KennethDoerflein/ESP32Clock/src/AlarmManager.cpp

/**
 * @file AlarmManager.cpp
 * @brief Implements the AlarmManager class for handling alarm ringing logic.
 *
 * This file contains the implementation of the AlarmManager, which controls
 * the physical buzzer, manages the alarm sound progression (ramping), and
 * handles auto-shutoff and resuming alarms after a reboot.
 */

#include "AlarmManager.h"
#include "Display.h"
#include "DisplayManager.h"
#include "SerialLog.h"
#include "ConfigManager.h"
#include "Constants.h"
#include "LockGuard.h"

/**
 * @brief Private constructor to enforce the singleton pattern.
 */
AlarmManager::AlarmManager() : _isRinging(false), _activeAlarmId(-1), _resumeElapsedSeconds(0), _alarmStartMillis(0)
{
  _mutex = xSemaphoreCreateRecursiveMutex();
}

/**
 * @brief Initializes the AlarmManager.
 *
 * Sets up the buzzer pin and checks if an alarm was ringing when the device
 * was last powered off. If so, it schedules a deferred resume of the alarm.
 */
void AlarmManager::begin()
{
  pinMode(BUZZER_PIN, OUTPUT);
  digitalWrite(BUZZER_PIN, LOW);

  // --- Check for a ringing alarm at startup ---
  int8_t ringingAlarmId = ConfigManager::getInstance().getRingingAlarmId();
  if (ringingAlarmId != -1)
  {
    RecursiveLockGuard lock(_mutex);
    _resumeAlarmOnBoot = true;
    _pendingResumeAlarmId = ringingAlarmId;
    _pendingResumeTimestamp = ConfigManager::getInstance().getRingingAlarmStartTimestamp();
    SerialLog::getInstance().print("AlarmManager: Pending resume for alarm.\n");
  }
}

/**
 * @brief Updates the state of the ringing alarm.
 *
 * This method should be called in the main loop. It handles the progressive
 * ramping of the alarm sound, from slow beeps to a continuous tone. It also
 * contains the logic for automatically shutting off the alarm after a prolonged
 * period.
 */
void AlarmManager::update()
{
  bool shouldResume = false;
  uint8_t resumeId = 0;
  uint32_t resumeTs = 0;

  {
    RecursiveLockGuard lock(_mutex);
    // --- Handle deferred resume first ---
    // To ensure the system is fully stable, especially the display driver,
    // the deferred resume operation is delayed for a few seconds after boot.
    if (_resumeAlarmOnBoot && millis() > ALARM_RESUME_DELAY_MS)
    {
      shouldResume = true;
      resumeId = _pendingResumeAlarmId;
      resumeTs = _pendingResumeTimestamp;
      _resumeAlarmOnBoot = false; // Clear the flag
    }
  }

  if (shouldResume)
  {
    time_t nowT = time(nullptr);
    uint32_t currentEpoch = (nowT > 100000) ? (uint32_t)nowT : TimeManager::getInstance().getRTCTime().unixtime();
    resume(resumeId, resumeTs, currentEpoch);
  }

  RecursiveLockGuard lock(_mutex);

  if (!_isRinging)
  {
    return;
  }

  // --- Stage Progression Logic ---
  // Use millis() for tracking elapsed time while ringing to avoid infinite ring
  // if the RTC loses power or I2C bus hangs and returns epoch 0.
  uint32_t alarmElapsedSeconds = _resumeElapsedSeconds + ((millis() - _alarmStartMillis) / 1000);

  // --- Auto-off Logic ---
  if (alarmElapsedSeconds >= ALARM_AUTO_OFF_SECONDS)
  {
    SerialLog::getInstance().print("AlarmManager: Auto-stopping alarm after 30 minutes.\n");
    stop();
    return;
  }

  if (_rampStage == STAGE_SLOW_BEEP && alarmElapsedSeconds >= (STAGE1_DURATION_MS / 1000))
  {
    SerialLog::getInstance().print("AlarmManager: Ramping to STAGE_FAST_BEEP\n");
    _rampStage = STAGE_FAST_BEEP;
  }
  else if (_rampStage == STAGE_FAST_BEEP && alarmElapsedSeconds >= ((STAGE1_DURATION_MS + STAGE2_DURATION_MS) / 1000))
  {
    SerialLog::getInstance().print("AlarmManager: Ramping to STAGE_CONTINUOUS\n");
    _rampStage = STAGE_CONTINUOUS;
    digitalWrite(BUZZER_PIN, HIGH); // Turn buzzer on permanently for this stage
    return;                         // Skip beeping logic
  }

  if (_rampStage == STAGE_CONTINUOUS)
  {
    return; // Buzzer is already on
  }

  // --- Beeping Logic ---
  unsigned long currentTime = millis();
  unsigned long beepOnDuration = (_rampStage == STAGE_SLOW_BEEP) ? SLOW_BEEP_ON_MS : FAST_BEEP_ON_MS;
  unsigned long beepOffDuration = (_rampStage == STAGE_SLOW_BEEP) ? SLOW_BEEP_OFF_MS : FAST_BEEP_OFF_MS;
  unsigned long beepElapsedTime = currentTime - _lastBeepTime;

  if (_buzzerState == BEEP_ON)
  {
    if (beepElapsedTime >= beepOnDuration)
    {
      _buzzerState = BEEP_OFF;
      _lastBeepTime = currentTime;
      digitalWrite(BUZZER_PIN, LOW);
    }
  }
  else // BEEP_OFF
  {
    if (beepElapsedTime >= beepOffDuration)
    {
      _buzzerState = BEEP_ON;
      _lastBeepTime = currentTime;
      digitalWrite(BUZZER_PIN, HIGH);
    }
  }
}

/**
 * @brief Stops the currently ringing alarm.
 *
 * This function deactivates the buzzer, resets the alarm state machine,
 * and clears the persisted ringing state from the configuration. It also
 * stops the backlight from flashing.
 */
void AlarmManager::stop()
{
  int alarmIdToStop = -1;
  {
    RecursiveLockGuard lock(_mutex);
    if (!_isRinging)
      return;

    alarmIdToStop = _activeAlarmId;
    _isRinging = false;
    _activeAlarmId = -1;
    
    // --- Reset state machine ---
    _rampStage = STAGE_SLOW_BEEP;
    _buzzerState = BEEP_OFF;
  } // Release mutex before calling out to other managers

  SerialLog::getInstance().printf("Stopping alarm ID %d\n", alarmIdToStop);
  digitalWrite(BUZZER_PIN, LOW); // Ensure buzzer is off

  auto &config = ConfigManager::getInstance();

  // If this was a one-time alarm, disable it unless it was snoozed
  // (if snoozed, it will ring again and eventually be fully stopped)
  Alarm alarm = config.getAlarmById(alarmIdToStop);
  if (alarm.getId() != 255)
  {
    if (alarm.getDays() == 0 && !alarm.isSnoozed())
    {
      alarm.setEnabled(false);
      config.setAlarmById(alarmIdToStop, alarm);
    }
    else if (alarm.getDays() != 0 && !alarm.isSnoozed())
    {
      // Repeating alarm: dismiss it so it doesn't re-trigger as missed on reboot
      alarm.dismiss(TimeManager::getInstance().getLocalTime());
      config.setAlarmById(alarmIdToStop, alarm);
    }
  }

  // --- Clear the persisted ringing state ---
  config.setRingingAlarmId(-1);
  config.setRingingAlarmStartTimestamp(0);
  config.saveRingingAlarmState(); // Persist the change immediately
  // Also save general config in case the alarm was modified (disabled)
  config.save();

  Display::getInstance().setBacklightFlashing(false);

  // Refresh display to clear alarm overlay
  DisplayManager::getInstance().requestPartialRefresh();
  
  // Check if we missed any alarms while this one was ringing
  TimeManager::getInstance().checkMissedAlarms();
}

/**
 * @brief Checks if an alarm is currently ringing.
 * @return True if an alarm is active, false otherwise.
 */
bool AlarmManager::isRinging() const
{
  RecursiveLockGuard lock(_mutex);
  return _isRinging;
}

/**
 * @brief Checks if a deferred resume is pending.
 * @return True if a resume is pending, false otherwise.
 */
bool AlarmManager::isResumePending() const
{
  RecursiveLockGuard lock(_mutex);
  return _resumeAlarmOnBoot;
}

/**
 * @brief Gets the ID of the currently active alarm.
 * @return The ID of the alarm, or -1 if no alarm is ringing.
 */
int AlarmManager::getActiveAlarmId() const
{
  RecursiveLockGuard lock(_mutex);
  return _activeAlarmId;
}

/**
 * @brief Triggers a new alarm to start ringing.
 *
 * This function initiates the alarm sequence. It sets up the state machine
 * for the ramping sound, persists the ringing state to handle reboots, and
 * activates the visual feedback on the display.
 *
 * @param alarmId The ID of the alarm to trigger.
 */
bool AlarmManager::trigger(uint8_t alarmId, uint32_t currentEpoch)
{
  if (currentEpoch == 0)
  {
    time_t nowT = time(nullptr);
    currentEpoch = (nowT > 100000) ? (uint32_t)nowT : TimeManager::getInstance().getRTCTime().unixtime();
  }

  uint32_t alarmStartTs = 0;
  {
    RecursiveLockGuard lock(_mutex);
    if (_isRinging)
      return false; // Don't trigger if another is already active

    SerialLog::getInstance().printf("Triggering alarm ID %d\n", alarmId);

    // --- Initialize the ramping alarm state ---
    _alarmStartTimestamp = currentEpoch;
    alarmStartTs = _alarmStartTimestamp;
    _alarmStartMillis = millis();
    _resumeElapsedSeconds = 0;
    _lastBeepTime = millis();
    _rampStage = STAGE_SLOW_BEEP;
    _buzzerState = BEEP_ON;
    digitalWrite(BUZZER_PIN, HIGH); // Start with the buzzer on
    _isRinging = true;
    _activeAlarmId = alarmId;
  }

  // --- Persist the ringing state ---
  auto &config = ConfigManager::getInstance();
  config.setRingingAlarmId(alarmId);
  config.setRingingAlarmStartTimestamp(alarmStartTs);
  config.saveRingingAlarmState(); // Persist the change immediately

  // Flash backlight
  Display::getInstance().setBacklightFlashing(true);

  // Update display immediately to show alarm overlay
  DisplayManager::getInstance().requestPartialRefresh();
  
  return true;
}

/**
 * @brief Resumes an alarm that was ringing before a reboot.
 *
 * This function is called at startup if a ringing alarm was detected in
 * the saved configuration. It recalculates the current ramp stage based on
 * the original start time and continues the alarm sequence.
 *
 * @param alarmId The ID of the alarm to resume.
 * @param startTimestamp The original Unix timestamp when the alarm started.
 * @param currentEpoch The current UTC epoch timestamp (fetched outside mutex).
 */
void AlarmManager::resume(uint8_t alarmId, uint32_t startTimestamp, uint32_t currentEpoch)
{
  if (currentEpoch == 0)
  {
    time_t nowT = time(nullptr);
    currentEpoch = (nowT > 100000) ? (uint32_t)nowT : TimeManager::getInstance().getRTCTime().unixtime();
  }

  RecursiveLockGuard lock(_mutex);
  if (_isRinging)
    return;

  SerialLog::getInstance().printf("Resuming ringing alarm ID %d\n", alarmId);
  _isRinging = true;
  _activeAlarmId = alarmId;
  _alarmStartTimestamp = startTimestamp;

  // We don't know the buzzer state from before the reboot, so start it
  _alarmStartMillis = millis();
  _lastBeepTime = millis();

  // Re-evaluate the ramp stage based on how long it's been ringing.
  uint32_t now = currentEpoch;
  
  // Guard: if RTC lost power and returned epoch 0, elapsed time wraps.
  // In this case, start fresh from STAGE_SLOW_BEEP to be safe.
  uint32_t alarmElapsedSeconds = 0;
  if (now < 1704067200 || now < _alarmStartTimestamp) { // 1704067200 = 2024-01-01
    SerialLog::getInstance().print("AlarmManager: RTC time invalid at resume, starting from STAGE_SLOW_BEEP.\n");
    _rampStage = STAGE_SLOW_BEEP;
    _resumeElapsedSeconds = 0;
  } else {
    alarmElapsedSeconds = now - _alarmStartTimestamp;
    
    // Check if the alarm has already exceeded the auto-off time
    if (alarmElapsedSeconds >= ALARM_AUTO_OFF_SECONDS) {
      SerialLog::getInstance().print("AlarmManager: Resumed alarm already exceeded auto-off time. Silently clearing.\n");
      _isRinging = false;
      _activeAlarmId = -1;
      auto &config = ConfigManager::getInstance();
      config.setRingingAlarmId(-1);
      config.setRingingAlarmStartTimestamp(0);
      config.saveRingingAlarmState();
      return;
    }
    
    _resumeElapsedSeconds = alarmElapsedSeconds;

    if (alarmElapsedSeconds >= ((STAGE1_DURATION_MS + STAGE2_DURATION_MS) / 1000))
    {
      _rampStage = STAGE_CONTINUOUS;
    }
    else if (alarmElapsedSeconds >= (STAGE1_DURATION_MS / 1000))
    {
      _rampStage = STAGE_FAST_BEEP;
    }
    else
    {
      _rampStage = STAGE_SLOW_BEEP;
    }
  }
  
  _buzzerState = BEEP_ON;
  digitalWrite(BUZZER_PIN, HIGH);
  
  SerialLog::getInstance().printf("Resumed at ramp stage %d\n", _rampStage);

  // Flash backlight
  Display::getInstance().setBacklightFlashing(true);

  // Update display immediately to show alarm overlay
  DisplayManager::getInstance().requestPartialRefresh();
}
