KennethDoerflein/ESP32Clock/src/WeatherService.cpp

#include "WeatherService.h"
#include "ConfigManager.h"
#include "SerialLog.h"
#include "TimeManager.h"
#include <WiFi.h>
#include <WiFiClientSecure.h>
#include <HTTPClient.h>
#include <ArduinoJson.h>
#include "LockGuard.h"
#include <esp_task_wdt.h>
#include <esp_heap_caps.h>

struct SpiRamAllocator : ArduinoJson::Allocator
{
  void* allocate(size_t size) override
  {
    void* p = heap_caps_malloc(size, MALLOC_CAP_SPIRAM | MALLOC_CAP_8BIT);
    if (!p)
    {
      p = malloc(size);
    }
    return p;
  }

  void deallocate(void* ptr) override
  {
    free(ptr);
  }

  void* reallocate(void* ptr, size_t new_size) override
  {
    void* p = heap_caps_realloc(ptr, new_size, MALLOC_CAP_SPIRAM | MALLOC_CAP_8BIT);
    if (!p)
    {
      p = realloc(ptr, new_size);
    }
    return p;
  }
};

static SpiRamAllocator g_spiRamAllocator;

static const unsigned long WEATHER_UPDATE_INTERVAL = 10 * 60 * 1000; // 10 minutes
static const uint32_t MIN_CONTIGUOUS_HEAP_FOR_TLS = 38000; // Minimum contiguous heap (bytes) to attempt TLS
static const uint8_t MAX_CONSECUTIVE_FAILURES = 6; // Invalidate stale data after this many failures

WeatherService::WeatherService() : _lastUpdate(0), _weatherTaskHandle(NULL)
{
  _mutex = xSemaphoreCreateMutex();
  _wakeSignal = xSemaphoreCreateBinary();
}

/**
 * @brief Creates the persistent weather task. Called once at boot.
 *
 * The task runs forever on Core 0, sleeping on a binary semaphore between
 * updates. This avoids the heap fragmentation caused by repeatedly creating
 * and destroying a 32KB task every 10 minutes.
 */
void WeatherService::begin()
{
  _geocodingResult.pending = false;
  _geocodingResult.success = false;
  
  xTaskCreatePinnedToCore(
      weatherTaskEntry,    // Persistent task entry point
      "WeatherUpdate",     // Name of the task
      20480,               // Stack size (20KB for HTTPS + JSON in PSRAM)
      this,                // Task input parameter
      1,                   // Priority
      &_weatherTaskHandle, // Task handle
      1                    // Core 1 (prevents IDLE0 starvation on Core 0)
  );
  SerialLog::getInstance().print("Weather task created (persistent).\n");
}

/**
 * @brief Persistent weather task entry point. Runs forever.
 *
 * Enrolls in WDT, waits on a binary semaphore, performs the update, then
 * sleeps again. The semaphore is given by loop() on a timer or by forceUpdate().
 */
void WeatherService::weatherTaskEntry(void *parameter)
{
  WeatherService *service = static_cast<WeatherService *>(parameter);

  for (;;)
  {
    // Sleep until signaled to update (with a timeout as a safety net).
    // WDT is enrolled unconditionally around each wake cycle so that any
    // code path that runs network I/O is covered without leaving orphaned
    // enrollments if WiFi state changes mid-execution.
    xSemaphoreTake(service->_wakeSignal, pdMS_TO_TICKS(WEATHER_UPDATE_INTERVAL + 30000));

    esp_task_wdt_add(NULL);

    // Wait for WiFi to be available, retrying up to ~30 s in 5 s increments.
    // This handles the boot-time race where the wake signal fires before the
    // WiFi stack has finished associating.
    static const int WIFI_RETRY_COUNT = 6;
    static const TickType_t WIFI_RETRY_DELAY = pdMS_TO_TICKS(5000);
    bool wifiReady = false;
    for (int attempt = 0; attempt < WIFI_RETRY_COUNT; ++attempt)
    {
      if (WiFi.status() == WL_CONNECTED)
      {
        wifiReady = true;
        break;
      }
      if (attempt == 0)
      {
        SerialLog::getInstance().print("Weather task: WiFi not ready, waiting...\n");
      }
      vTaskDelay(WIFI_RETRY_DELAY);
      esp_task_wdt_reset(); // Keep WDT happy during the wait
    }

    if (wifiReady)
    {
      // 1. Check for pending geocoding request
      String query;
      bool hasGeocoding = false;
      {
          LockGuard lock(service->_mutex);
          if (service->_geocodingResult.pending) {
              query = service->_geocodingQuery;
              hasGeocoding = true;
          }
      }

      if (hasGeocoding) {
          SerialLog::getInstance().printf("Weather task: processing geocoding for '%s'\n", query.c_str());
          String resolved;
          float lat = 0.0f, lon = 0.0f;
          bool success = service->resolveLocation(query, resolved, lat, lon);

          if (success) {
              ConfigManager::getInstance().setAddress(resolved);
              ConfigManager::getInstance().setLat(lat);
              ConfigManager::getInstance().setLon(lon);
              SerialLog::getInstance().printf("Weather task: location saved: %s (%.4f, %.4f)\n", resolved.c_str(), lat, lon);
          }

          {
              LockGuard lock(service->_mutex);
              service->_geocodingResult.success = success;
              service->_geocodingResult.resolvedAddress = resolved;
              service->_geocodingResult.lat = lat;
              service->_geocodingResult.lon = lon;
              service->_geocodingResult.pending = false;
          }
          SerialLog::getInstance().printf("Weather task: geocoding %s\n", success ? "succeeded" : "failed");
      }

      esp_task_wdt_reset(); // Feed the WDT between geocoding and weather updates

      // 2. Regular weather update
      SerialLog::getInstance().print("Weather task: starting weather update...\n");
      service->updateWeather();
    }
    else
    {
      SerialLog::getInstance().print("Weather task: WiFi unavailable after retries, skipping update.\n");
    }

    // Always unenroll from WDT before going back to sleep — the task may sleep
    // for up to WEATHER_UPDATE_INTERVAL minutes and must not hold a WDT slot.
    esp_task_wdt_delete(NULL);

    // Small yield to prevent tight looping on rapid semaphore gives
    vTaskDelay(pdMS_TO_TICKS(100));
  }
}

/**
 * @brief Called periodically from logicTask. Signals the persistent weather
 *        task to wake up when the update interval has elapsed.
 */
void WeatherService::loop()
{
  if (WiFi.status() != WL_CONNECTED)
    return;

  unsigned long now = millis();

  LockGuard lock(_mutex);
  uint32_t interval = WEATHER_UPDATE_INTERVAL;
  if (_failureCount > 0)
  {
    // Exponential backoff: 1 fail = 10m, 2 = 20m, 3 = 40m, max 2 hours
    interval = (uint32_t)WEATHER_UPDATE_INTERVAL * (1 << (std::min((int)_failureCount, 4)));
    if (interval > 2 * 60 * 60 * 1000) interval = 2 * 60 * 60 * 1000;
  }

  if (now - _lastUpdate > interval || _lastUpdate == 0)
  {
    _lastUpdate = now;
    xSemaphoreGive(_wakeSignal); // Wake the persistent task
  }
}

void WeatherService::forceUpdate()
{
  LockGuard lock(_mutex);
  _lastUpdate = 0;
  xSemaphoreGive(_wakeSignal); // Wake the persistent task immediately
}

WeatherData WeatherService::getCurrentWeather() const
{
  LockGuard lock(_mutex);
  return _currentWeather;
}

struct StateMap
{
  const char *name;
  const char *code;
};

const StateMap US_STATES[] = {
    {"alabama", "al"}, {"alaska", "ak"}, {"arizona", "az"}, {"arkansas", "ar"}, {"california", "ca"}, {"colorado", "co"}, {"connecticut", "ct"}, {"delaware", "de"}, {"florida", "fl"}, {"georgia", "ga"}, {"hawaii", "hi"}, {"idaho", "id"}, {"illinois", "il"}, {"indiana", "in"}, {"iowa", "ia"}, {"kansas", "ks"}, {"kentucky", "ky"}, {"louisiana", "la"}, {"maine", "me"}, {"maryland", "md"}, {"massachusetts", "ma"}, {"michigan", "mi"}, {"minnesota", "mn"}, {"mississippi", "ms"}, {"missouri", "mo"}, {"montana", "mt"}, {"nebraska", "ne"}, {"nevada", "nv"}, {"new hampshire", "nh"}, {"new jersey", "nj"}, {"new mexico", "nm"}, {"new york", "ny"}, {"north carolina", "nc"}, {"north dakota", "nd"}, {"ohio", "oh"}, {"oklahoma", "ok"}, {"oregon", "or"}, {"pennsylvania", "pa"}, {"rhode island", "ri"}, {"south carolina", "sc"}, {"south dakota", "sd"}, {"tennessee", "tn"}, {"texas", "tx"}, {"utah", "ut"}, {"vermont", "vt"}, {"virginia", "va"}, {"washington", "wa"}, {"west virginia", "wv"}, {"wisconsin", "wi"}, {"wyoming", "wy"}, {"district of columbia", "dc"}};

// Helper function for the search logic
bool performGeocodingSearch(String url, String context, String &resolvedAddress, float &lat, float &lon)
{
  if (WiFi.status() != WL_CONNECTED)
  {
    SerialLog::getInstance().print("Geocoding: WiFi not connected, aborting\n");
    return false;
  }

  uint32_t maxAllocHeap = ESP.getMaxAllocHeap();
  if (maxAllocHeap < MIN_CONTIGUOUS_HEAP_FOR_TLS)
  {
    SerialLog::getInstance().printf("Geocoding: max alloc heap too low (%u), aborting\n", maxAllocHeap);
    return false;
  }

  WiFiClientSecure client;
  HTTPClient http;
  client.setInsecure();
  client.setTimeout(5000);  // 5s cap on TLS handshake (milliseconds)

  SerialLog::getInstance().printf("Resolving Location: %s\n", url.c_str());

  if (!http.begin(client, url))
  {
    SerialLog::getInstance().print("Geocoding: http.begin failed\n");
    return false;
  }

  http.setFollowRedirects(HTTPC_FORCE_FOLLOW_REDIRECTS);
  http.useHTTP10(true);    // Disable chunked transfer encoding for stream safety
  http.setTimeout(5000);   // 5s HTTP timeout

  esp_task_wdt_delete(NULL); // Unenroll before blocking I/O — TLS handshake + response stream
  int httpCode = http.GET();
  bool success = false;

  if (httpCode == 200)
  {
    // Create a filter to only deserialize what we need
    JsonDocument filter;
    filter["results"][0]["name"] = true;
    filter["results"][0]["latitude"] = true;
    filter["results"][0]["longitude"] = true;
    filter["results"][0]["country"] = true;
    filter["results"][0]["country_code"] = true;
    filter["results"][0]["admin1"] = true;

    JsonDocument doc(&g_spiRamAllocator);
    DeserializationError error = deserializeJson(doc, http.getStream(), DeserializationOption::Filter(filter));
    http.end();

    if (!error)
    {
      if (doc["results"].is<JsonArray>())
      {
        JsonArray results = doc["results"].as<JsonArray>();
        if (results.size() > 0)
        {
          int bestIndex = 0;

          // If we have a context string (e.g. "Paris, Texas"), try to find the best scoring match
          if (context.length() > 0)
          {
            String contextLower = context;
            contextLower.toLowerCase();
            int maxScore = -1;

            for (size_t i = 0; i < results.size(); i++)
            {
              String country = results[i]["country"].isNull() ? "" : results[i]["country"].as<String>();
              String countryCode = results[i]["country_code"].isNull() ? "" : results[i]["country_code"].as<String>();
              String admin1 = results[i]["admin1"].isNull() ? "" : results[i]["admin1"].as<String>();
              country.toLowerCase();
              admin1.toLowerCase();

              int score = 0;

              // Direct matches
              if (admin1.length() > 0 && contextLower.indexOf(admin1) != -1)
              {
                score += 10;
              }
              if (country.length() > 0 && contextLower.indexOf(country) != -1)
              {
                score += 1;
              }

              // Abbreviation match for US
              if (countryCode == "US" && admin1.length() > 0)
              {
                for (const auto &state : US_STATES)
                {
                  if (admin1 == state.name)
                  {
                    if (checkWordPresence(contextLower, state.code))
                    {
                      score += 10;
                    }
                    break;
                  }
                }
              }

              if (score > maxScore)
              {
                maxScore = score;
                bestIndex = i;
              }
            }
            if (maxScore > 0)
            {
              SerialLog::getInstance().printf("Best context match at index %d (Score: %d)\n", bestIndex, maxScore);
            }
          }

          if (!results[bestIndex]["latitude"].isNull() && !results[bestIndex]["longitude"].isNull() && !results[bestIndex]["name"].isNull())
          {
            lat = results[bestIndex]["latitude"].as<float>();
            lon = results[bestIndex]["longitude"].as<float>();

            String name = results[bestIndex]["name"].as<String>();
            String country = results[bestIndex]["country"].isNull() ? "" : results[bestIndex]["country"].as<String>();
            String admin1 = results[bestIndex]["admin1"].isNull() ? "" : results[bestIndex]["admin1"].as<String>();

            resolvedAddress = name;
            if (admin1.length() > 0 && admin1 != name)
              resolvedAddress += ", " + admin1;
            if (country.length() > 0)
              resolvedAddress += ", " + country;

            success = true;
            SerialLog::getInstance().printf("Found: %s (%.4f, %.4f)\n", resolvedAddress.c_str(), lat, lon);
          }
          else
          {
            SerialLog::getInstance().print("Geocoding result missing required lat/lon/name fields.\n");
          }
        }
        else
        {
          SerialLog::getInstance().print("No results in Geocoding response.\n");
        }
      }
      else
      {
        SerialLog::getInstance().print("Geocoding JSON missing 'results' array.\n");
      }
    }
    else
    {
      SerialLog::getInstance().printf("Geocoding JSON Error: %s\n", error.c_str());
    }
  }
  else
  {
    SerialLog::getInstance().printf("Geocoding HTTP Failed: %d\n", httpCode);
    http.end();
  }

  esp_task_wdt_add(NULL);    // Re-enroll after blocking network I/O
  esp_task_wdt_reset();      // Feed immediately
  return success;
}

bool WeatherService::resolveLocationAsync(const String &query)
{
  if (WiFi.status() != WL_CONNECTED || query.length() == 0)
    return false;

  LockGuard lock(_mutex);
  if (_geocodingResult.pending)
    return false; // Already pending

  _geocodingQuery = query;
  _geocodingResult.pending = true;
  _geocodingResult.success = false;

  // Wake the background task
  xSemaphoreGive(_wakeSignal);
  return true;
}

WeatherService::GeocodingResult WeatherService::getGeocodingResult()
{
  LockGuard lock(_mutex);
  return _geocodingResult;
}

// Internal worker called by updateLocation() or geocoding task logic
bool WeatherService::resolveLocation(const String &query, String &resolvedAddress, float &lat, float &lon)
{
  if (WiFi.status() != WL_CONNECTED || query.length() == 0)
    return false;

  String url = "https://geocoding-api.open-meteo.com/v1/search?name=" + urlEncode(query) + "&count=1&language=en&format=json";

  if (performGeocodingSearch(url, "", resolvedAddress, lat, lon))
  {
    return true;
  }

  esp_task_wdt_reset(); // Feed WDT between geocoding attempts

  int commaIndex = query.indexOf(',');
  if (commaIndex != -1)
  {
    String city = query.substring(0, commaIndex);
    url = "https://geocoding-api.open-meteo.com/v1/search?name=" + urlEncode(city) + "&count=10&language=en&format=json";

    if (performGeocodingSearch(url, query, resolvedAddress, lat, lon))
    {
      return true;
    }
  }

  return false;
}

void WeatherService::updateLocation()
{
  String address = ConfigManager::getInstance().getAddress();
  if (address.length() == 0)
    return;

  SerialLog::getInstance().printf("Updating location for: %s\n", address.c_str());

  String resolved;
  float lat = 0.0f, lon = 0.0f;

  if (resolveLocation(address, resolved, lat, lon))
  {
    ConfigManager::getInstance().setLat(lat);
    ConfigManager::getInstance().setLon(lon);
    SerialLog::getInstance().printf("Location resolved: %s (%.4f, %.4f)\n", resolved.c_str(), lat, lon);
    esp_task_wdt_reset(); // Feed WDT before chained weather update
    updateWeather();
  }
  else
  {
    SerialLog::getInstance().print("Failed to resolve location.\n");
    LockGuard lock(_mutex);
    if (_failureCount < UINT8_MAX) _failureCount++;
    if (_failureCount >= MAX_CONSECUTIVE_FAILURES && _currentWeather.isValid)
    {
      _currentWeather.isValid = false;
      SerialLog::getInstance().print("Weather: data invalidated (failed location resolution)\n");
    }
  }
}

void WeatherService::updateWeather()
{
  if (WiFi.status() != WL_CONNECTED)
    return;

  // Guard: ensure sufficient contiguous heap for TLS (~38KB needed for mbedTLS buffers)
  uint32_t maxAllocHeap = ESP.getMaxAllocHeap();
  if (maxAllocHeap < MIN_CONTIGUOUS_HEAP_FOR_TLS)
  {
    SerialLog::getInstance().printf("Weather: max alloc heap too low (%u), skipping update\n", maxAllocHeap);
    LockGuard lock(_mutex);
    if (_failureCount < UINT8_MAX) _failureCount++;
    if (_failureCount >= MAX_CONSECUTIVE_FAILURES && _currentWeather.isValid)
    {
      _currentWeather.isValid = false;
      SerialLog::getInstance().print("Weather: data invalidated (too many consecutive failures)\n");
    }
    return;
  }

  float lat = ConfigManager::getInstance().getLat();
  float lon = ConfigManager::getInstance().getLon();

  if (lat == 0.0f && lon == 0.0f)
  {
    // Try to get location if we have address
    if (ConfigManager::getInstance().getAddress().length() > 0)
    {
      updateLocation();
      return;
    }
    return; // No location data
  }

  // Fetch from Open-Meteo
  WiFiClientSecure client;
  HTTPClient http;
  client.setInsecure();
  client.setTimeout(5000);  // 5s cap on TLS handshake (milliseconds)

  // Use reserve to prevent reallocations
  String url;
  url.reserve(400); 

  url = "https://api.open-meteo.com/v1/forecast?latitude=";
  url += String(lat, 4);
  url += "&longitude=";
  url += String(lon, 4);
  url += "&current=temperature_2m,relative_humidity_2m,apparent_temperature,weather_code,wind_speed_10m,cloud_cover,pressure_msl,wind_direction_10m,wind_gusts_10m,uv_index,visibility,precipitation_probability&daily=sunrise,sunset&temperature_unit=fahrenheit&wind_speed_unit=mph&precipitation_unit=inch&forecast_days=1&timezone=auto";

  SerialLog::getInstance().printf("Fetching Weather: %s\n", url.c_str());
  SerialLog::getInstance().printf("Max Alloc Heap before Weather Update: %u\n", maxAllocHeap);

  if (!http.begin(client, url))
  {
    SerialLog::getInstance().print("Weather: http.begin failed\n");
    LockGuard lock(_mutex);
    if (_failureCount < UINT8_MAX) _failureCount++;
    if (_failureCount >= MAX_CONSECUTIVE_FAILURES && _currentWeather.isValid)
    {
      _currentWeather.isValid = false;
      SerialLog::getInstance().print("Weather: data invalidated (too many consecutive failures)\n");
    }
    return;
  }

  http.setFollowRedirects(HTTPC_FORCE_FOLLOW_REDIRECTS);
  http.useHTTP10(true);                                  // Disable chunked transfer encoding for stream safety
  http.setTimeout(5000);                                 // 5s HTTP timeout

  esp_task_wdt_delete(NULL); // Unenroll before blocking I/O — TLS handshake + response stream
  int httpCode = http.GET();

  if (httpCode == 200)
  {
    JsonDocument doc(&g_spiRamAllocator);

    // Filter to reduce memory usage
    JsonDocument filter;
    filter["current"]["temperature_2m"] = true;
    filter["current"]["apparent_temperature"] = true;
    filter["current"]["relative_humidity_2m"] = true;
    filter["current"]["wind_speed_10m"] = true;
    filter["current"]["weather_code"] = true;

    filter["current"]["cloud_cover"] = true;
    filter["current"]["pressure_msl"] = true;
    filter["current"]["wind_direction_10m"] = true;
    filter["current"]["wind_gusts_10m"] = true;

    filter["current"]["uv_index"] = true;
    filter["current"]["visibility"] = true;
    filter["current"]["precipitation_probability"] = true;

    filter["daily"]["sunrise"] = true;
    filter["daily"]["sunset"] = true;

    DeserializationError error = deserializeJson(doc, http.getStream(), DeserializationOption::Filter(filter));
    http.end(); // Release connection early so we free network resources immediately

    esp_task_wdt_add(NULL);    // Re-enroll after blocking I/O
    esp_task_wdt_reset();      // Feed immediately

    if (!error)
    {
      if (doc["current"].is<JsonObject>() &&
          !doc["current"]["temperature_2m"].isNull() &&
          !doc["current"]["weather_code"].isNull())
      {
        float temp = doc["current"]["temperature_2m"].as<float>();
        float feelsLike = doc["current"]["apparent_temperature"].isNull() ? temp : doc["current"]["apparent_temperature"].as<float>();
        float humidity = doc["current"]["relative_humidity_2m"].isNull() ? 0.0f : doc["current"]["relative_humidity_2m"].as<float>();
        float windSpeed = doc["current"]["wind_speed_10m"].isNull() ? 0.0f : doc["current"]["wind_speed_10m"].as<float>();
        int code = doc["current"]["weather_code"].as<int>();

        int cloudCover = doc["current"]["cloud_cover"] | 0;
        float pressure = doc["current"]["pressure_msl"] | 0.0f;
        int windDirection = doc["current"]["wind_direction_10m"] | 0;
        float windGusts = doc["current"]["wind_gusts_10m"] | 0.0f;

        int rainChance = doc["current"]["precipitation_probability"] | 0;
        float uvIndex = doc["current"]["uv_index"] | 0.0f;
        float visibility = doc["current"]["visibility"] | 0.0f;

        String sunrise = "";
        String sunset = "";
        if (doc["daily"].is<JsonObject>())
        {
          if (doc["daily"]["sunrise"].is<JsonArray>() && doc["daily"]["sunrise"].size() > 0)
          {
            if (!doc["daily"]["sunrise"][0].isNull())
            {
              String raw = doc["daily"]["sunrise"][0].as<String>();
              int tIndex = raw.indexOf('T');
              if (tIndex != -1)
                sunrise = raw.substring(tIndex + 1);
              else
                sunrise = raw;
            }
          }
          if (doc["daily"]["sunset"].is<JsonArray>() && doc["daily"]["sunset"].size() > 0)
          {
            if (!doc["daily"]["sunset"][0].isNull())
            {
              String raw = doc["daily"]["sunset"][0].as<String>();
              int tIndex = raw.indexOf('T');
              if (tIndex != -1)
                sunset = raw.substring(tIndex + 1);
              else
                sunset = raw;
            }
          }
        }

        {
          LockGuard lock(_mutex);
          _currentWeather.temp = temp;
          _currentWeather.feelsLike = feelsLike;
          _currentWeather.humidity = humidity;
          _currentWeather.windSpeed = windSpeed;
          _currentWeather.rainChance = rainChance;
          strncpy(_currentWeather.condition, getConditionFromWMO(code), sizeof(_currentWeather.condition) - 1);
          _currentWeather.condition[sizeof(_currentWeather.condition) - 1] = '\0';

          _currentWeather.uvIndex = uvIndex;
          _currentWeather.cloudCover = cloudCover;
          _currentWeather.pressure = pressure;
          _currentWeather.visibility = visibility;
          _currentWeather.windDirection = windDirection;
          _currentWeather.windGusts = windGusts;
          strncpy(_currentWeather.sunrise, sunrise.c_str(), sizeof(_currentWeather.sunrise) - 1);
          _currentWeather.sunrise[sizeof(_currentWeather.sunrise) - 1] = '\0';
          strncpy(_currentWeather.sunset, sunset.c_str(), sizeof(_currentWeather.sunset) - 1);
          _currentWeather.sunset[sizeof(_currentWeather.sunset) - 1] = '\0';

          _currentWeather.isValid = true;
          _failureCount = 0; // Success! Reset failures
        }

        SerialLog::getInstance().printf("Weather Updated: %.1fF, %s\n", temp, getConditionFromWMO(code));
      }
      else
      {
        SerialLog::getInstance().print("Weather JSON Error: missing 'current' object or required fields\n");
        LockGuard lock(_mutex);
        if (_failureCount < UINT8_MAX) _failureCount++;
        if (_failureCount >= MAX_CONSECUTIVE_FAILURES && _currentWeather.isValid)
        {
          _currentWeather.isValid = false;
          SerialLog::getInstance().print("Weather: data invalidated (too many consecutive failures)\n");
        }
      }
    }
    else
    {
      SerialLog::getInstance().printf("Weather JSON Error: %s\n", error.c_str());
      LockGuard lock(_mutex);
      if (_failureCount < UINT8_MAX) _failureCount++;
      if (_failureCount >= MAX_CONSECUTIVE_FAILURES && _currentWeather.isValid)
      {
        _currentWeather.isValid = false;
        SerialLog::getInstance().print("Weather: data invalidated (too many consecutive failures)\n");
      }
    }
  }
  else
  {
    String errorMsg = http.errorToString(httpCode);
    SerialLog::getInstance().printf("Weather HTTP Failed: %d (%s)\n", httpCode, errorMsg.c_str());
    http.end();
    esp_task_wdt_add(NULL);    // Re-enroll after blocking I/O
    esp_task_wdt_reset();      // Feed immediately
    LockGuard lock(_mutex);
    if (_failureCount < UINT8_MAX) _failureCount++;
    if (_failureCount >= MAX_CONSECUTIVE_FAILURES && _currentWeather.isValid)
    {
      _currentWeather.isValid = false;
      SerialLog::getInstance().print("Weather: data invalidated (too many consecutive failures)\n");
    }
  }
}
