KennethDoerflein/ESP32Clock/include/WebContent.h

#ifndef WEB_CONTENT_H
#define WEB_CONTENT_H

/**
 * @file WebContent.h
 * @brief Contains the HTML, CSS, and JavaScript for the web interface.
 *
 * All content is stored as C-style string literals in PROGMEM to conserve RAM.
 * The pages use a simple template system where placeholders like %VAR% are
 * replaced by dynamic content in the main C++ code.
 */

/**
 * @brief Common HTML head content, including Bootstrap 5 CSS and basic styling.
 * This is injected into every page using the `%HEAD%` placeholder.
 */
const char BOOTSTRAP_HEAD[] PROGMEM = R"rawliteral(
<meta charset="UTF-8">
<meta http-equiv="content-language" content="en-US">
<meta name="language" content="English">
<meta name="google" content="notranslate">
<meta name="viewport" content="width=device-width, initial-scale=1">
<link href="https://cdn.jsdelivr.net/npm/bootstrap@5.3.3/dist/css/bootstrap.min.css" rel="stylesheet">
<link rel="stylesheet" href="https://cdn.jsdelivr.net/npm/bootstrap-icons@1.13.1/font/bootstrap-icons.min.css" />
<style>
  .container { max-width: 600px; }
</style>
)rawliteral";

const char SERIAL_LOG_TAB_HTML[] PROGMEM = R"rawliteral(
<li class="nav-item" role="presentation">
  <button class="nav-link" id="serial-log-tab" data-bs-toggle="tab" data-bs-target="#serial-log" type="button" role="tab" aria-controls="serial-log" aria-selected="false">Logs</button>
</li>
)rawliteral";

const char WEATHER_PAGE_HTML[] PROGMEM = R"rawliteral(
<!DOCTYPE html>
<html data-bs-theme="dark">
<head>
  <title>Weather</title>
  %HEAD%
</head>
<body>
  <div class="container my-5">
    <div class="card shadow-sm">
      <div class="card-body">
        <h1 class="card-title text-center mb-4">Weather</h1>

        <div class="mb-4">
             <label for="location-input" class="form-label">Location</label>
             <div class="input-group">
                <input type="text" class="form-control" id="location-input" placeholder="e.g. New York, NY" value="%ADDRESS%">
                <button class="btn btn-outline-primary" type="button" id="save-location-btn">Save Location</button>
             </div>
        </div>
        
        <div class="text-center mb-4">
            <div id="weather-display" class="d-none">
                <h2 class="display-1"><span id="temp">--</span>&deg;<span id="unit"></span></h2>
                <h3 id="condition" class="text-muted">--</h3>
                
                <div class="row mt-4 g-3">
                  <div class="col-6 col-md-3">
                     <div class="p-2 border rounded bg-dark-subtle">
                       <div class="small text-muted mb-1"><i class="bi bi-thermometer-half"></i> Feels Like</div>
                       <div class="h5 mb-0"><span id="feels-like">--</span>&deg;</div>
                     </div>
                  </div>
                  <div class="col-6 col-md-3">
                     <div class="p-2 border rounded bg-dark-subtle">
                       <div class="small text-muted mb-1"><i class="bi bi-droplet-half"></i> Humidity</div>
                       <div class="h5 mb-0"><span id="humidity">--</span>%%</div>
                     </div>
                  </div>
                  <div class="col-6 col-md-3">
                     <div class="p-2 border rounded bg-dark-subtle">
                       <div class="small text-muted mb-1"><i class="bi bi-wind"></i> Wind</div>
                       <div class="h5 mb-0"><span id="wind-speed">--</span> <small id="wind-unit" class="text-muted" style="font-size: 0.7em"></small></div>
                     </div>
                  </div>
                  <div class="col-6 col-md-3">
                     <div class="p-2 border rounded bg-dark-subtle">
                       <div class="small text-muted mb-1"><i class="bi bi-cloud-rain"></i> Rain Chance</div>
                       <div class="h5 mb-0"><span id="rainChance">--</span>%%</div>
                     </div>
                  </div>
                  
                  <div class="col-6 col-md-3">
                     <div class="p-2 border rounded bg-dark-subtle">
                       <div class="small text-muted mb-1"><i class="bi bi-sun"></i> UV Index</div>
                       <div class="h5 mb-0"><span id="uvIndex">--</span></div>
                     </div>
                  </div>
                  <div class="col-6 col-md-3">
                     <div class="p-2 border rounded bg-dark-subtle">
                       <div class="small text-muted mb-1"><i class="bi bi-clouds"></i> Cloud Cover</div>
                       <div class="h5 mb-0"><span id="cloudCover">--</span>%%</div>
                     </div>
                  </div>
                  <div class="col-6 col-md-3">
                     <div class="p-2 border rounded bg-dark-subtle">
                       <div class="small text-muted mb-1"><i class="bi bi-eye"></i> Visibility</div>
                       <div class="h5 mb-0"><span id="visibility">--</span> <small class="text-muted" style="font-size: 0.7em">mi</small></div>
                     </div>
                  </div>
                  <div class="col-6 col-md-3">
                     <div class="p-2 border rounded bg-dark-subtle">
                       <div class="small text-muted mb-1"><i class="bi bi-speedometer2"></i> Pressure</div>
                       <div class="h5 mb-0"><span id="pressure">--</span> <small class="text-muted" style="font-size: 0.7em">hPa</small></div>
                     </div>
                  </div>

                  <div class="col-6 col-md-3">
                     <div class="p-2 border rounded bg-dark-subtle">
                       <div class="small text-muted mb-1"><i class="bi bi-compass"></i> Wind Dir</div>
                       <div class="h5 mb-0"><span id="windDirection">--</span></div>
                     </div>
                  </div>
                  <div class="col-6 col-md-3">
                     <div class="p-2 border rounded bg-dark-subtle">
                       <div class="small text-muted mb-1"><i class="bi bi-wind"></i> Gusts</div>
                       <div class="h5 mb-0"><span id="windGusts">--</span> <small id="gust-unit" class="text-muted" style="font-size: 0.7em"></small></div>
                     </div>
                  </div>
                  <div class="col-6 col-md-3">
                     <div class="p-2 border rounded bg-dark-subtle">
                       <div class="small text-muted mb-1"><i class="bi bi-sunrise"></i> Sunrise</div>
                       <div class="h5 mb-0"><span id="sunrise">--:--</span></div>
                     </div>
                  </div>
                  <div class="col-6 col-md-3">
                     <div class="p-2 border rounded bg-dark-subtle">
                       <div class="small text-muted mb-1"><i class="bi bi-sunset"></i> Sunset</div>
                       <div class="h5 mb-0"><span id="sunset">--:--</span></div>
                     </div>
                  </div>
                </div>

            </div>
            <div id="weather-error" class="d-none alert alert-warning">
                Weather data unavailable.
            </div>
        </div>

        <div class="d-grid gap-2">
            <button id="sync-btn" class="btn btn-primary btn-lg"><i class="bi bi-cloud-arrow-down-fill me-2"></i>Sync Now</button>
            <a href="/" class="btn btn-secondary" title="Return to the main menu.">Back to Menu</a>
        </div>
        <div class="mt-3 text-center">
            <small class="text-muted">Weather data provided by <a href="https://open-meteo.com/" target="_blank" class="link-secondary">open-meteo.com</a></small>
        </div>
      </div>
    </div>
  </div>
  <script>
    const tempEl = document.getElementById('temp');
    const unitEl = document.getElementById('unit');
    const conditionEl = document.getElementById('condition');
    const weatherDisplay = document.getElementById('weather-display');
    const weatherError = document.getElementById('weather-error');
    const syncBtn = document.getElementById('sync-btn');
    
    const feelsLikeEl = document.getElementById('feels-like');
    const humidityEl = document.getElementById('humidity');
    const windSpeedEl = document.getElementById('wind-speed');
    const windUnitEl = document.getElementById('wind-unit');
    const rainChanceEl = document.getElementById('rainChance');
    
    const uvIndexEl = document.getElementById('uvIndex');
    const cloudCoverEl = document.getElementById('cloudCover');
    const visibilityEl = document.getElementById('visibility');
    const pressureEl = document.getElementById('pressure');
    const windDirectionEl = document.getElementById('windDirection');
    const windGustsEl = document.getElementById('windGusts');
    const gustUnitEl = document.getElementById('gust-unit');
    const sunriseEl = document.getElementById('sunrise');
    const sunsetEl = document.getElementById('sunset');

    const locationInput = document.getElementById('location-input');
    const saveLocationBtn = document.getElementById('save-location-btn');

    saveLocationBtn.addEventListener('click', () => {
        const address = locationInput.value;
        saveLocationBtn.disabled = true;
        saveLocationBtn.innerHTML = '<span class="spinner-border spinner-border-sm me-2"></span>Saving...';
        
        const formData = new FormData();
        formData.append('address', address);

        fetch('/api/weather/location', { method: 'POST', body: formData })
            .then(response => response.json())
            .then(data => {
                 if (data.success) {
                     if (data.pending) {
                         pollGeocodingStatus();
                     } else {
                         finishSaveLocation(data.resolvedAddress);
                     }
                 } else {
                     alert(data.message || 'Failed to save location');
                     saveLocationBtn.disabled = false;
                     saveLocationBtn.textContent = 'Save Location';
                 }
            })
            .catch(e => {
                alert('Error: ' + e);
                saveLocationBtn.disabled = false;
                saveLocationBtn.textContent = 'Save Location';
            });
    });

    function pollGeocodingStatus() {
        fetch('/api/weather/geocoding-status')
            .then(response => response.json())
            .then(data => {
                if (data.pending) {
                    setTimeout(pollGeocodingStatus, 1000);
                } else if (data.success) {
                    finishSaveLocation(data.resolvedAddress);
                } else {
                    alert('Failed to resolve location.');
                    saveLocationBtn.disabled = false;
                    saveLocationBtn.textContent = 'Save Location';
                }
            })
            .catch(e => {
                alert('Error polling status: ' + e);
                saveLocationBtn.disabled = false;
                saveLocationBtn.textContent = 'Save Location';
            });
    }

    function finishSaveLocation(resolvedAddress) {
        saveLocationBtn.innerHTML = '<i class="bi bi-check-lg me-2"></i>Saved';
        saveLocationBtn.classList.remove('btn-outline-primary');
        saveLocationBtn.classList.add('btn-success');
        
        if (resolvedAddress) {
           locationInput.value = resolvedAddress;
        }
        
        setTimeout(() => {
           saveLocationBtn.disabled = false;
           saveLocationBtn.textContent = 'Save Location';
           saveLocationBtn.classList.remove('btn-success');
           saveLocationBtn.classList.add('btn-outline-primary');
           syncBtn.click(); // Trigger sync
        }, 1500);
    }

    function fetchWeather() {
        fetch('/api/weather')
            .then(response => response.json())
            .then(data => {
                if (data.isValid) {
                    tempEl.textContent = data.temp.toFixed(1);
                    unitEl.textContent = data.unit;
                    conditionEl.textContent = data.condition;
                    
                    feelsLikeEl.textContent = data.feelsLike.toFixed(1);
                    humidityEl.textContent = data.humidity.toFixed(0);
                    windSpeedEl.textContent = data.windSpeed.toFixed(1);
                    windUnitEl.textContent = data.windUnit;
                    rainChanceEl.textContent = data.rainChance;
                    
                    uvIndexEl.textContent = data.uvIndex.toFixed(1);
                    cloudCoverEl.textContent = data.cloudCover;
                    
                    // Convert visibility meters to miles
                    // 1 meter = 0.000621371 miles
                    const visMiles = data.visibility * 0.000621371;
                    visibilityEl.textContent = visMiles.toFixed(1);
                    
                    pressureEl.textContent = data.pressure.toFixed(0);
                    windDirectionEl.textContent = data.windDirection;
                    windGustsEl.textContent = data.windGusts.toFixed(1);
                    gustUnitEl.textContent = data.windUnit;
                    
                    sunriseEl.textContent = data.sunrise;
                    sunsetEl.textContent = data.sunset;

                    weatherDisplay.classList.remove('d-none');
                    weatherError.classList.add('d-none');
                } else {
                    weatherDisplay.classList.add('d-none');
                    weatherError.classList.remove('d-none');
                }
            })
            .catch(err => {
                console.error(err);
                weatherDisplay.classList.add('d-none');
                weatherError.classList.remove('d-none');
            });
    }

    syncBtn.addEventListener('click', () => {
        syncBtn.disabled = true;
        syncBtn.innerHTML = '<span class="spinner-border spinner-border-sm me-2"></span>Syncing...';
        
        fetch('/api/weather/sync', { method: 'POST' })
            .then(response => {
                if (response.ok) {
                    // Wait a bit for the sync to likely happen, then refresh
                    setTimeout(() => {
                        fetchWeather();
                        syncBtn.disabled = false;
                        syncBtn.innerHTML = '<i class="bi bi-cloud-arrow-down-fill me-2"></i>Sync Now';
                    }, 2000);
                } else {
                    alert('Sync failed');
                    syncBtn.disabled = false;
                    syncBtn.innerHTML = '<i class="bi bi-cloud-arrow-down-fill me-2"></i>Sync Now';
                }
            })
            .catch(e => {
                alert('Error: ' + e);
                syncBtn.disabled = false;
                syncBtn.innerHTML = '<i class="bi bi-cloud-arrow-down-fill me-2"></i>Sync Now';
            });
    });

    // Initial fetch
    fetchWeather();
    
    // Refresh periodically
    setInterval(fetchWeather, 10000);
  </script>
  <script src="https://cdn.jsdelivr.net/npm/bootstrap@5.3.3/dist/js/bootstrap.bundle.min.js"></script>
</body>
</html>
)rawliteral";

const char SERIAL_LOG_TAB_PANE_HTML[] PROGMEM = R"rawliteral(
<div class="tab-pane fade" id="serial-log" role="tabpanel" aria-labelledby="serial-log-tab">
  <div class="card mb-3">
    <div class="card-body">
      <h5 class="card-title d-flex align-items-center"><i class="bi bi-file-text me-2"></i>System Log File</h5>
      <p class="card-text text-muted small">Manage the persistent system log file stored on the device.</p>
      <div class="d-grid gap-2">
        <a href="/api/log/download" id="download-system-log-btn" class="btn btn-secondary" target="_blank">Download System Log</a>
        <button id="rollover-btn" class="btn btn-outline-danger" title="Rollover the log file manually.">Rollover Log</button>
      </div>
    </div>
  </div>
  <div class="card mb-3">
    <div class="card-body">
      <h5 class="card-title d-flex align-items-center text-warning"><i class="bi bi-exclamation-triangle-fill me-2"></i>Diagnostic Crash Log</h5>
      <p class="card-text text-muted small">Manage the dedicated diagnostic crash log file stored on the device.</p>
      <div class="d-grid gap-2">
        <a href="/api/crash/download" id="download-crash-log-btn" class="btn btn-warning" target="_blank">Download Crash Log</a>
        <button id="clear-crash-btn" class="btn btn-outline-danger" title="Clear the crash log file manually.">Clear Crash Log</button>
      </div>
    </div>
  </div>
  <div class="card mb-3">
    <div class="card-body">
      <h5 class="card-title d-flex align-items-center text-danger"><i class="bi bi-cpu-fill me-2"></i>Hardware Core Dump</h5>
      <p class="card-text text-muted small">Manage the hardware partition core dump file stored in flash chip.</p>
      <div class="d-grid gap-2">
        <a href="/api/crash/coredump" id="download-coredump-btn" class="btn btn-danger" target="_blank">Download Core Dump (ELF)</a>
        <button id="clear-coredump-btn" class="btn btn-outline-danger" title="Clear the hardware core dump partition.">Clear Core Dump</button>
      </div>
    </div>
  </div>
  <div class="log-container">
    <div class="log-header">
      <h5>Live Log</h5>
      <button id="download-btn" class="btn btn-sm btn-outline-secondary" title="Download the current log as a text file.">Download Live Log</button>
    </div>
    <div id="log">Waiting for logs...</div>
  </div>
</div>
)rawliteral";

const char SERIAL_LOG_SCRIPT_JS[] PROGMEM = R"rawliteral(
<script>
  const logDiv = document.getElementById('log');
  const downloadBtn = document.getElementById('download-btn');
  const serialLogTab = document.getElementById('serial-log-tab');
  let socket;

  function connect() {
    if (socket && (socket.readyState === WebSocket.OPEN || socket.readyState === WebSocket.CONNECTING)) {
      return;
    }
    socket = new WebSocket(`ws://${window.location.host}/ws/log`);
    socket.onopen = () => {
        logDiv.innerHTML = '<span class="log-connect">[SYSTEM] WebSocket connection established. Listening...</span><br>';
    };
    socket.onmessage = (event) => {
        const shouldScroll = logDiv.scrollTop + logDiv.clientHeight >= logDiv.scrollHeight - 10;
        const textNode = document.createTextNode(event.data);
        logDiv.appendChild(textNode);
        if (shouldScroll) {
          logDiv.scrollTop = logDiv.scrollHeight;
        }
    };
    socket.onclose = (event) => {
        logDiv.innerHTML += `<span class="log-disconnect">[SYSTEM] WebSocket connection closed (Code: ${event.code}). Reconnecting...</span><br>`;
        setTimeout(connect, 3000);
    };
    socket.onerror = (error) => {
         logDiv.innerHTML += '<span class="log-error">[SYSTEM] WebSocket error occurred.</span><br>';
    }
  }

  function disconnect() {
    if (socket && socket.readyState === WebSocket.OPEN) {
      socket.close();
    }
  }

  if (serialLogTab) {
    serialLogTab.addEventListener('shown.bs.tab', function () {
      connect();
    });
    serialLogTab.addEventListener('hidden.bs.tab', function () {
      disconnect();
    });
  }
  
  if (downloadBtn) {
    downloadBtn.addEventListener('click', () => {
        const logText = logDiv.textContent;
        const blob = new Blob([logText], { type: 'text/plain;charset=utf-8;' });
        const link = document.createElement("a");
        link.href = URL.createObjectURL(blob);
        link.download = "esp32clocklog.txt";
        document.body.appendChild(link);
        link.click();
        document.body.removeChild(link);
    });
  }

</script>
)rawliteral";

/**
 * @brief The main index page (Control Panel).
 * Provides navigation to the other configuration pages.
 */
const char INDEX_HTML[] PROGMEM = R"rawliteral(
<!DOCTYPE html>
<html data-bs-theme="dark">
<head>
  <title>ESP32 Clock Control</title>
  %HEAD%
</head>
<body>
  <div class="container my-5">
    <div class="card shadow-sm">
      <div class="card-body text-center">
        <h1 class="card-title mb-4">Control Panel</h1>
        <div class="d-grid gap-3">
          <a href="/wifi" class="btn btn-primary btn-lg d-flex align-items-center justify-content-center" title="Configure WiFi network settings."><i class="bi bi-wifi me-2"></i>Configure WiFi</a>
          <a href="/alarms" class="btn btn-warning btn-lg d-flex align-items-center justify-content-center" title="Set and manage alarms."><i class="bi bi-alarm-fill me-2"></i>Alarms</a>
          <a href="/weather" class="btn btn-success btn-lg d-flex align-items-center justify-content-center" title="View weather and manual sync."><i class="bi bi-cloud-sun-fill me-2"></i>Weather</a>
          <a href="/settings" class="btn btn-info btn-lg d-flex align-items-center justify-content-center" title="Adjust clock and display settings."><i class="bi bi-gear-fill me-2"></i>Settings</a>
          <a href="/system" class="btn btn-secondary btn-lg d-flex align-items-center justify-content-center" title="Update firmware and view logs."><i class="bi bi-hdd-fill me-2"></i>System</a>
        </div>
        <div class="mt-4 text-center text-muted">
          <small>Firmware Version: %FIRMWARE_VERSION%</small>
        </div>
      </div>
    </div>
    <div class="card mt-4">
      <div class="card-body">
        <h5 class="card-title text-center mb-3">Sensor Data</h5>
        <div id="sensor-data-container" class="row text-center">
          <div class="col" id="bme-temp-col" style="display: none;">
            <h6><i class="bi bi-thermometer-sun me-1"></i> Temp</h6>
            <p class="fs-4 mb-0" id="bme-temp"></p>
          </div>
          <div class="col" id="bme-humidity-col" style="display: none;">
            <h6><i class="bi bi-droplet-half me-1"></i> Humidity</h6>
            <p class="fs-4 mb-0" id="bme-humidity"></p>
          </div>
          <div class="col">
            <h6><i class="bi bi-thermometer-half me-1"></i> RTC Temp</h6>
            <p class="fs-4 mb-0" id="rtc-temp"></p>
          </div>
        </div>
      </div>
      <div class="card-footer text-center text-muted small">
        IP: %IP_ADDRESS% &bull; Hostname: %HOSTNAME%.local
      </div>
    </div>
  </div>
  <script>
    document.addEventListener('DOMContentLoaded', function() {
      const bmeTempCol = document.getElementById('bme-temp-col');
      const bmeHumidityCol = document.getElementById('bme-humidity-col');
      const bmeTempEl = document.getElementById('bme-temp');
      const bmeHumidityEl = document.getElementById('bme-humidity');
      const rtcTempEl = document.getElementById('rtc-temp');

      function updateSensorReadings() {
        fetch('/api/sensors')
          .then(response => response.json())
          .then(data => {
            if (data.bmeFound) {
              bmeTempEl.textContent = `${data.bmeTemp}°${data.unit}`;
              bmeHumidityEl.textContent = `${data.bmeHumidity}%`;
              bmeTempCol.style.display = 'block';
              bmeHumidityCol.style.display = 'block';
            } else {
              bmeTempCol.style.display = 'none';
              bmeHumidityCol.style.display = 'none';
            }
            
            if (data.rtcTemp) {
              rtcTempEl.textContent = `${data.rtcTemp}°${data.unit}`;
            } else {
              rtcTempEl.textContent = 'N/A';
            }
          })
          .catch(error => console.error('Error fetching sensor data:', error));
      }

      // Initial update
      updateSensorReadings();
      // Update sensors every 3 seconds
      setInterval(updateSensorReadings, 3000);
    });
  </script>
</body>
</html>
)rawliteral";

/**
 * @brief A simple WiFi setup page for the initial configuration.
 * This page is served in AP mode and has no external dependencies.
 */
const char SIMPLE_WIFI_SETUP_HTML[] PROGMEM = R"rawliteral(
<!DOCTYPE html>
<html lang="en">
<head>
    <meta charset="UTF-8">
    <meta name="viewport" content="width=device-width, initial-scale=1.0">
    <title>WiFi Setup</title>
    <style>
        body { font-family: -apple-system, BlinkMacSystemFont, "Segoe UI", Roboto, "Helvetica Neue", Arial, sans-serif; background-color: #222; color: #fff; display: flex; justify-content: center; align-items: center; height: 100vh; margin: 0; }
        .container { background-color: #333; padding: 2rem; border-radius: 8px; box-shadow: 0 4px 8px rgba(0,0,0,0.3); width: 90%; max-width: 400px; }
        h1 { text-align: center; margin-bottom: 1.5rem; }
        form div { margin-bottom: 1rem; }
        label { display: block; margin-bottom: 0.5rem; }
        input[type="text"], input[type="password"] { font-size: 1rem; width: 100%; padding: 0.75rem; border: 1px solid #555; background-color: #444; color: #fff; border-radius: 4px; box-sizing: border-box; }
        button { padding: 0.75rem; border: none; color: white; border-radius: 4px; cursor: pointer; font-size: 1rem; flex-grow: 1; }
        .button-group { display: flex; gap: 0.5rem; }
        #test-button { background-color: #6c757d; }
        #test-button:hover { background-color: #5a6268; }
        #save-button { background-color: #007bff; }
        #save-button:hover { background-color: #0056b3; }
        hr { border: 1px solid #444; margin: 1.5rem 0; }
        #networks-list { list-style: none; padding: 0; max-height: 150px; overflow-y: auto; border: 1px solid #555; border-radius: 4px; }
        #networks-list li { padding: 0.75rem; cursor: pointer; border-bottom: 1px solid #555; }
        #networks-list li:last-child { border-bottom: none; }
        #networks-list li:hover { background-color: #444; }
        #scan-status { text-align: center; margin-top: 1rem; color: #aaa; }
    </style>
</head>
<body>
    <div class="container">
        <h1>WiFi Setup</h1>
        <form action="/wifi/save" method="POST">
            <div>
                <label for="ssid">WiFi Name (SSID)</label>
                <input type="text" id="ssid" name="ssid" required>
            </div>
            <div>
                <label for="password">Password</label>
                <input type="password" id="password" name="password">
            </div>
            <div class="button-group">
                <button type="button" id="test-button" title="Test the WiFi connection without saving.">Test Connection</button>
                <button type="submit" id="save-button" title="Save the WiFi credentials and connect.">Save & Connect</button>
            </div>
        </form>
        <hr>
        <h2>Select a Network</h2>
        <ul id="networks-list"></ul>
        <div id="scan-status">Scanning for networks...</div>
    </div>
    <script>
        const form = document.querySelector('form');
        const networksList = document.getElementById('networks-list');
        const scanStatus = document.getElementById('scan-status');
        const ssidInput = document.getElementById('ssid');
        const saveButton = document.getElementById('save-button');
        const testButton = document.getElementById('test-button');
        let scanInterval;

        function selectNetwork(ssid) { ssidInput.value = ssid; }
        
        async function fetchAndRenderNetworks() {
            try {
                const response = await fetch('/api/wifi/scan');
                const data = await response.json();
                if (Array.isArray(data)) {
                    clearInterval(scanInterval);
                    renderNetworks(data);
                } else if (data.status === 'scanning') {
                    // Continue polling
                }
            } catch (error) {
                clearInterval(scanInterval);
                scanStatus.textContent = 'Error scanning networks.';
            }
        }

        function renderNetworks(networks) {
            networksList.innerHTML = '';
            if (networks.length === 0) {
                scanStatus.textContent = 'No networks found.';
                scanStatus.style.display = 'block';
                return;
            }
            scanStatus.style.display = 'none';
            const uniqueNetworks = Object.values(networks.reduce((acc, net) => {
                if (!acc[net.ssid] || acc[net.ssid].rssi < net.rssi) { acc[net.ssid] = net; }
                return acc;
            }, {}));
            uniqueNetworks.sort((a, b) => b.rssi - a.rssi);
            uniqueNetworks.forEach(net => {
                const listItem = document.createElement('li');
                listItem.textContent = net.ssid;
                listItem.onclick = () => selectNetwork(net.ssid);
                networksList.appendChild(listItem);
            });
        }

        function startNetworkFetch() {
            if (scanInterval) clearInterval(scanInterval);
            fetchAndRenderNetworks(); // Initial fetch
            scanInterval = setInterval(fetchAndRenderNetworks, 3000); // Poll for results
        }
        
        document.addEventListener('DOMContentLoaded', startNetworkFetch);

        let pollingInterval = null;

        async function pollStatus(isSave) {
            try {
                const response = await fetch('/wifi/status');
                const status = await response.text();

                if (status === 'success') {
                    clearInterval(pollingInterval);
                    alert(isSave ? 'Success! Credentials saved. The device will now reboot.' : 'Connection successful!');
                    if (isSave) {
                        saveButton.textContent = 'Rebooting...';
                    } else {
                        saveButton.disabled = false;
                        testButton.disabled = false;
                        testButton.textContent = 'Test Connection';
                    }
                } else if (status === 'failed') {
                    clearInterval(pollingInterval);
                    alert('Connection failed. Please check your password and try again.');
                    saveButton.disabled = false;
                    testButton.disabled = false;
                    saveButton.textContent = 'Save & Connect';
                    testButton.textContent = 'Test Connection';
                }
            } catch (error) {
                clearInterval(pollingInterval);
                alert('Error checking status. Please try again.');
                saveButton.disabled = false;
                testButton.disabled = false;
                saveButton.textContent = 'Save & Connect';
                testButton.textContent = 'Test Connection';
            }
        }

        async function startTest(endpoint, button, isSave) {
            if (ssidInput.value.trim() === '') {
                alert('WiFi Name (SSID) cannot be empty.');
                return;
            }

            button.textContent = 'Testing...';
            saveButton.disabled = true;
            testButton.disabled = true;

            try {
                const formData = new FormData(form);
                const response = await fetch(endpoint, {
                    method: 'POST',
                    body: formData
                });

                if (response.ok) {
                    pollingInterval = setInterval(() => pollStatus(isSave), 2000);
                } else {
                    const errorText = await response.text();
                    alert(`Error: ${errorText}`);
                    saveButton.disabled = false;
                    testButton.disabled = false;
                    button.textContent = isSave ? 'Save & Connect' : 'Test Connection';
                }
            } catch (error) {
                alert('An unexpected error occurred. Please try again.');
                saveButton.disabled = false;
                testButton.disabled = false;
                button.textContent = isSave ? 'Save & Connect' : 'Test Connection';
            }
        }
        
        saveButton.addEventListener('click', (e) => {
            e.preventDefault();
            startTest('/wifi/save', saveButton, true);
        });

        testButton.addEventListener('click', (e) => {
            e.preventDefault();
            startTest('/wifi/test', testButton, false);
        });
    </script>
</body>
</html>
)rawliteral";

/**
 * @brief The WiFi Configuration page.
 * Displays available networks and provides a form to enter credentials.
 */
const char WIFI_CONFIG_HTML[] PROGMEM = R"rawliteral(
<!DOCTYPE html>
<html data-bs-theme="dark">
<head>
  <title>%WIFI_PAGE_TITLE%</title>
  %HEAD%
  <style>
    .network-item {
      cursor: pointer;
    }
    .network-item:hover {
      background-color: #e9ecef;
      color: #212529;
    }
    #networks-list {
      max-height: 200px;
      overflow-y: auto;
    }
  </style>
</head>
<body>
  <div class="container my-5">
    <div class="card shadow-sm">
      <div class="card-body">
        <h1 class="card-title text-center mb-4">%WIFI_PAGE_TITLE%</h1>
        <form id="wifi-form" action="/wifi/save" method="POST">
          <div class="mb-3">
            <input type="text" class="form-control" id="ssid" name="ssid" placeholder="SSID" required>
          </div>
          <div class="mb-3">
            <input type="password" class="form-control" name="password" placeholder="Password">
          </div>
          <div class="d-grid">
            <button type="submit" id="save-button" class="btn btn-success btn-lg" title="Save the selected WiFi network credentials and connect.">Save & Connect</button>
          </div>
        </form>
        <div id="form-status" class="mt-3"></div>
        <hr class="my-4">
        <div class="text-center mb-3">
          <button id="scan-button" class="btn btn-primary" title="Scan for available WiFi networks.">
            <i class="bi bi-wifi"></i> Scan for Networks
          </button>
        </div>
        <div id="networks-status" class="text-center text-muted mb-2 d-none"></div>
        <div id="networks-list" class="list-group"></div>
        <div class="d-grid mt-4 %BACK_BUTTON_CLASS%">
          <a href="/" class="btn btn-secondary" title="Return to the main menu.">Back to Menu</a>
        </div>
      </div>
    </div>
    <form id="hostname-form" class="mt-4">
      <div class="mb-3 p-3 border rounded">
        <label for="hostname" class="form-label" title="Set the network hostname for the device.">Hostname</label>
        <div class="input-group">
          <input
            type="text"
            class="form-control"
            id="hostname"
            name="hostname"
            value="%HOSTNAME%"
            title="Enter the desired hostname." />
          <button class="btn btn-warning" type="submit" title="Save the new hostname and reboot the device.">
            Save & Reboot
          </button>
        </div>
      </div>
    </form>
  </div>
  <script>
    const scanButton = document.getElementById('scan-button');
    const networksStatus = document.getElementById('networks-status');
    const networksList = document.getElementById('networks-list');
    const wifiForm = document.getElementById('wifi-form');
    const saveButton = document.getElementById('save-button');
    const formStatus = document.getElementById('form-status');
    let scanInterval;

    function selectNetwork(ssid) {
      document.getElementById('ssid').value = ssid;
    }

    function getSignalIcon(rssi) {
        if (rssi >= -67) return '<i class="bi bi-reception-4 text-success"></i>';
        if (rssi >= -70) return '<i class="bi bi-reception-3 text-success"></i>';
        if (rssi >= -80) return '<i class="bi bi-reception-2 text-warning"></i>';
        if (rssi >= -90) return '<i class="bi bi-reception-1 text-danger"></i>';
        return '<i class="bi bi-reception-0 text-danger"></i>';
    }
    
    function getEncryptionIcon(encryption) {
        return encryption !== 'OPEN' ? '<i class="bi bi-lock-fill"></i>' : '<i class="bi bi-unlock-fill"></i>';
    }


    async function startScan() {
      scanButton.disabled = true;
      networksStatus.classList.remove('d-none');
      networksStatus.innerHTML = `
        <div class="spinner-border spinner-border-sm" role="status">
          <span class="visually-hidden">Loading...</span>
        </div>
        <span class="ms-2">Scanning for networks...</span>`;
      networksList.innerHTML = '';

      // Start the scan on the backend
      try {
        await fetch('/api/wifi/scan?start=true');
      } catch (error) {
        networksStatus.innerHTML = 'Error starting scan.';
        scanButton.disabled = false;
        return;
      }

      // Start polling for results
      scanInterval = setInterval(fetchAndRenderNetworks, 2000);
    }

    async function fetchAndRenderNetworks() {
      try {
        const response = await fetch('/api/wifi/scan');
        const data = await response.json();

        if (Array.isArray(data)) {
          // Scan is complete and we have data
          clearInterval(scanInterval);
          renderNetworks(data);
        } else if (data.status === 'scanning') {
          // Scan is still in progress, the UI already shows "Scanning..."
        }
      } catch (error) {
        clearInterval(scanInterval);
        networksStatus.innerHTML = 'Error scanning for networks.';
        scanButton.disabled = false;
      }
    }

    function renderNetworks(networks) {
      scanButton.disabled = false;
      networksList.innerHTML = ''; // Clear previous results
      
      if (networks.length === 0) {
        networksStatus.innerHTML = 'No networks found.';
        return;
      }

      networksStatus.classList.add('d-none');
      
      // Filter out duplicate SSIDs, keeping the one with the strongest signal
      const uniqueNetworks = Object.values(networks.reduce((acc, net) => {
        if (!acc[net.ssid] || acc[net.ssid].rssi < net.rssi) {
          acc[net.ssid] = net;
        }
        return acc;
      }, {}));

      uniqueNetworks.sort((a, b) => b.rssi - a.rssi); // Sort by signal strength

      uniqueNetworks.forEach(net => {
        const listItem = document.createElement('a');
        listItem.href = '#';
        listItem.className = 'list-group-item list-group-item-action d-flex justify-content-between align-items-center network-item';
        listItem.onclick = (e) => {
            e.preventDefault();
            selectNetwork(net.ssid);
        };
        
        listItem.innerHTML = `
          <span>
            ${getEncryptionIcon(net.encryption)}
            <strong class="ms-2">${net.ssid}</strong>
          </span>
          <span class="badge bg-light text-dark rounded-pill">
             ${getSignalIcon(net.rssi)}
             <span class="ms-1">${net.rssi} dBm</span>
          </span>
        `;
        networksList.appendChild(listItem);
      });
    }

    function showStatus(message, type = 'info') {
      formStatus.innerHTML = `<div class="alert alert-${type}">${message}</div>`;
    }

    wifiForm.addEventListener('submit', async (e) => {
      e.preventDefault();
      saveButton.disabled = true;
      showStatus('Saving credentials...', 'info');

      try {
        const formData = new FormData(wifiForm);
        const response = await fetch('/wifi/save', {
          method: 'POST',
          body: formData
        });

        const responseText = await response.text();
        if (response.ok) {
          showStatus(responseText, 'success');
        } else {
          showStatus(`Error: ${responseText}`, 'danger');
          saveButton.disabled = false;
        }
      } catch (error) {
        showStatus('An unexpected error occurred.', 'danger');
        saveButton.disabled = false;
      }
    });

    scanButton.addEventListener('click', startScan);

    document.getElementById('hostname-form').addEventListener('submit', function(e) {
      e.preventDefault();
      const hostname = document.getElementById('hostname').value;
      const formData = new FormData();
      formData.append('hostname', hostname);
      fetch('/api/wifi/hostname', {
        method: 'POST',
        body: formData
      })
      .then(async response => {
        if (response.ok) {
          alert('Hostname saved. The device will now reboot.');
          setTimeout(() => {
            window.location.href = '/';
          }, 1000);
        } else {
          const text = await response.text();
          alert('Error: ' + text);
        }
      })
      .catch(e => {
        alert('Network error: ' + e);
      });
    });
  </script>
</body>
</html>
)rawliteral";

/**
 * @brief The Settings page.
 * Contains forms to adjust clock settings and display colors.
 */
const char SETTINGS_PAGE_HTML[] PROGMEM = R"rawliteral(
<!DOCTYPE html>
<html data-bs-theme="dark">
<head>
  <title>Settings</title>
  %HEAD%
  <style>
      .status-indicator {
        font-size: 0.9rem;
        font-weight: bold;
        display: flex;
        align-items: center;
        gap: 0.4rem;
        min-width: 95px;
      }
      .color-picker-wrapper {
        margin-bottom: 1rem;
        padding: 0.75rem;
        border: 1px solid #444;
        border-radius: 0.375rem;
        text-align: center;
      }
      .color-picker-wrapper label {
        margin-bottom: 0.5rem;
        display: block;
      }
      input[type="color"] {
        min-width: 100px;
        height: 40px;
        padding: 0.2rem;
        border-radius: 0.375rem;
        border: none;
        cursor: pointer;
      }
      /* Make range inputs easier to use on touch devices */
      .form-range {
        padding: 0;
      }
      .form-range::-webkit-slider-thumb {
        width: 2rem;
        height: 2rem;
        margin-top: -0.75rem; /* Vertically center thumb on track */
      }
      .form-range::-moz-range-thumb {
        width: 2rem;
        height: 2rem;
      }
      .form-range::-webkit-slider-runnable-track {
        height: 0.5rem;
      }
      .form-range::-moz-range-track {
        height: 0.5rem;
      }
      .form-range::-ms-track {
        height: 0.5rem;
      }
  </style>
</head>
  <body>
    <div class="container my-5">
      <div class="card shadow-sm">
        <div class="card-body">
          <div class="d-flex justify-content-between align-items-center mb-4">
            <h1 class="card-title m-0">Settings</h1>
            <div class="status-indicator"></div>
          </div>
          
          <div class="alert alert-info d-flex align-items-center" role="alert">
            <i class="bi bi-info-circle-fill me-2"></i>
            <div>Heads up! All your changes are saved automatically.</div>
          </div>

          <ul class="nav nav-tabs nav-fill" id="settingsTabs" role="tablist">
            <li class="nav-item" role="presentation">
              <button class="nav-link active" id="general-tab" data-bs-toggle="tab" data-bs-target="#general" type="button" role="tab" aria-controls="general" aria-selected="true">General</button>
            </li>
            <li class="nav-item" role="presentation">
              <button class="nav-link" id="display-tab" data-bs-toggle="tab" data-bs-target="#display" type="button" role="tab" aria-controls="display" aria-selected="false">Display</button>
            </li>
          </ul>

          <div class="tab-content" id="settingsTabsContent">
            <div class="tab-pane fade show active" id="general" role="tabpanel" aria-labelledby="general-tab">
              <form id="settings-form" class="p-3">
                <div id="auto-brightness-section" class="mb-3 p-3 border rounded">
                  <div class="form-check form-switch ps-0 d-flex justify-content-between align-items-center">
                    <label class="form-check-label" for="auto-brightness" title="Enable or disable automatic brightness adjustment.">Auto Brightness</label>
                    <input class="form-check-input" type="checkbox" role="switch" id="auto-brightness" name="autoBrightness" %AUTO_BRIGHTNESS_CHECKED% />
                  </div>
                  <div id="auto-brightness-controls" class="mt-3 %AUTO_BRIGHTNESS_CONTROLS_CLASS%">
                    <hr>
                    <label for="auto-brightness-start-hour" class="form-label d-flex justify-content-between">
                      <span>Start Hour</span>
                      <span id="auto-brightness-start-hour-value">%AUTO_BRIGHTNESS_START_HOUR_VALUE%</span>
                    </label>
                    <input type="range" class="form-range" id="auto-brightness-start-hour" name="autoBrightnessStartHour" min="0" max="23" value="%AUTO_BRIGHTNESS_START_HOUR%" />
                    <label for="auto-brightness-end-hour" class="form-label d-flex justify-content-between mt-2">
                      <span>End Hour</span>
                      <span id="auto-brightness-end-hour-value">%AUTO_BRIGHTNESS_END_HOUR_VALUE%</span>
                    </label>
                    <input type="range" class="form-range" id="auto-brightness-end-hour" name="autoBrightnessEndHour" min="0" max="23" value="%AUTO_BRIGHTNESS_END_HOUR%" />
                    <label for="day-brightness" class="form-label d-flex justify-content-between mt-2">
                      <span>Day Brightness</span>
                      <span id="day-brightness-value">%DAY_BRIGHTNESS_VALUE%</span>
                    </label>
                    <input type="range" class="form-range" id="day-brightness" name="dayBrightness" min="%BRIGHTNESS_MIN%" max="%BRIGHTNESS_MAX%" value="%DAY_BRIGHTNESS%" />
                    <label for="night-brightness" class="form-label d-flex justify-content-between mt-2">
                      <span>Night Brightness</span>
                      <span id="night-brightness-value">%NIGHT_BRIGHTNESS_VALUE%</span>
                    </label>
                    <input type="range" class="form-range" id="night-brightness" name="nightBrightness" min="%BRIGHTNESS_MIN%" max="%BRIGHTNESS_MAX%" value="%NIGHT_BRIGHTNESS%" />
                  </div>
                </div>
                <div id="manual-brightness-section" class="mb-3 p-3 border rounded %MANUAL_BRIGHTNESS_CLASS%">
                  <label for="brightness" class="form-label d-flex justify-content-between">
                    <span title="Set the display brightness manually.">Manual Brightness</span>
                    <span id="brightness-value">%BRIGHTNESS_VALUE%</span>
                  </label>
                  <input type="range" class="form-range" id="brightness" name="brightness" min="%BRIGHTNESS_MIN%" max="%BRIGHTNESS_MAX%" title="Adjust the manual brightness level." value="%BRIGHTNESS%" />
                </div>
                <div class="mb-3 p-3 border rounded border-danger">
                  <div class="form-check form-switch ps-0 d-flex justify-content-between align-items-center">
                    <label class="form-check-label text-danger" for="offline-mode" title="Enable offline mode. This disables WiFi permanently until a factory reset.">Offline Mode</label>
                    <input class="form-check-input bg-danger border-danger" type="checkbox" role="switch" id="offline-mode" name="offlineMode" %OFFLINE_MODE_CHECKED% />
                  </div>
                  <div class="mt-2 small text-danger">
                    Warning: Enabling offline mode will permanently disable WiFi on the next boot. A factory reset (holding snooze button during boot) is required to re-enable WiFi.
                  </div>
                </div>
                <div class="mb-3 p-3 border rounded">
                  <div class="form-check form-switch ps-0 d-flex justify-content-between align-items-center">
                    <label class="form-check-label" for="24hour" title="Switch between 12-hour and 24-hour time formats.">24-Hour Format</label>
                    <input class="form-check-input" type="checkbox" role="switch" id="24hour" name="use24HourFormat" %USE_24_HOUR_FORMAT_CHECKED% />
                  </div>
                  <hr class="my-2">
                  <div class="form-check form-switch ps-0 d-flex justify-content-between align-items-center">
                    <label class="form-check-label" for="celsius" title="Switch between Celsius and Fahrenheit temperature units.">Use Celsius (&deg;C)</label>
                    <input class="form-check-input" type="checkbox" role="switch" id="celsius" name="useCelsius" %USE_CELSIUS_CHECKED% />
                  </div>
                  <hr class="my-2">
                  <div class="form-check form-switch ps-0 d-flex justify-content-between align-items-center">
                    <label class="form-check-label" for="screen-flipped" title="Flip the screen orientation 180 degrees.">Flip Screen</label>
                    <input class="form-check-input" type="checkbox" role="switch" id="screen-flipped" name="screenFlipped" %SCREEN_FLIPPED_CHECKED% />
                  </div>
                  <hr class="my-2">
                  <div class="form-check form-switch ps-0 d-flex justify-content-between align-items-center">
                    <div>
                      <label class="form-check-label" for="invert-colors" title="Invert the display colors.">Invert Colors</label>
                      <small class="form-text text-muted d-block">Needed for some IPS displays</small>
                    </div>
                    <input class="form-check-input" type="checkbox" role="switch" id="invert-colors" name="invertColors" %INVERT_COLORS_CHECKED% />
                  </div>
                </div>
                <div class="mb-3 p-3 border rounded">
                  <div class="form-check form-switch mb-3">
                    <input class="form-check-input" type="checkbox" role="switch" id="temp-correction-enabled" name="tempCorrectionEnabled" %TEMP_CORRECTION_ENABLED_CHECKED%>
                    <label class="form-check-label" for="temp-correction-enabled">Enable Thermal Compensation</label>
                  </div>
                  
                  <div class="form-check form-switch mb-3">
                    <input class="form-check-input" type="checkbox" role="switch" id="auto-temp-calibration" name="autoTempCalibration" %AUTO_TEMP_CALIBRATION_CHECKED%>
                    <label class="form-check-label" for="auto-temp-calibration">Enable Auto Cold-Boot Calibration</label>
                    <span id="auto-cal-status" class="badge bg-secondary ms-2">Idle</span>
                    <div class="small text-muted mt-1">Last Status: <span id="last-auto-cal-status">%LAST_AUTO_CAL_STATUS%</span></div>
                  </div>
                  <div id="temp-correction-controls" class="%TEMP_CORRECTION_CONTROLS_CLASS%">
                    <hr>
                    <label for="temp-compensation-factor" class="form-label">Compensation Factor: <span id="temp-compensation-factor-value">%TEMP_COMPENSATION_FACTOR%</span></label>
                    <input type="range" class="form-range" id="temp-compensation-factor" name="tempCompensationFactor" min="0" max="1" step="0.01" value="%TEMP_COMPENSATION_FACTOR%">
                    <small class="form-text text-muted">Controls how aggressively internal heat is compensated. Higher = more correction. Start at 0.15 and adjust to match a reference thermometer.</small>
                    <hr>
                    <label for="temp-correction" class="form-label">Temperature Correction (&deg;%TEMP_CORRECTION_UNIT%)</label>
                    <input type="number" class="form-control" id="temp-correction" name="tempCorrection" step="0.1" value="%TEMP_CORRECTION_VALUE%">
                    <small class="form-text text-muted">Fine-tune: if the clock is still 2 degrees too high after adjusting the factor, enter -2.0 here.</small>
                  </div>
                </div>
                <div class="mb-3 p-3 border rounded">
                  <label for="timezone-select" class="form-label">Timezone</label>
                  <select class="form-select" id="timezone-select" name="timezone">
                    <option value="EST5EDT,M3.2.0/2:00,M11.1.0/2:00" %TIMEZONE_SELECTED_EST%>Eastern Time</option>
                    <option value="CST6CDT,M3.2.0/2:00,M11.1.0/2:00" %TIMEZONE_SELECTED_CST%>Central Time</option>
                    <option value="MST7MDT,M3.2.0/2:00,M11.1.0/2:00" %TIMEZONE_SELECTED_MST%>Mountain Time</option>
                    <option value="PST8PDT,M3.2.0/2:00,M11.1.0/2:00" %TIMEZONE_SELECTED_PST%>Pacific Time</option>
                    <option value="MST7" %TIMEZONE_SELECTED_AZ%>Arizona</option>
                    <option value="AKST9AKDT,M3.2.0/2:00,M11.1.0/2:00" %TIMEZONE_SELECTED_AK%>Alaska</option>
                    <option value="HST10" %TIMEZONE_SELECTED_HI%>Hawaii</option>
                  </select>
                </div>
                <div class="mb-3 p-3 border rounded">
                  <label class="form-label">Page Cycle Order</label>
                  <div class="text-muted small mb-2">
                    Check to enable. Use arrows to reorder.
                  </div>
                  <div id="page-order-list" class="list-group mb-3">
                    <!-- Items injected by JS -->
                  </div>

                  <label for="default-page" class="form-label">Default Display Page</label>
                  <select class="form-select" id="default-page" name="defaultPage">
                    <option value="0" %DEFAULT_PAGE_SELECTED_0%>Clock</option>
                    <option value="1" %DEFAULT_PAGE_SELECTED_1%>Weather</option>
                    <option value="2">System Info</option>
                    <option value="3" %DEFAULT_PAGE_SELECTED_3%>Clock + Weather</option>
                  </select>
                </div>
                <div class="mb-3 p-3 border rounded">
                  <label for="snooze-duration" class="form-label">Snooze Duration (minutes)</label>
                  <input type="number" class="form-control" id="snooze-duration" name="snoozeDuration" min="1" max="60" value="%SNOOZE_DURATION%">
                </div>
                <div class="mb-3 p-3 border rounded">
                  <label for="dismiss-duration" class="form-label">Hold to Dismiss (seconds)</label>
                  <input type="number" class="form-control" id="dismiss-duration" name="dismissDuration" min="1" max="10" value="%DISMISS_DURATION%">
                </div>
              </form>
              <div class="d-grid gap-2 mt-3">
                <button type="button" id="reset-general-btn" class="btn btn-danger" title="Reset all general settings to their default values.">Reset General Settings</button>
              </div>
            </div>
            <div class="tab-pane fade" id="display" role="tabpanel" aria-labelledby="display-tab">
              <form id="display-settings-form" class="p-3">
                <div class="row">
                  <div class="col-md-6">
                    <div class="color-picker-wrapper">
                      <label for="background-color" title="Set the main background color.">Background Color</label>
                      <input type="color" id="background-color" name="backgroundColor" title="Select a background color." value="%BACKGROUND_COLOR%">
                    </div>
                  </div>
                  <div class="col-md-6">
                    <div class="color-picker-wrapper">
                      <label for="time-color" title="Set the color for the time display.">Time Color</label>
                      <input type="color" id="time-color" name="timeColor" title="Select a color for the time." value="%TIME_COLOR%">
                    </div>
                  </div>
                  <div class="col-md-6">
                    <div class="color-picker-wrapper">
                      <label for="tod-color" title="Set the color for the AM/PM indicator.">TOD Color</label>
                      <input type="color" id="tod-color" name="todColor" title="Select a color for the AM/PM indicator." value="%TOD_COLOR%">
                    </div>
                  </div>
                  <div class="col-md-6">
                    <div class="color-picker-wrapper">
                      <label for="seconds-color" title="Set the color for the seconds display.">Seconds Color</label>
                      <input type="color" id="seconds-color" name="secondsColor" title="Select a color for the seconds." value="%SECONDS_COLOR%">
                    </div>
                  </div>
                  <div class="col-md-6">
                    <div class="color-picker-wrapper">
                      <label for="day-of-week-color" title="Set the color for the day of the week.">Day of Week Color</label>
                      <input type="color" id="day-of-week-color" name="dayOfWeekColor" title="Select a color for the day of the week." value="%DAY_OF_WEEK_COLOR%">
                    </div>
                  </div>
                  <div class="col-md-6">
                    <div class="color-picker-wrapper">
                      <label for="date-color" title="Set the color for the date display.">Date Color</label>
                      <input type="color" id="date-color" name="dateColor" title="Select a color for the date." value="%DATE_COLOR%">
                    </div>
                  </div>
                  <div class="col-md-6">
                    <div class="color-picker-wrapper">
                      <label for="temp-color" title="Set the color for the temperature display.">Temperature Color</label>
                      <input type="color" id="temp-color" name="tempColor" title="Select a color for the temperature." value="%TEMP_COLOR%">
                    </div>
                  </div>
                  <div class="col-md-6">
                    <div class="color-picker-wrapper">
                      <label for="humidity-color" title="Set the color for the humidity display.">Humidity Color</label>
                      <input type="color" id="humidity-color" name="humidityColor" title="Select a color for the humidity." value="%HUMIDITY_COLOR%">
                    </div>
                  </div>
                  <div class="col-md-6">
                    <div class="color-picker-wrapper">
                      <label for="weather-temp-color" title="Set the color for the weather temperature display.">Weather Temp Color</label>
                      <input type="color" id="weather-temp-color" name="weatherTempColor" title="Select a color for the weather temperature." value="%WEATHER_TEMP_COLOR%">
                    </div>
                  </div>
                  <div class="col-md-6">
                    <div class="color-picker-wrapper">
                      <label for="weather-forecast-color" title="Set the color for the weather forecast display.">Weather Forecast Color</label>
                      <input type="color" id="weather-forecast-color" name="weatherForecastColor" title="Select a color for the weather forecast." value="%WEATHER_FORECAST_COLOR%">
                    </div>
                  </div>
                </div>
              </form>
              <div class="d-grid gap-2 mt-4">
                <button type="button" id="reset-colors-btn" class="btn btn-danger" title="Reset all colors to their default values.">Reset Colors</button>
              </div>
            </div>
          </div>

          <div class="d-grid gap-2 mt-4">
            <a href="/" class="btn btn-secondary" title="Return to the main menu.">Back to Menu</a>
          </div>
        </div>
      </div>
    </div>
    <script>
      const ERROR_DISPLAY_MS = 3000;
      let saveGeneralTimeout;
      let saveDisplayTimeout;

      const BRIGHTNESS_MIN = %BRIGHTNESS_MIN%;
      const BRIGHTNESS_MAX = %BRIGHTNESS_MAX%;

      const statusEl = document.querySelector(".status-indicator");
      const settingsForm = document.getElementById("settings-form");
      const displaySettingsForm = document.getElementById("display-settings-form");
      
      const autoBrightnessEl = document.getElementById("auto-brightness");
      const offlineModeEl = document.getElementById("offline-mode");
      const brightnessEl = document.getElementById("brightness");
      const brightnessValueEl = document.getElementById("brightness-value");
      const manualBrightnessSectionEl = document.getElementById("manual-brightness-section");
      const autoBrightnessControlsEl = document.getElementById("auto-brightness-controls");
      const autoBrightnessStartHourEl = document.getElementById("auto-brightness-start-hour");
      const autoBrightnessStartHourValueEl = document.getElementById("auto-brightness-start-hour-value");
      const autoBrightnessEndHourEl = document.getElementById("auto-brightness-end-hour");
      const autoBrightnessEndHourValueEl = document.getElementById("auto-brightness-end-hour-value");
      const dayBrightnessEl = document.getElementById("day-brightness");
      const dayBrightnessValueEl = document.getElementById("day-brightness-value");
      const nightBrightnessEl = document.getElementById("night-brightness");
      const nightBrightnessValueEl = document.getElementById("night-brightness-value");
      const twentyFourHourEl = document.getElementById("24hour");
      const celsiusEl = document.getElementById("celsius");
      const tempCorrectionEnabledEl = document.getElementById("temp-correction-enabled");
      const autoTempCalibrationEl = document.getElementById("auto-temp-calibration");
      const tempCorrectionEl = document.getElementById("temp-correction");
      const tempCorrectionControlsEl = document.getElementById("temp-correction-controls");
      const tempCompensationFactorEl = document.getElementById("temp-compensation-factor");
      const tempCompensationFactorValueEl = document.getElementById("temp-compensation-factor-value");
      const screenFlippedEl = document.getElementById("screen-flipped");
      const invertColorsEl = document.getElementById("invert-colors");
      const timezoneEl = document.getElementById("timezone-select");
      const defaultPageEl = document.getElementById("default-page");
      const pageOrderListEl = document.getElementById("page-order-list");
      const colorPickers = displaySettingsForm.querySelectorAll('input[type="color"]');
      const resetGeneralBtn = document.getElementById('reset-general-btn');
      const resetColorsBtn = document.getElementById('reset-colors-btn');

      // Map of Page IDs to friendly names
      const PAGE_NAMES = {
        0: "Clock",
        1: "Weather",
        2: "System Info",
        3: "Clock + Weather"
      };

      // All available pages in the system (could be dynamic, but hardcoded for now based on main.cpp)
      const ALL_PAGE_IDS = [0, 1, 3, 2]; // Default preferred order

      const STATUS_INDICATORS = {
        SAVED: '<i class="bi bi-check-circle-fill text-success"></i> <span class="text-muted">Saved</span>',
        UNSAVED: '<i class="bi bi-pencil-fill text-warning"></i> <span class="text-warning">Unsaved</span>',
        SAVING: '<div class="spinner-border spinner-border-sm text-primary" role="status"></div> <span class="text-primary">Saving...</span>',
        ERROR: '<i class="bi bi-exclamation-triangle-fill text-danger"></i> <span class="text-danger">Error</span>',
      };

      function setStatus(status) {
        statusEl.innerHTML = status;
      }

      function clamp(v, a, b) {
        return Math.max(a, Math.min(b, v));
      }

      function toPercent(value, min = BRIGHTNESS_MIN, max = BRIGHTNESS_MAX) {
        const num = Number(value);
        const clamped = clamp(num, min, max);
        const pct = Math.round(((clamped - min) / (max - min)) * 100);
        return `${pct}%`;
      }

      function formatHour(hour, is24Hour) {
        if (is24Hour) {
          const h = parseInt(hour);
          return h < 10 ? '0' + h : h;
        }
        const h = parseInt(hour);
        if (h === 0) return '12 AM';
        if (h === 12) return '12 PM';
        if (h < 12) return `${h} AM`;
        return `${h - 12} PM`;
      }

      function handleGeneralInputChange(event) {
        clearTimeout(saveGeneralTimeout);
        setStatus(STATUS_INDICATORS.UNSAVED);
        saveGeneralTimeout = setTimeout(() => saveGeneralSettings(event), 100);
      }

      function handleDisplayInputChange() {
        clearTimeout(saveDisplayTimeout);
        setStatus(STATUS_INDICATORS.UNSAVED);
        saveDisplayTimeout = setTimeout(saveDisplaySettings, 50);
      }

      function toggleBrightnessSlider() {
        const isAuto = autoBrightnessEl.checked;
        if (isAuto) {
          manualBrightnessSectionEl.classList.add('d-none');
          autoBrightnessControlsEl.classList.remove('d-none');
        } else {
          manualBrightnessSectionEl.classList.remove('d-none');
          autoBrightnessControlsEl.classList.add('d-none');
          fetch('/api/settings')
            .then(response => response.json())
            .then(settings => {
              brightnessEl.value = settings.actualBrightness;
              brightnessValueEl.textContent = toPercent(settings.actualBrightness);
            })
            .catch(e => console.error('Failed to sync brightness slider:', e));
        }
      }

      function updateBrightnessUI(settings) {
        brightnessEl.value = settings.actualBrightness ?? 128;
        brightnessValueEl.textContent = toPercent(brightnessEl.value);
        
        dayBrightnessEl.value = settings.dayBrightness ?? 255;
        dayBrightnessValueEl.textContent = toPercent(dayBrightnessEl.value);
        
        nightBrightnessEl.value = settings.nightBrightness ?? 10;
        nightBrightnessValueEl.textContent = toPercent(nightBrightnessEl.value);
      }
      
      function updateHourFormatUI(settings) {
        const is24Hour = settings.use24HourFormat ?? false;
        twentyFourHourEl.checked = is24Hour;
        
        autoBrightnessStartHourEl.value = settings.autoBrightnessStartHour ?? 7;
        autoBrightnessStartHourValueEl.textContent = formatHour(autoBrightnessStartHourEl.value, is24Hour);
        
        autoBrightnessEndHourEl.value = settings.autoBrightnessEndHour ?? 21;
        autoBrightnessEndHourValueEl.textContent = formatHour(autoBrightnessEndHourEl.value, is24Hour);
      }
      
      function renderPageOrderList(enabledPages) {
        pageOrderListEl.innerHTML = '';
        
        // Combine enabled pages with disabled ones (at the end)
        // Make a copy of enabledPages to work with
        let currentOrder = [...(enabledPages || [])];
        
        // Add any missing pages to the end
        ALL_PAGE_IDS.forEach(id => {
          if (!currentOrder.includes(id)) {
            currentOrder.push(id);
          }
        });

        currentOrder.forEach((id, index) => {
           const isEnabled = enabledPages ? enabledPages.includes(id) : ALL_PAGE_IDS.includes(id); // Default to all if null, but usually loaded
           
           const item = document.createElement('div');
           item.className = 'list-group-item d-flex align-items-center justify-content-between p-2';
           item.dataset.id = id;
           
           item.innerHTML = `
             <div class="form-check m-0 d-flex align-items-center gap-2">
               <input class="form-check-input page-enable-check" type="checkbox" ${isEnabled ? 'checked' : ''} id="page-check-${id}">
               <label class="form-check-label user-select-none" for="page-check-${id}">${PAGE_NAMES[id] || 'Unknown Page ' + id}</label>
             </div>
             <div class="btn-group" role="group">
               <button type="button" class="btn btn-sm btn-outline-secondary move-up-btn" title="Move Up"><i class="bi bi-arrow-up"></i></button>
               <button type="button" class="btn btn-sm btn-outline-secondary move-down-btn" title="Move Down"><i class="bi bi-arrow-down"></i></button>
             </div>
           `;
           
           // Event listeners
           item.querySelector('.page-enable-check').addEventListener('change', () => handleGeneralInputChange());
           item.querySelector('.move-up-btn').addEventListener('click', (e) => {
               e.preventDefault();
               moveItem(item, -1);
           });
           item.querySelector('.move-down-btn').addEventListener('click', (e) => {
               e.preventDefault();
               moveItem(item, 1);
           });

           pageOrderListEl.appendChild(item);
        });
        
        updateMoveButtons();
      }

      function moveItem(item, direction) {
          if (direction === -1 && item.previousElementSibling) {
              item.parentNode.insertBefore(item, item.previousElementSibling);
          } else if (direction === 1 && item.nextElementSibling) {
              item.parentNode.insertBefore(item.nextElementSibling, item);
          }
          updateMoveButtons();
          handleGeneralInputChange();
      }

      function updateMoveButtons() {
          const items = pageOrderListEl.querySelectorAll('.list-group-item');
          items.forEach((item, index) => {
              const upBtn = item.querySelector('.move-up-btn');
              const downBtn = item.querySelector('.move-down-btn');
              upBtn.disabled = index === 0;
              downBtn.disabled = index === items.length - 1;
          });
      }

      function getEnabledPagesFromUI() {
          const enabled = [];
          pageOrderListEl.querySelectorAll('.list-group-item').forEach(item => {
              const checkbox = item.querySelector('.page-enable-check');
              if (checkbox.checked) {
                  enabled.push(parseInt(item.dataset.id));
              }
          });
          return enabled;
      }

      function updateGeneralSettingsUI(settings) {
        autoBrightnessEl.checked = settings.autoBrightness || false;
        offlineModeEl.checked = settings.offlineMode || false;
        celsiusEl.checked = settings.useCelsius || false;
        screenFlippedEl.checked = settings.screenFlipped || false;
        invertColorsEl.checked = settings.invertColors || false;
        timezoneEl.value = settings.timezone || "EST5EDT,M3.2.0/2:00,M11.1.0/2:00";
        defaultPageEl.value = settings.defaultPage || 0;
        document.getElementById('snooze-duration').value = settings.snoozeDuration || 9;
        document.getElementById('dismiss-duration').value = settings.dismissDuration || 3;
        
        let tempCorrection = settings.tempCorrection || 0.0;
        if (!settings.useCelsius) {
          tempCorrection = tempCorrection * 9.0 / 5.0;
        }
        tempCorrectionEl.value = tempCorrection.toFixed(1);
        tempCorrectionEnabledEl.checked = settings.tempCorrectionEnabled || false;
        autoTempCalibrationEl.checked = settings.autoTempCalibration !== undefined ? settings.autoTempCalibration : true;
        
        const autoCalStatusEl = document.getElementById("auto-cal-status");
        if (settings.isAutoCalibrating) {
          autoCalStatusEl.textContent = "Calibrating... (~45m)";
          autoCalStatusEl.className = "badge bg-warning text-dark ms-2";
        } else {
          autoCalStatusEl.textContent = "Idle";
          autoCalStatusEl.className = "badge bg-secondary ms-2";
        }
        
        const lastAutoCalStatusEl = document.getElementById("last-auto-cal-status");
        if (settings.lastAutoCalStatus) {
            lastAutoCalStatusEl.textContent = settings.lastAutoCalStatus;
        }
        
        tempCompensationFactorEl.value = settings.tempCompensationFactor || 0.15;
        tempCompensationFactorValueEl.textContent = parseFloat(tempCompensationFactorEl.value).toFixed(2);

        if (tempCorrectionEnabledEl.checked) {
          tempCorrectionControlsEl.classList.remove('d-none');
        } else {
          tempCorrectionControlsEl.classList.add('d-none');
        }
        
        renderPageOrderList(settings.enabledPages);

        // Manually trigger UI updates that depend on these values
        updateBrightnessUI(settings);
        updateHourFormatUI(settings);
        toggleBrightnessSlider();
      }
      
      function updateDisplaySettingsUI(settings) {
        if (settings.backgroundColor) document.getElementById('background-color').value = settings.backgroundColor;
        if (settings.timeColor) document.getElementById('time-color').value = settings.timeColor;
        if (settings.todColor) document.getElementById('tod-color').value = settings.todColor;
        if (settings.secondsColor) document.getElementById('seconds-color').value = settings.secondsColor;
        if (settings.dayOfWeekColor) document.getElementById('day-of-week-color').value = settings.dayOfWeekColor;
        if (settings.dateColor) document.getElementById('date-color').value = settings.dateColor;
        if (settings.tempColor) document.getElementById('temp-color').value = settings.tempColor;
        if (settings.humidityColor) document.getElementById('humidity-color').value = settings.humidityColor;
        if (settings.weatherTempColor) document.getElementById('weather-temp-color').value = settings.weatherTempColor;
        if (settings.weatherForecastColor) document.getElementById('weather-forecast-color').value = settings.weatherForecastColor;
      }
      
      async function fetchGeneralSettings() {
        try {
          const response = await fetch('/api/settings');
          if (!response.ok) throw new Error('Failed to fetch general settings');
          const settings = await response.json();
          updateGeneralSettingsUI(settings);
        } catch (e) {
          console.error(e);
          setStatus(STATUS_INDICATORS.ERROR);
        }
      }

      async function fetchDisplaySettings() {
        try {
          const response = await fetch('/api/display');
          if (!response.ok) throw new Error('Failed to fetch display settings');
          const settings = await response.json();
          updateDisplaySettingsUI(settings);
        } catch (e) {
          console.error(e);
          setStatus(STATUS_INDICATORS.ERROR);
        }
      }

      async function saveGeneralSettings(event) {
        clearTimeout(saveGeneralTimeout); // Clear pending saves
        clearTimeout(saveDisplayTimeout);
        setStatus(STATUS_INDICATORS.SAVING);

        const settings = {
          autoBrightness: autoBrightnessEl.checked,
          offlineMode: offlineModeEl.checked,
          // send numeric raw values to the server
          brightness: parseInt(brightnessEl.value),
          autoBrightnessStartHour: parseInt(autoBrightnessStartHourEl.value),
          autoBrightnessEndHour: parseInt(autoBrightnessEndHourEl.value),
          dayBrightness: parseInt(dayBrightnessEl.value),
          nightBrightness: parseInt(nightBrightnessEl.value),
          use24HourFormat: twentyFourHourEl.checked,
          useCelsius: celsiusEl.checked,
          tempCorrectionEnabled: tempCorrectionEnabledEl.checked,
          autoTempCalibration: autoTempCalibrationEl.checked,
          screenFlipped: screenFlippedEl.checked,
          invertColors: invertColorsEl.checked,
          timezone: timezoneEl.value,
          defaultPage: parseInt(defaultPageEl.value),
          enabledPages: getEnabledPagesFromUI(),
          snoozeDuration: parseInt(document.getElementById('snooze-duration').value),
          dismissDuration: parseInt(document.getElementById('dismiss-duration').value),
          tempCorrection: parseFloat(document.getElementById('temp-correction').value),
          tempCompensationFactor: parseFloat(tempCompensationFactorEl.value)
        };

        if (!settings.useCelsius) {
          settings.tempCorrection = settings.tempCorrection * 5.0 / 9.0;
        }

        try {
          // Save general settings
          const saveSettingsResponse = await fetch('/api/settings/save', {
            method: 'POST',
            headers: { 'Content-Type': 'application/json' },
            body: JSON.stringify(settings)
          });
          if (!saveSettingsResponse.ok) throw new Error('Failed to save general settings');

          const target = event ? event.target : null;
          if (!target || (target.id !== 'temp-correction' && target.type !== 'range')) {
            await fetchGeneralSettings(); // Re-fetch to get new state (like actualBrightness)
          }
          setStatus(STATUS_INDICATORS.SAVED);
          
        } catch (e) {
          console.error(e);
          setStatus(STATUS_INDICATORS.ERROR);
          // Removed setTimeout that reverted to UNSAVED
        }
      }

      async function saveDisplaySettings() {
        clearTimeout(saveGeneralTimeout); // Clear pending saves
        clearTimeout(saveDisplayTimeout);
        setStatus(STATUS_INDICATORS.SAVING);

        const displaySettings = {};
        colorPickers.forEach(picker => {
          displaySettings[picker.name] = picker.value;
        });

        try {
          // Save display settings
          const saveDisplayResponse = await fetch('/api/display/save', {
            method: 'POST',
            headers: { 'Content-Type': 'application/json' },
            body: JSON.stringify(displaySettings)
          });
          if (!saveDisplayResponse.ok) throw new Error('Failed to save display settings');

          // After saving, fetch the new display state
          await fetchDisplaySettings(); // Re-fetch new state
          setStatus(STATUS_INDICATORS.SAVED);
        } catch (e) {
          console.error(e);
          setStatus(STATUS_INDICATORS.ERROR);
          // Removed setTimeout that reverted to UNSAVED
        }
      }
      
      // Update text labels in real-time as user slides
      brightnessEl.addEventListener('input', () => {
        brightnessValueEl.textContent = toPercent(brightnessEl.value);
      });
      dayBrightnessEl.addEventListener('input', () => {
        dayBrightnessValueEl.textContent = toPercent(dayBrightnessEl.value);
      });
      nightBrightnessEl.addEventListener('input', () => {
        nightBrightnessValueEl.textContent = toPercent(nightBrightnessEl.value);
      });
      
      // Update hour formats in real-time
      autoBrightnessStartHourEl.addEventListener('input', () => {
         autoBrightnessStartHourValueEl.textContent = formatHour(autoBrightnessStartHourEl.value, twentyFourHourEl.checked);
      });
      autoBrightnessEndHourEl.addEventListener('input', () => {
         autoBrightnessEndHourValueEl.textContent = formatHour(autoBrightnessEndHourEl.value, twentyFourHourEl.checked);
      });
      twentyFourHourEl.addEventListener('change', () => {
         autoBrightnessStartHourValueEl.textContent = formatHour(autoBrightnessStartHourEl.value, twentyFourHourEl.checked);
         autoBrightnessEndHourValueEl.textContent = formatHour(autoBrightnessEndHourEl.value, twentyFourHourEl.checked);
      });

      celsiusEl.addEventListener('change', () => {
        const tempCorrectionEl = document.getElementById('temp-correction');
        const tempCorrectionLabel = document.querySelector('label[for="temp-correction"]');
        let currentValue = parseFloat(tempCorrectionEl.value);

        if (celsiusEl.checked) {
          // We are switching TO Celsius, so the current value is in Fahrenheit
          currentValue = currentValue * 5.0 / 9.0;
          tempCorrectionLabel.innerHTML = `Temperature Correction (&deg;C)`;
        } else {
          // We are switching TO Fahrenheit, so the current value is in Celsius
          currentValue = currentValue * 9.0 / 5.0;
          tempCorrectionLabel.innerHTML = `Temperature Correction (&deg;F)`;
        }
        tempCorrectionEl.value = currentValue.toFixed(1);
      });

      tempCorrectionEnabledEl.addEventListener('change', () => {
        if (tempCorrectionEnabledEl.checked) {
          tempCorrectionControlsEl.classList.remove('d-none');
        } else {
          tempCorrectionControlsEl.classList.add('d-none');
        }
      });

      tempCorrectionEl.addEventListener('input', () => {
        let value = tempCorrectionEl.value;
        let decimalIndex = value.indexOf('.');
        if (decimalIndex !== -1 && value.length - decimalIndex > 2) {
          tempCorrectionEl.value = parseFloat(value).toFixed(1);
        }
      });

      tempCompensationFactorEl.addEventListener('input', () => {
        tempCompensationFactorValueEl.textContent = parseFloat(tempCompensationFactorEl.value).toFixed(2);
      });

      autoBrightnessEl.addEventListener('change', toggleBrightnessSlider);
      offlineModeEl.addEventListener('change', (e) => {
        if (offlineModeEl.checked) {
          const confirmed = confirm("Are you sure you want to enable Offline Mode? WiFi will be permanently disabled on next boot. The ONLY way to revert this is a Factory Reset. Press OK to proceed.");
          if (!confirmed) {
            offlineModeEl.checked = false;
          }
        }
      });
      
      // Use 'input' for sliders for real-time feedback, and 'change' for other inputs
      settingsForm.addEventListener('input', (e) => {
        // For sliders and the temp correction, save with a debounce
        if (e.target.type === 'range' || e.target.id === 'temp-correction') {
          handleGeneralInputChange(e);
        }
      });
      settingsForm.addEventListener('change', (e) => handleGeneralInputChange(e));
      displaySettingsForm.addEventListener('change', handleDisplayInputChange);
      
      document.addEventListener("DOMContentLoaded", () => {
        setStatus(STATUS_INDICATORS.SAVED);
        toggleBrightnessSlider(); // Set initial UI state for brightness sections
        fetchGeneralSettings();
        fetchDisplaySettings();
      });

      resetColorsBtn.addEventListener('click', async () => {
        if (confirm('Are you sure you want to reset all colors to their default values?')) {
          clearTimeout(saveGeneralTimeout); // Clear pending saves
          clearTimeout(saveDisplayTimeout);
          setStatus(STATUS_INDICATORS.SAVING);

          try {
            const response = await fetch('/api/display/reset', { method: 'POST' });
            if (response.ok) {
              setStatus(STATUS_INDICATORS.SAVED);
              await fetchDisplaySettings(); // Fetch and apply new default values
            } else {
              throw new Error('Failed to reset colors');
            }
          } catch (e) {
            console.error(e);
            setStatus(STATUS_INDICATORS.ERROR);
          }
        }
      });

      resetGeneralBtn.addEventListener('click', async () => {
        if (confirm('Are you sure you want to reset all general settings to their default values?')) {
          clearTimeout(saveGeneralTimeout); // Clear pending saves
          clearTimeout(saveDisplayTimeout);
          setStatus(STATUS_INDICATORS.SAVING);

          try {
            const response = await fetch('/api/settings/reset', { method: 'POST' });
            if (response.ok) {
              setStatus(STATUS_INDICATORS.SAVED);
              await fetchGeneralSettings(); // Fetch and apply new default values
            } else {
              throw new Error('Failed to reset general settings');
            }
          } catch (e) {
            console.error(e);
            setStatus(STATUS_INDICATORS.ERROR);
          }
        }
      });
    </script>

    <script src="https://cdn.jsdelivr.net/npm/bootstrap@5.3.3/dist/js/bootstrap.bundle.min.js"></script>
  </body>
</html>
)rawliteral";

/**
 * @brief The Alarm Settings page, enhanced with a modern, responsive UI.
 * Features auto-saving, collapsible sections, and clear status indicators.
 * Communicates with the device's backend via the original /api/alarms endpoints.
 */
const char ALARMS_PAGE_HTML[] PROGMEM = R"rawliteral(
<!DOCTYPE html>
<html data-bs-theme="dark">
  <head>
    <title>Alarm Settings</title>
    %HEAD%
    <style>
      :root {
        --btn-base-size: 2.5rem; /* 40px */
        --btn-min-size: 2.1rem; /* ~34px */
        --border-radius-round: 50%;
        --transition-speed: 0.3s;
      }

      .card {
        margin: auto;
      }

      .day-btn-group .btn {
        display: inline-flex;
        justify-content: center;
        align-items: center;
        border-radius: var(--border-radius-round);
        width: clamp(var(--btn-min-size), 8vw, var(--btn-base-size));
        aspect-ratio: 1 / 1;
        padding: 0;
        font-size: 0.9rem;
      }

      .alarm-header {
        cursor: pointer;
      }

      .collapse-icon {
        transition: transform var(--transition-speed) ease;
      }
      .collapse-icon.collapsed {
        transform: rotate(-90deg);
      }
      
      .status-indicator {
        font-size: 0.9rem;
        font-weight: bold;
        display: flex;
        align-items: center;
        gap: 0.4rem;
        min-width: 95px;
      }
    </style>
  </head>
  <body>
    <div class="container my-5">
      <div class="card shadow-sm">
        <div class="card-body">
          <div class="d-flex justify-content-between align-items-center mb-4">
            <h1 class="card-title m-0">Alarm Settings</h1>
            <div class="status-indicator"></div>
          </div>

          <div class="alert alert-info d-flex align-items-center" role="alert">
            <i class="bi bi-info-circle-fill me-2"></i>
            <div>Heads up! All your changes are saved automatically.</div>
          </div>

          <div id="alarms-container">
            <p class="text-center">Loading alarms...</p>
          </div>
          <div class="d-grid gap-2 mt-4">
            <button class="btn btn-success" id="add-alarm-btn" title="Add a new alarm."><i class="bi bi-plus-lg me-2"></i>Add Alarm</button>
            <a href="/" class="btn btn-secondary" title="Return to the main menu.">Back to Menu</a>
          </div>
        </div>
      </div>
    </div>

    <script src="https://cdn.jsdelivr.net/npm/bootstrap@5.3.3/dist/js/bootstrap.bundle.min.js"></script>

    <script>
      const DAY_MAP = { 1: "Su", 2: "M", 4: "Tu", 8: "W", 16: "Th", 32: "F", 64: "Sa" };
      const alarmsContainer = document.getElementById("alarms-container");
      const statusEl = document.querySelector(".status-indicator");

      const ERROR_DISPLAY_MS = 3000;
      let saveTimeout;

      const STATUS_INDICATORS = {
        SAVED:
          '<i class="bi bi-check-circle-fill text-success"></i> <span class="text-muted">Saved</span>',
        UNSAVED:
          '<i class="bi bi-pencil-fill text-warning"></i> <span class="text-warning">Unsaved</span>',
        SAVING:
          '<div class="spinner-border spinner-border-sm text-primary" role="status"></div> <span class="text-primary">Saving...</span>',
        ERROR:
          '<i class="bi bi-exclamation-triangle-fill text-danger"></i> <span class="text-danger">Error</span>',
      };

      function handleInputChange() {
        clearTimeout(saveTimeout);
        statusEl.innerHTML = STATUS_INDICATORS.UNSAVED;
        saveTimeout = setTimeout(saveAllAlarms, 50);
      }

      function renumberAlarms() {
        const cards = alarmsContainer.querySelectorAll('.card');
        cards.forEach((card, index) => {
            const title = card.querySelector('.card-title');
            if(title) title.textContent = `Alarm ${index + 1}`;
        });
      }

      function createAlarmCard(alarm, index) {
        const card = document.createElement("div");
        card.className = "card mb-3";
        card.dataset.id = alarm.id;
        // Use a random ID suffix for frontend DOM uniqueness if alarm.id is -1 (new)
        // or just use index to ensure uniqueness in DOM IDs
        const domId = alarm.id >= 0 ? alarm.id : `new-${index}-${Math.floor(Math.random() * 1000)}`;
        const collapseId = `collapse-alarm-${domId}`;

        let daysHtml = "";
        const dayKeys = [2, 4, 8, 16, 32, 64, 1];
        dayKeys.forEach((value) => {
          const label = DAY_MAP[value];
          const isActive = (alarm.days & value) > 0;
          daysHtml += `<button type="button" class="btn ${
            isActive ? "btn-primary" : "btn-outline-secondary"
          } day-btn" data-value="${value}" title="Toggle ${label}">${label}</button>`;
        });

        const displayTitle = `Alarm ${index + 1}`;

        const hasDays = alarm.days !== 0;
        const biweeklyChecked = alarm.biweekly ? "checked" : "";
        const biweeklyDisplay = hasDays ? "" : "d-none";

        card.innerHTML = `
        <div class="card-body">
          <div class="d-flex justify-content-between align-items-center alarm-header">
            <h5 class="card-title mb-0 flex-grow-1" data-bs-target="#${collapseId}" data-bs-toggle="collapse">${displayTitle}</h5>
            <div class="d-flex align-items-center">
                 <div class="form-check form-switch me-3">
                   <input class="form-check-input" type="checkbox" role="switch" ${
                     alarm.enabled ? "checked" : ""
                   } title="Enable or disable this alarm.">
                 </div>
                 <button class="btn btn-outline-danger btn-sm delete-btn" title="Delete this alarm"><i class="bi bi-trash"></i></button>
                 <i class="bi bi-chevron-down collapse-icon ms-3" data-bs-target="#${collapseId}" data-bs-toggle="collapse"></i>
            </div>
          </div>
          <div class="collapse" id="${collapseId}">
            <hr>
            <div class="mb-3">
              <label class="form-label">Time</label>
              <input type="time" class="form-control" value="${String(
                alarm.hour
              ).padStart(2, "0")}:${String(alarm.minute).padStart(
                2,
                "0"
              )}" title="Set the alarm time.">
            </div>
            <div class="mb-3">
              <label class="form-label">Repeat on</label>
              <div class="d-flex justify-content-around day-btn-group">${daysHtml}</div>
            </div>
            <div class="biweekly-section ${biweeklyDisplay}">
              <div class="form-check form-switch">
                <input class="form-check-input biweekly-toggle" type="checkbox" ${biweeklyChecked} title="Enable to repeat every other week instead of every week.">
                <label class="form-check-label">Every other week</label>
              </div>
              <div class="biweekly-parity ${alarm.biweekly ? '' : 'd-none'} mt-2">
                <div class="form-check form-check-inline">
                  <input class="form-check-input biweekly-even" type="radio" name="parity-${domId}" id="parity-even-${domId}" value="even" ${alarm.biweekly && !alarm.biweeklyOddWeek ? 'checked' : ''}>
                  <label class="form-check-label" for="parity-even-${domId}">Even Weeks</label>
                </div>
                <div class="form-check form-check-inline">
                  <input class="form-check-input biweekly-odd" type="radio" name="parity-${domId}" id="parity-odd-${domId}" value="odd" ${alarm.biweekly && alarm.biweeklyOddWeek ? 'checked' : ''}>
                  <label class="form-check-label" for="parity-odd-${domId}">Odd Weeks</label>
                </div>
              </div>
              <small class="text-muted biweekly-hint ${alarm.biweekly ? '' : 'd-none'}">This alarm will ring every 2 weeks on the selected days.</small>
            </div>
          </div>
        </div>
      `;

        const collapseElement = card.querySelector(`#${collapseId}`);
        const collapseIcon = card.querySelector(".collapse-icon");
        collapseElement.addEventListener("show.bs.collapse", () =>
          collapseIcon.classList.remove("collapsed")
        );
        collapseElement.addEventListener("hide.bs.collapse", () =>
          collapseIcon.classList.add("collapsed")
        );
        if (!collapseElement.classList.contains("show"))
          collapseIcon.classList.add("collapsed");
        
        // Delete button handler
        card.querySelector(".delete-btn").addEventListener("click", (e) => {
             e.stopPropagation(); // Prevent collapse toggle
             if (confirm("Delete this alarm?")) {
                 card.remove();
                 renumberAlarms();
                 handleInputChange();
             }
        });

        card.querySelectorAll(".day-btn").forEach((btn) => {
          btn.addEventListener("click", () => {
            btn.classList.toggle("btn-primary");
            btn.classList.toggle("btn-outline-secondary");
            // Show/hide biweekly toggle based on whether any days are selected
            const anyDaySelected = card.querySelector(".day-btn.btn-primary") !== null;
            const biweeklySection = card.querySelector(".biweekly-section");
            if (biweeklySection) {
              if (anyDaySelected) {
                biweeklySection.classList.remove("d-none");
              } else {
                biweeklySection.classList.add("d-none");
                // Also uncheck biweekly when no days are selected
                const biweeklyToggle = card.querySelector(".biweekly-toggle");
                if (biweeklyToggle) {
                  biweeklyToggle.checked = false;
                  const hint = card.querySelector(".biweekly-hint");
                  if (hint) hint.classList.add("d-none");
                }
              }
            }
            handleInputChange();
          });
        });

        // Biweekly toggle handler
        const biweeklyToggle = card.querySelector(".biweekly-toggle");
        if (biweeklyToggle) {
          biweeklyToggle.addEventListener("change", () => {
            const hint = card.querySelector(".biweekly-hint");
            const parity = card.querySelector(".biweekly-parity");
            if (hint) {
              if (biweeklyToggle.checked) {
                hint.classList.remove("d-none");
                if (parity) parity.classList.remove("d-none");
              } else {
                hint.classList.add("d-none");
                if (parity) parity.classList.add("d-none");
              }
            }
            handleInputChange();
          });
        }

        card.querySelectorAll('.biweekly-even, .biweekly-odd').forEach(radio => {
            radio.addEventListener("change", () => handleInputChange());
        });

        card
          .querySelector('input[type="time"]')
          .addEventListener("change", () => handleInputChange());
        card
          .querySelector('.form-check-input:not(.biweekly-toggle)')
          .addEventListener("change", () => handleInputChange());

        // Store biweeklyOddWeek in data attribute for round-tripping
        card.dataset.biweeklyOddWeek = alarm.biweeklyOddWeek ? "true" : "false";

        return card;
      }
      
      document.getElementById('add-alarm-btn').addEventListener('click', () => {
          // Count current cards to determine index and check limit
          const count = alarmsContainer.querySelectorAll('.card').length;
          const MAX_ALLOWED_ALARMS = 20; // Must match backend limit
          
          if (count >= MAX_ALLOWED_ALARMS) {
              alert(`Maximum number of alarms (${MAX_ALLOWED_ALARMS}) reached.`);
              return;
          }

          const newAlarm = {
              id: -1, // Indicates new alarm
              enabled: true,
              hour: 7,
              minute: 0,
              days: 0,
              biweekly: false,
              biweeklyOddWeek: false
          };
          
          const card = createAlarmCard(newAlarm, count);
          alarmsContainer.appendChild(card);
          // Auto-expand the new alarm
          const collapseEl = card.querySelector('.collapse');
          if (collapseEl) {
              const bsCollapse = new bootstrap.Collapse(collapseEl, { toggle: true });
          }
          renumberAlarms();
          handleInputChange();
      });

      async function loadAlarms() {
        alarmsContainer.innerHTML =
          '<p class="text-center">Loading alarms...</p>';
        try {
          const response = await fetch("/api/alarms");
          const alarms = await response.json();
          renderAlarms(alarms);
        } catch (e) {
          alarmsContainer.innerHTML =
            '<p class="text-center text-danger">Failed to load alarms.</p>';
        }
      }

      function renderAlarms(alarms) {
        alarmsContainer.innerHTML = "";
        // If empty, show nothing (or we could show one default one, but empty is valid now)
        if (!alarms) alarms = [];
        
        alarms.forEach((alarm, index) => {
          const cardElement = createAlarmCard(alarm, index);
          alarmsContainer.appendChild(cardElement);
        });
        statusEl.innerHTML = STATUS_INDICATORS.SAVED;
      }

      async function saveAllAlarms() {
        statusEl.innerHTML = STATUS_INDICATORS.SAVING;

        const allAlarmsData = [];
         alarmsContainer.querySelectorAll(".card").forEach((card) => {
          const alarmData = {
            id: parseInt(card.dataset.id),
            enabled: card.querySelector(".form-check-input:not(.biweekly-toggle)").checked,
            hour: parseInt(
              card.querySelector('input[type="time"]').value.split(":")[0]
            ),
            minute: parseInt(
              card.querySelector('input[type="time"]').value.split(":")[1]
            ),
            days: 0,
            biweekly: false
          };
          const oddRadio = card.querySelector(".biweekly-odd");
          const evenRadio = card.querySelector(".biweekly-even");
          if (oddRadio && evenRadio && (oddRadio.checked || evenRadio.checked)) {
            alarmData.biweeklyOddWeek = oddRadio.checked;
          }
          card.querySelectorAll(".day-btn.btn-primary").forEach((btn) => {
            alarmData.days |= parseInt(btn.dataset.value);
          });
          const biweeklyToggle = card.querySelector(".biweekly-toggle");
          if (biweeklyToggle && biweeklyToggle.checked && alarmData.days !== 0) {
            alarmData.biweekly = true;
          }
          allAlarmsData.push(alarmData);
        });

        try {
          await fetch("/api/alarms/save", {
            method: "POST",
            headers: { "Content-Type": "application/json" },
            body: JSON.stringify(allAlarmsData),
          });
          statusEl.innerHTML = STATUS_INDICATORS.SAVED;
        } catch (e) {
          statusEl.innerHTML = STATUS_INDICATORS.ERROR;
          setTimeout(() => {
            statusEl.innerHTML = STATUS_INDICATORS.UNSAVED;
          }, ERROR_DISPLAY_MS);
        }
      }

      document.addEventListener("DOMContentLoaded", loadAlarms);
    </script>
  </body>
</html>
)rawliteral";
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
