KennethDoerflein/ESP32Clock/src/ClockWebServer.cpp

/**
 * @file ClockWebServer.cpp
 * @brief Implements the ClockWebServer class for managing the web interface.
 *
 * This file contains the implementation of the web server, including all route
 * handlers, API endpoints, and the template processor for dynamic HTML content.
 * It handles both the initial captive portal setup and the main configuration
 * interface.
 */

#include "ClockWebServer.h"
#include "ConfigManager.h"
#include "DisplayManager.h"
#include "WiFiManager.h"
#include "WebContent.h"
#include <ArduinoJson.h>
#include <AsyncTCP.h>
#include <WiFi.h>
#include "SensorModule.h"
#include "Display.h"
#include "UpdateManager.h"
#include "SerialLog.h"
#include "NtpSync.h"
#include "AlarmManager.h"
#include "TimeManager.h"
#include "Constants.h"
#include "WeatherService.h"
#include "Utils.h"
#include <sys/time.h>
#include "esp_core_dump.h"
#include "esp_partition.h"

#if __has_include("version.h")
// This file exists, so we'll include it.
#include "version.h"
#else
// "version.h" was not found, so we'll include the backup.
#include "version.h.default"
#endif

/**
 * @brief Gets the singleton instance of the ClockWebServer.
 * @return A reference to the singleton instance.
 */
ClockWebServer &ClockWebServer::getInstance()
{
  static ClockWebServer instance;
  return instance;
}

/**
 * @brief Constructs a new ClockWebServer.
 * Initializes the web server on port 80.
 */
ClockWebServer::ClockWebServer() : server(80), _captivePortalActive(false) {}

/**
 * @brief Enables captive portal mode.
 *
 * Sets a flag that modifies the server's behavior on `begin()`. This should
 * be called before `begin()` if a captive portal is needed for initial setup.
 */
void ClockWebServer::enableCaptivePortal()
{
  _captivePortalActive = true;
}

/**
 * @brief Starts the web server and sets up all the routes.
 *
 * This is the main setup method for the web server. It checks if captive
 * portal mode is active and registers the appropriate set of URL handlers.
 * It also sets up API endpoints for interacting with the clock's configuration
 * and system functions.
 */
void ClockWebServer::begin()
{
  // Bind class methods to web server routes
  if (_captivePortalActive)
  {
    // --- Captive Portal Handlers ---

    // First, we handle the specific URLs that operating systems use for their
    // connectivity checks. Responding correctly to these prevents the OS from
    // disconnecting or opening its own browser window.
    server.on("/connecttest.txt", HTTP_GET, [this](AsyncWebServerRequest *request)
              { onCaptivePortalRedirect(request); });
    server.on("/generate_204", HTTP_GET, [this](AsyncWebServerRequest *request)
              { onCaptivePortalRedirect(request); });
    server.on("/hotspot-detect.html", HTTP_GET, [this](AsyncWebServerRequest *request)
              { onCaptivePortalRedirect(request); });

    // Next, we define the actual setup page that the user should see.
    // This is served from the root URL of the ESP32's IP address.
    server.on("/", HTTP_GET, [this](AsyncWebServerRequest *request)
              { onCaptivePortalRequest(request); });

    // Finally, we use the onNotFound handler as a catch-all. If the user's browser
    // requests any other page (e.g., google.com, msn.com), we don't serve content.
    // Instead, we issue an HTTP 302 Redirect, which tells the browser to go to
    // our root setup page. This is the key to reliably forcing the setup page to appear.
    server.onNotFound([this](AsyncWebServerRequest *request)
                      { onCaptivePortalRedirect(request); });
  }
  else
  {
    server.on("/", HTTP_GET, [this](AsyncWebServerRequest *request)
              { onRootRequest(request); });
    server.on("/wifi", HTTP_GET, [this](AsyncWebServerRequest *request)
              { onWifiRequest(request); });
    server.on("/settings", HTTP_GET, [this](AsyncWebServerRequest *request)
              { onSettingsRequest(request); });

    server.on("/alarms", HTTP_GET, [this](AsyncWebServerRequest *request)
              { onAlarmsRequest(request); });

    server.on("/weather", HTTP_GET, [this](AsyncWebServerRequest *request)
              { request->send_P(200, "text/html", WEATHER_PAGE_HTML, [this](const String &var)
                                { return processor(var); }); });

    // --- API Handlers for Weather ---
    server.on("/api/weather/location", HTTP_POST, [](AsyncWebServerRequest *request)
              {
        if (request->hasParam("address", true)) {
            String address = request->getParam("address", true)->value();
            
            if (address.length() == 0) {
               // Clear location
               ConfigManager::getInstance().setAddress("");
               ConfigManager::getInstance().setLat(0.0);
               ConfigManager::getInstance().setLon(0.0);
               request->send(200, "application/json", "{\"success\":true,\"resolvedAddress\":\"\",\"message\":\"Location cleared.\"}");
               return;
            }

            if (WeatherService::getInstance().resolveLocationAsync(address)) {
                request->send(200, "application/json", "{\"success\":true,\"message\":\"Search started.\",\"pending\":true}");
            } else {
                request->send(200, "application/json", "{\"success\":false,\"message\":\"Search already in progress or system busy.\"}");
            }
        } else {
            request->send(400, "application/json", "{\"success\":false,\"message\":\"Missing address parameter.\"}");
        } });

    server.on("/api/weather/geocoding-status", HTTP_GET, [](AsyncWebServerRequest *request)
              {
        // Read-only: config is already written by the background weather task.
        // This endpoint only reports the result so the UI can react.
        auto result = WeatherService::getInstance().getGeocodingResult();

        JsonDocument doc;
        doc["pending"] = result.pending;
        doc["success"] = result.success;

        if (!result.pending && result.success) {
            doc["resolvedAddress"] = result.resolvedAddress;
            doc["lat"] = result.lat;
            doc["lon"] = result.lon;
        }

        String response;
        serializeJson(doc, response);
        request->send(200, "application/json", response);
    });

    server.on("/api/weather", HTTP_GET, [](AsyncWebServerRequest *request)
              {
      auto& weatherService = WeatherService::getInstance();
      WeatherData data = weatherService.getCurrentWeather();
      JsonDocument doc;

      bool isMetric = ConfigManager::getInstance().isCelsius();
      float temp = data.temp; // WeatherService stores temp in Fahrenheit
      float feelsLike = data.feelsLike;
      float windSpeed = data.windSpeed;

      if (isMetric) {
          temp = (temp - 32.0f) * 5.0f / 9.0f;
          feelsLike = (feelsLike - 32.0f) * 5.0f / 9.0f;
          windSpeed = windSpeed * 1.60934f; // mph to km/h
      }

      doc["temp"] = temp;
      doc["feelsLike"] = feelsLike;
      doc["humidity"] = data.humidity;
      doc["windSpeed"] = windSpeed;
      doc["rainChance"] = data.rainChance;
      doc["condition"] = data.condition;
      
      doc["uvIndex"] = data.uvIndex;
      doc["cloudCover"] = data.cloudCover;
      doc["pressure"] = data.pressure; // hPa
      doc["visibility"] = data.visibility; // meters
      doc["windDirection"] = WeatherService::getWindDirectionStr(data.windDirection);
      doc["windGusts"] = isMetric ? (data.windGusts * 1.60934f) : data.windGusts; // Convert gusts if metric
      
      String sunrise = data.sunrise;
      String sunset = data.sunset;

      if (!ConfigManager::getInstance().is24HourFormat()) {
          auto to12h = [](String time) -> String {
              int sep = time.indexOf(':');
              if (sep == -1) return time;
              int h = time.substring(0, sep).toInt();
              String m = time.substring(sep + 1);
              String suffix = " AM";
              if (h >= 12) {
                  suffix = " PM";
                  if (h > 12) h -= 12;
              }
              if (h == 0) h = 12;
              return String(h) + ":" + m + suffix;
          };
          sunrise = to12h(sunrise);
          sunset = to12h(sunset);
      }

      doc["sunrise"] = sunrise;
      doc["sunset"] = sunset;

      doc["isValid"] = data.isValid;
      doc["unit"] = isMetric ? "C" : "F";
      doc["windUnit"] = isMetric ? "km/h" : "mph";
      
      String response;
      serializeJson(doc, response);
      request->send(200, "application/json", response); });

    server.on("/api/weather/sync", HTTP_POST, [](AsyncWebServerRequest *request)
              {
      WeatherService::getInstance().forceUpdate();
      request->send(200, "text/plain", "Weather sync started."); });

    // --- API Handlers for Alarms ---
    server.on("/api/alarms", HTTP_GET, [](AsyncWebServerRequest *request)
              {
      auto& config = ConfigManager::getInstance();
      JsonDocument doc;
      JsonArray alarmsArray = doc.to<JsonArray>();

      std::vector<Alarm> alarms = config.getAllAlarms();
      for (const auto &alarm : alarms) {
        JsonObject alarmObj = alarmsArray.add<JsonObject>();
        alarmObj["id"] = alarm.getId();
        alarmObj["enabled"] = alarm.isEnabled();
        alarmObj["hour"] = alarm.getHour();
        alarmObj["minute"] = alarm.getMinute();
        alarmObj["days"] = alarm.getDays();
        alarmObj["biweekly"] = alarm.isBiweekly();
        alarmObj["biweeklyOddWeek"] = alarm.isBiweeklyOddWeek();
      }
      
      String response;
      serializeJson(doc, response);
      request->send(200, "application/json", response); });

    server.on("/api/alarms/save", HTTP_POST, [](AsyncWebServerRequest *request)
              {
        if (!request->_tempObject) {
            request->send(400, "text/plain", "No payload");
            return;
        }
        std::vector<uint8_t>* buffer = (std::vector<uint8_t>*)request->_tempObject;
        
        // All data has been received.
          JsonDocument doc;
          DeserializationError error = deserializeJson(doc, buffer->data(), buffer->size());
          
          // Use a std::unique_ptr to ensure the buffer is deleted when the function returns,
          // safely keeping it alive while `doc` is processed (since ArduinoJson 7 uses zero-copy).
          std::unique_ptr<std::vector<uint8_t>> autoBuffer(buffer);
          request->_tempObject = nullptr;

          if (error) {
            request->send(400, "text/plain", "Invalid JSON");
            return;
          }

          JsonArray alarmsArray = doc.as<JsonArray>();
          if (alarmsArray.isNull()) {
            request->send(400, "text/plain", "Expected a JSON array");
            return;
          }

          if (alarmsArray.size() > MAX_ALLOWED_ALARMS) {
            request->send(400, "text/plain", "Too many alarms. Max limit is " + String(MAX_ALLOWED_ALARMS));
            return;
          }

          std::vector<Alarm> newAlarms;
          auto& config = ConfigManager::getInstance();

          for (JsonObject alarmObj : alarmsArray) {
            Alarm alarm;
            int id = alarmObj["id"] | -1;
            
            // If the alarm has a valid ID, try to get its existing state (for snooze)
            bool found = false;
            if (id >= 0) {
              Alarm existingAlarm = config.getAlarmById(id);
              if (existingAlarm.getId() != 255) {
                  alarm = existingAlarm; // Copy existing state
                  found = true;
              }
            }

            if (!found) {
              // New alarm (or ID not found, treat as new)
              alarm.setId(id); // -1 will be assigned a new ID by ConfigManager
            }

            bool isEnabled = alarmObj["enabled"] | false;
            
            // If the alarm is being disabled and it's the one currently ringing, stop it.
            if (!isEnabled && alarm.isEnabled() && AlarmManager::getInstance().isRinging() && AlarmManager::getInstance().getActiveAlarmId() == alarm.getId()) {
              AlarmManager::getInstance().stop();
            }

            alarm.setEnabled(isEnabled);
            alarm.setHour(alarmObj["hour"] | 6);
            alarm.setMinute(alarmObj["minute"] | 0);
            alarm.setDays(alarmObj["days"] | 0);

            bool wasBiweekly = alarm.isBiweekly();
            bool newBiweekly = alarmObj["biweekly"] | false;
            alarm.setBiweekly(newBiweekly);
            if (newBiweekly && !alarmObj["biweeklyOddWeek"].isNull()) {
              alarm.setBiweeklyOddWeek(alarmObj["biweeklyOddWeek"] | false);
            } else if (newBiweekly && !wasBiweekly) {
              // Auto-compute parity from current week when first enabling biweekly
              DateTime now = TimeManager::getInstance().getLocalTime();
              alarm.setBiweeklyOddWeek(Alarm::isOddWeek(now));
            }
            
            newAlarms.push_back(alarm);
          }

          // Check if the currently ringing alarm is missing from the new list (deleted)
          if (AlarmManager::getInstance().isRinging()) {
             int activeId = AlarmManager::getInstance().getActiveAlarmId();
             bool found = false;
             for(const auto& a : newAlarms) {
                 if (a.getId() == activeId) {
                     found = true;
                     break;
                 }
             }
             if (!found) {
                 AlarmManager::getInstance().stop();
             }
          }

          config.replaceAlarms(newAlarms);
          
          // Force an immediate update of the alarm cache and RTC hardware alarms
          TimeManager::getInstance().setNextAlarms();

          request->send(200, "text/plain", "Alarms saved successfully!");
    }, NULL, [](AsyncWebServerRequest *request, uint8_t *data, size_t len, size_t index, size_t total)
              {
        
        if (index == 0) {
          // Early-reject if Content-Length is known. If total == 0, client is using
          // chunked transfer — the cumulative check below is the backstop.
          if (total > 0 && total > 8192) {
            request->client()->close();
            return;
          }
          
          request->_tempObject = new std::vector<uint8_t>();
          request->onDisconnect([request]() {
            if (request->_tempObject) {
              delete (std::vector<uint8_t>*)request->_tempObject;
              request->_tempObject = nullptr;
            }
          });
        }

        if (!request->_tempObject) return;

        std::vector<uint8_t>* buffer = (std::vector<uint8_t>*)request->_tempObject;
        
        // Safety check for cumulative size
        if (buffer->size() + len > 8192) {
             delete buffer;
             request->_tempObject = nullptr;
             request->client()->close();
             return;
        }
        
        buffer->insert(buffer->end(), data, data + len);

         });

    // --- API Handlers for Settings ---
    server.on("/api/settings", HTTP_GET, [](AsyncWebServerRequest *request)
              {
      auto& config = ConfigManager::getInstance();
      JsonDocument doc;
      doc["autoBrightness"] = config.isAutoBrightness();
      doc["brightness"] = config.getBrightness();
      doc["autoBrightnessStartHour"] = config.getAutoBrightnessStartHour();
      doc["autoBrightnessEndHour"] = config.getAutoBrightnessEndHour();
      doc["dayBrightness"] = config.getDayBrightness();
      doc["nightBrightness"] = config.getNightBrightness();
      doc["actualBrightness"] = Display::getInstance().getActualBrightness();
      doc["use24HourFormat"] = config.is24HourFormat();
      doc["useCelsius"] = config.isCelsius();
      doc["screenFlipped"] = config.isScreenFlipped();
      doc["invertColors"] = config.isInvertColors();
      doc["timezone"] = config.getTimezone();
      doc["address"] = config.getAddress();
      doc["offlineMode"] = config.isOfflineMode();
      
      JsonArray pagesArray = doc["enabledPages"].to<JsonArray>();
      for (int pageId : config.getEnabledPages()) {
        pagesArray.add(pageId);
      }

      doc["defaultPage"] = config.getDefaultPage();
      doc["snoozeDuration"] = config.getSnoozeDuration();
      doc["dismissDuration"] = config.getDismissDuration();
      doc["tempCorrectionEnabled"] = config.isTempCorrectionEnabled();
      doc["autoTempCalibration"] = config.isAutoTempCalibration();
      doc["lastAutoCalStatus"] = config.getLastAutoCalStatus();
      doc["isAutoCalibrating"] = isAutoCalibrating();
      doc["tempCorrection"] = config.getTempCorrection();
      doc["tempCompensationFactor"] = config.getTempCompensationFactor();
      
      String response;
      serializeJson(doc, response);
      request->send(200, "application/json", response); });

    // API handler for settings save
    server.on(
        "/api/settings/save", HTTP_POST, [](AsyncWebServerRequest *request)
        {
        if (!request->_tempObject) {
            request->send(400, "text/plain", "No payload");
            return;
        }
        std::vector<uint8_t>* buffer = (std::vector<uint8_t>*)request->_tempObject;
        
        JsonDocument doc;
            DeserializationError error = deserializeJson(doc, buffer->data(), buffer->size());

            std::unique_ptr<std::vector<uint8_t>> autoBuffer(buffer);
            request->_tempObject = nullptr;

            if (error)
            {
              request->send(400, "text/plain", "Invalid JSON");
            }
            else
            {
              auto &config = ConfigManager::getInstance();
              String oldTimezone = config.getTimezone();
              String oldAddress = config.getAddress();
              bool oldScreenFlipped = config.isScreenFlipped();
              bool oldInvertColors = config.isInvertColors();
              float oldTempCorrection = config.getTempCorrection();
              bool oldTempCorrectionEnabled = config.isTempCorrectionEnabled();
              bool oldAutoTempCalibration = config.isAutoTempCalibration();
              float oldTempCompensationFactor = config.getTempCompensationFactor();
              bool oldOfflineMode = config.isOfflineMode();
              config.setAutoBrightness(doc["autoBrightness"]);
              config.setBrightness(doc["brightness"]);
              config.setAutoBrightnessStartHour(doc["autoBrightnessStartHour"]);
              config.setAutoBrightnessEndHour(doc["autoBrightnessEndHour"]);
              config.setDayBrightness(doc["dayBrightness"]);
              config.setNightBrightness(doc["nightBrightness"]);
              config.set24HourFormat(doc["use24HourFormat"]);
              config.setCelsius(doc["useCelsius"]);
              config.setScreenFlipped(doc["screenFlipped"]);
              config.setInvertColors(doc["invertColors"]);
              config.setTimezone(doc["timezone"]);
              if (doc["offlineMode"].is<bool>())
              {
                config.setOfflineMode(doc["offlineMode"]);
              }

              if (doc["enabledPages"].is<JsonArray>())
              {
                std::vector<int> pages;
                for (int id : doc["enabledPages"].as<JsonArray>())
                {
                  pages.push_back(id);
                }
                config.setEnabledPages(pages);
              }

              config.setDefaultPage(doc["defaultPage"]);
              config.setSnoozeDuration(doc["snoozeDuration"]);
              config.setDismissDuration(doc["dismissDuration"]);
              config.setTempCorrectionEnabled(doc["tempCorrectionEnabled"]);
              
              if (doc["autoTempCalibration"].is<bool>())
                config.setAutoTempCalibration(doc["autoTempCalibration"]);
              config.setTempCorrection(doc["tempCorrection"]);
              if (doc["tempCompensationFactor"].is<float>())
              {
                config.setTempCompensationFactor(doc["tempCompensationFactor"]);
              }

              if (oldScreenFlipped != config.isScreenFlipped())
              {
                Display::getInstance().updateRotation();
                DisplayManager::getInstance().requestFullRefresh();
              }

              if (oldInvertColors != config.isInvertColors())
              {
                Display::getInstance().updateInversion();
                DisplayManager::getInstance().requestFullRefresh();
              }

              if (oldTimezone != config.getTimezone())
              {
                startNtpSync();
              }

              if (oldTempCorrection != config.getTempCorrection() || oldTempCorrectionEnabled != config.isTempCorrectionEnabled() || oldAutoTempCalibration != config.isAutoTempCalibration() ||
                  oldTempCompensationFactor != config.getTempCompensationFactor())
              {
                handleSensorUpdates(true);
              }

              if (!oldOfflineMode && config.isOfflineMode())
              {
                request->onDisconnect([](){ SerialLog::getInstance().clearCrashLogMagic(); ESP.restart(); });
                request->send(200, "text/plain", "Entering offline mode. Rebooting...");
                return;
              }

              request->send(200, "text/plain", "Settings saved!");
            }
    },
        NULL,
        [](AsyncWebServerRequest *request, uint8_t *data, size_t len,
           size_t index, size_t total)
        {
          if (index == 0)
          {
            if (total > 0 && total > 4096) {
              request->client()->close();
              return;
            }
            request->_tempObject = new std::vector<uint8_t>();
            request->onDisconnect([request]() {
              if (request->_tempObject) {
                delete (std::vector<uint8_t>*)request->_tempObject;
                request->_tempObject = nullptr;
              }
            });
          }

          if (!request->_tempObject)
            return;

          std::vector<uint8_t> *buffer =
              (std::vector<uint8_t> *)request->_tempObject;

          if (buffer->size() + len > 4096) {
              delete buffer;
              request->_tempObject = nullptr;
              request->client()->close();
              return;
          }

          buffer->insert(buffer->end(), data, data + len);

          
        });

    server.on("/api/settings/reset", HTTP_POST, [](AsyncWebServerRequest *request)
              {
      auto &config = ConfigManager::getInstance();
      bool oldScreenFlipped = config.isScreenFlipped();
      config.resetGeneralSettingsToDefaults();
      if (oldScreenFlipped != config.isScreenFlipped())
      {
        Display::getInstance().updateRotation();
      }
      DisplayManager::getInstance().requestFullRefresh();

      request->send(200, "text/plain", "General settings reset!"); });

    // --- API Handlers for Display ---
    server.on("/api/display", HTTP_GET, [](AsyncWebServerRequest *request)
              {
      auto& config = ConfigManager::getInstance();
      JsonDocument doc;
      doc["backgroundColor"] = config.getBackgroundColor();
      doc["timeColor"] = config.getTimeColor();
      doc["todColor"] = config.getTodColor();
      doc["secondsColor"] = config.getSecondsColor();
      doc["dayOfWeekColor"] = config.getDayOfWeekColor();
      doc["dateColor"] = config.getDateColor();
      doc["tempColor"] = config.getTempColor();
      doc["humidityColor"] = config.getHumidityColor();
      doc["weatherTempColor"] = config.getWeatherTempColor();
      doc["weatherForecastColor"] = config.getWeatherForecastColor();
      
      String response;
      serializeJson(doc, response);
      request->send(200, "application/json", response); });

    server.on("/api/sensors", HTTP_GET, [](AsyncWebServerRequest *request)
              {
      JsonDocument doc;
      doc["bmeFound"] = isBmeFound();
      if (isBmeFound()) {
        doc["bmeTemp"] = String(getBmeTemperature(), 1);
        doc["bmeHumidity"] = String(getHumidity(), 1);
        doc["rawBmeTemp"] = String(getRawBmeTemperature(), 1);
        doc["compensationOffset"] = String(getCompensationOffset(), 1);
      }
      if (isRtcFound()) {
        doc["rtcTemp"] = String(getRtcTemperature(), 1);
      }
      doc["unit"] = ConfigManager::getInstance().isCelsius() ? "C" : "F";
      
      String response;
      serializeJson(doc, response);
      request->send(200, "application/json", response); });

    server.on("/api/system/stats", HTTP_GET, [](AsyncWebServerRequest *request)
              {
      JsonDocument doc;
      doc["freeHeap"] = ESP.getFreeHeap();
      doc["uptime"] = millis();
      doc["rssi"] = WiFi.RSSI();
      doc["coreTemp"] = String(getCoreTemperature(), 1);
      doc["unit"] = ConfigManager::getInstance().isCelsius() ? "C" : "F";
      
      String response;
      serializeJson(doc, response);
      request->send(200, "application/json", response); });

    server.on("/api/system/ntp-sync", HTTP_POST, [](AsyncWebServerRequest *request)
              {
      startNtpSync();
      request->send(200, "text/plain", "NTP sync started successfully."); });

    // --- Layer 5: Manual Browser Time Sync ---
    server.on(
        "/api/system/time", HTTP_POST, [](AsyncWebServerRequest *request)
        {
        if (!request->_tempObject) {
            request->send(400, "text/plain", "No payload");
            return;
        }
        std::vector<uint8_t>* buffer = (std::vector<uint8_t>*)request->_tempObject;
        
        JsonDocument doc;
            DeserializationError error = deserializeJson(doc, buffer->data(), buffer->size());
            std::unique_ptr<std::vector<uint8_t>> autoBuffer(buffer);
            request->_tempObject = nullptr;

            if (error)
            {
              request->send(400, "application/json", "{\"success\":false,\"message\":\"Invalid JSON\"}");
              return;
            }

            if (!doc["epoch"].is<unsigned long>())
            {
              request->send(400, "application/json", "{\"success\":false,\"message\":\"Missing epoch field\"}");
              return;
            }

            uint32_t rawEpoch = doc["epoch"].as<unsigned long>();
            DateTime time_to_set(rawEpoch);
            if (time_to_set.year() < 2024 || time_to_set.year() > 2099)
            {
              request->send(400, "application/json", "{\"success\":false,\"message\":\"Epoch out of valid range (2024-2099)\"}");
              return;
            }

            auto &logger = SerialLog::getInstance();

            // Log the old RTC time for drift diagnostics
            DateTime oldRtcTime = TimeManager::getInstance().getRTCTime();
            int64_t drift = 0;
            if (oldRtcTime.isValid() && oldRtcTime.year() >= 2024)
            {
              drift = (int64_t)oldRtcTime.unixtime() - (int64_t)rawEpoch;
              logger.printf("Browser time sync: RTC was %s by %lld seconds\n",
                            drift > 0 ? "ahead" : "behind",
                            (long long)abs(drift));
            }

            // Write to hardware RTC (UTC)
            TimeManager::getInstance().adjustRTC(time_to_set);

            // Verify the write
            DateTime readback = TimeManager::getInstance().getRTCTime();
            int64_t writeError = abs((int64_t)readback.unixtime() - (int64_t)rawEpoch);
            if (writeError > 2)
            {
              logger.printf("WARNING: Browser sync RTC write verification failed! delta=%lld\n", (long long)writeError);
              request->send(500, "application/json", "{\"success\":false,\"message\":\"RTC write verification failed\"}");
              return;
            }

            // Update the system clock
            struct timeval tv;
            tv.tv_sec = rawEpoch;
            tv.tv_usec = 0;
            settimeofday(&tv, nullptr);

            // Immediately evaluate DST transition for the new time
            TimeManager::getInstance().checkDST();

            // Check for missed alarms across the sync jump and re-arm RTC hardware alarms
            time_t oldEpoch = (time_t)oldRtcTime.unixtime();
            TimeManager::getInstance().checkMissedAlarmsWindow(oldEpoch, rawEpoch);
            TimeManager::getInstance().setNextAlarms();

            logger.printf("Browser time sync complete: %04d-%02d-%02d %02d:%02d:%02d UTC\n",
                          time_to_set.year(), time_to_set.month(), time_to_set.day(),
                          time_to_set.hour(), time_to_set.minute(), time_to_set.second());

            request->send(200, "application/json", "{\"success\":true,\"message\":\"Time synchronized successfully\"}");
    },
        NULL,
        [](AsyncWebServerRequest *request, uint8_t *data, size_t len,
           size_t index, size_t total)
        {
          if (index == 0)
          {
            if (total > 0 && total > 256) {
              request->client()->close();
              return;
            }
            request->_tempObject = new std::vector<uint8_t>();
            request->onDisconnect([request]() {
              if (request->_tempObject) {
                delete (std::vector<uint8_t>*)request->_tempObject;
                request->_tempObject = nullptr;
              }
            });
          }

          if (!request->_tempObject)
            return;

          std::vector<uint8_t> *buffer =
              (std::vector<uint8_t> *)request->_tempObject;

          if (buffer->size() + len > 256) {
              delete buffer;
              request->_tempObject = nullptr;
              request->client()->close();
              return;
          }

          buffer->insert(buffer->end(), data, data + len);

          
        });

    server.on(
        "/api/display/save", HTTP_POST, [](AsyncWebServerRequest *request)
        {
        if (!request->_tempObject) {
            request->send(400, "text/plain", "No payload");
            return;
        }
        std::vector<uint8_t>* buffer = (std::vector<uint8_t>*)request->_tempObject;
        
        JsonDocument doc;
            DeserializationError error = deserializeJson(doc, buffer->data(), buffer->size());
            std::unique_ptr<std::vector<uint8_t>> autoBuffer(buffer);
            request->_tempObject = nullptr;

            if (error)
            {
              request->send(400, "text/plain", "Invalid JSON");
            }
            else
            {
              auto &config = ConfigManager::getInstance();
              String oldBgColor = config.getBackgroundColor();
              String newBgColor = doc["backgroundColor"].as<String>();

              config.setBackgroundColor(newBgColor);
              config.setTimeColor(doc["timeColor"].as<String>());
              config.setTodColor(doc["todColor"].as<String>());
              config.setSecondsColor(doc["secondsColor"].as<String>());
              config.setDayOfWeekColor(doc["dayOfWeekColor"].as<String>());
              config.setDateColor(doc["dateColor"].as<String>());
              config.setTempColor(doc["tempColor"].as<String>());
              config.setHumidityColor(doc["humidityColor"].as<String>());
              config.setWeatherTempColor(doc["weatherTempColor"].as<String>());
              config.setWeatherForecastColor(doc["weatherForecastColor"].as<String>());

              if (oldBgColor != newBgColor)
              {
                DisplayManager::getInstance().requestFullRefresh();
              }
              else
              {
                DisplayManager::getInstance().requestPartialRefresh();
              }

              request->send(200, "text/plain", "Display settings saved!");
            }
    },
        NULL,
        [](AsyncWebServerRequest *request, uint8_t *data, size_t len,
           size_t index, size_t total)
        {
          if (index == 0)
          {
            // Early-reject on known Content-Length; chunked fallback handled cumulatively below.
            if (total > 0 && total > 4096) {
              request->client()->close();
              return;
            }
            request->_tempObject = new std::vector<uint8_t>();
            request->onDisconnect([request]() {
              if (request->_tempObject) {
                delete (std::vector<uint8_t>*)request->_tempObject;
                request->_tempObject = nullptr;
              }
            });
          }

          if (!request->_tempObject)
            return;

          std::vector<uint8_t> *buffer =
              (std::vector<uint8_t> *)request->_tempObject;

          if (buffer->size() + len > 4096) {
              delete buffer;
              request->_tempObject = nullptr;
              request->client()->close();
              return;
          }

          buffer->insert(buffer->end(), data, data + len);

          
        });

    server.on("/api/display/reset", HTTP_POST, [](AsyncWebServerRequest *request)
              {
      auto &config = ConfigManager::getInstance();
      config.resetDisplayToDefaults();
      DisplayManager::getInstance().requestFullRefresh();

      request->send(200, "text/plain", "Display settings reset!"); });

    server.on("/api/wifi/hostname", HTTP_POST, [](AsyncWebServerRequest *request)
              {
        if (request->hasParam("hostname", true)) {
            String hostname = request->getParam("hostname", true)->value();

            if (!isValidHostname(hostname)) {
                request->send(400, "text/plain", "Invalid hostname. Use 1-63 alphanumeric characters or hyphens (not at start/end).");
                return;
            }

            WiFiManager::getInstance().setHostname(hostname);
            request->send(200, "text/plain", "Hostname saved. Rebooting...");
            request->onDisconnect([](){ SerialLog::getInstance().clearCrashLogMagic(); ESP.restart(); });
        } else {
            request->send(400, "text/plain", "Hostname not provided.");
        } });

    server.on("/reboot", HTTP_GET, [](AsyncWebServerRequest *request)
              {
      request->send(200, "text/plain", "Rebooting...");
      request->onDisconnect([](){ SerialLog::getInstance().clearCrashLogMagic(); ESP.restart(); }); });

    server.on("/factory-reset", HTTP_GET, [](AsyncWebServerRequest *request)
              {
      if (UpdateManager::getInstance().isUpdateInProgress())
      {
        request->send(409, "text/plain", "Update in progress. Cannot perform factory reset.");
        return;
      }
      request->send(200, "text/plain", "Performing factory reset...");
      request->onDisconnect([](){ 
        ConfigManager::getInstance().factoryReset();
        SerialLog::getInstance().clearCrashLogMagic();
        ESP.restart(); 
      }); });

    server.on("/factory-reset-except-wifi", HTTP_GET, [](AsyncWebServerRequest *request)
              {
      if (UpdateManager::getInstance().isUpdateInProgress())
      {
        request->send(409, "text/plain", "Update in progress. Cannot perform factory reset.");
        return;
      }
      request->send(200, "text/plain", "Performing factory reset and keeping WiFi credentials...");
      request->onDisconnect([](){ 
        ConfigManager::getInstance().factoryResetExceptWiFi();
        SerialLog::getInstance().clearCrashLogMagic();
        ESP.restart(); 
      }); });

    server.on("/system", HTTP_GET, [this](AsyncWebServerRequest *request)
              { request->send_P(200, "text/html", SYSTEM_PAGE_HTML, [this](const String &var)
                                { return processor(var); }); });

    server.on(
        "/update", HTTP_POST,
        [](AsyncWebServerRequest *request)
        {
          // This handler is intentionally empty. The response is sent in the upload handler.
        },
        [](AsyncWebServerRequest *request, String filename, size_t index,
           uint8_t *data, size_t len, bool final)
        {
          if (index == 0) {
              request->onDisconnect([]() {
                  if (UpdateManager::getInstance().isUpdateInProgress()) {
                      UpdateManager::getInstance().abortUpdate();
                  }
              });
          }

          if (UpdateManager::getInstance().isUpdateInProgress() && index == 0)
          {
            request->send(409, "text/plain", "An update is already in progress.");
            return;
          }
          UpdateManager::getInstance().handleFileUpload(data, len, index, request->contentLength());
          if (final)
          {
            if (UpdateManager::getInstance().endUpdate())
            {
              request->onDisconnect([](){ SerialLog::getInstance().clearCrashLogMagic(); ESP.restart(); });
              request->send(200, "text/plain", "Update successful! Rebooting...");
            }
            else
            {
              request->send(500, "text/plain", "Update failed. Check serial monitor for details.");
            }
          }
        });

    server.on("/api/update/check", HTTP_POST, [](AsyncWebServerRequest *request)
              {
      String result = UpdateManager::getInstance().checkForUpdate();
      request->send(200, "application/json", result); });

    server.on("/api/update/github", HTTP_POST, [](AsyncWebServerRequest *request)
              {
      String status = UpdateManager::getInstance().handleGithubUpdate();
      request->send(200, "text/plain", status); });

    server.on("/api/update/status", HTTP_GET, [](AsyncWebServerRequest *request)
              {
      bool inProgress = UpdateManager::getInstance().isUpdateInProgress();
      request->send(200, "application/json", String("{\"inProgress\":") + (inProgress ? "true" : "false") + "}"); });

    server.on("/api/log/download", HTTP_GET, [](AsyncWebServerRequest *request)
              {
        SerialLog::getInstance().lock();
        if (!LittleFS.exists(SerialLog::getLogFilePath()))
        {
          SerialLog::getInstance().unlock();
          request->send(404, "text/plain", "Log file not found");
          return;
        }
        AsyncWebServerResponse *response = request->beginChunkedResponse("text/plain", [](uint8_t *buffer, size_t maxLen, size_t index) -> size_t {
            SerialLog::getInstance().lock();
            size_t len = 0;
            {
                File f = LittleFS.open(SerialLog::getLogFilePath(), "r");
                if (f) {
                    if (index < f.size()) {
                        f.seek(index);
                        len = f.read(buffer, maxLen);
                    }
                    f.close();
                }
            }
            SerialLog::getInstance().unlock();
            return len;
        });
        
        SerialLog::getInstance().unlock();
        if (response == nullptr)
        {
          request->send(500, "text/plain", "Internal Server Error: Could not create response");
          return;
        }
        response->addHeader("Content-Disposition", "attachment; filename=\"system.log\"");
        request->send(response); });

    server.on("/api/log/rotate", HTTP_POST, [](AsyncWebServerRequest *request)
              {
      SerialLog::getInstance().rotate();
      request->send(200, "text/plain", "Log rotated successfully."); });

    server.on("/api/crash/download", HTTP_GET, [](AsyncWebServerRequest *request)
              {
        SerialLog::getInstance().lock();
        if (!LittleFS.exists(SerialLog::getCrashLogFilePath()))
        {
          SerialLog::getInstance().unlock();
          request->send(404, "text/plain", "Crash log file not found");
          return;
        }
        AsyncWebServerResponse *response = request->beginChunkedResponse("text/plain", [](uint8_t *buffer, size_t maxLen, size_t index) -> size_t {
            SerialLog::getInstance().lock();
            size_t len = 0;
            {
                File f = LittleFS.open(SerialLog::getCrashLogFilePath(), "r");
                if (f) {
                    if (index < f.size()) {
                        f.seek(index);
                        len = f.read(buffer, maxLen);
                    }
                    f.close();
                }
            }
            SerialLog::getInstance().unlock();
            return len;
        });

        SerialLog::getInstance().unlock();
        if (response == nullptr)
        {
          request->send(500, "text/plain", "Internal Server Error: Could not create response");
          return;
        }
        response->addHeader("Content-Disposition", "attachment; filename=\"crash.log\"");
        request->send(response); });

    server.on("/api/crash/clear", HTTP_POST, [](AsyncWebServerRequest *request)
              {
        SerialLog::getInstance().lock();
        LittleFS.remove(SerialLog::getCrashLogFilePath());
        String oldCrashPath = String(SerialLog::getCrashLogFilePath()) + ".old";
        LittleFS.remove(oldCrashPath);
        SerialLog::getInstance().unlock();
        request->send(200, "text/plain", "Crash log cleared successfully."); });

    server.on("/api/crash/coredump", HTTP_GET, [](AsyncWebServerRequest *request)
              {
        size_t addr = 0;
        size_t size = 0;
        esp_err_t err = esp_core_dump_image_get(&addr, &size);

        if (err == ESP_ERR_NOT_FOUND || size == 0)
        {
          request->send(404, "text/plain", "No core dump found in flash");
          return;
        }

        const esp_partition_t *pt = esp_partition_find_first(
                                        ESP_PARTITION_TYPE_DATA,
                                        ESP_PARTITION_SUBTYPE_DATA_COREDUMP,
                                        NULL);
        if (pt == NULL)
        {
          request->send(500, "text/plain", "Core dump partition not found");
          return;
        }

        AsyncWebServerResponse *response = request->beginChunkedResponse(
            "application/octet-stream",
            [pt, size](uint8_t *buffer, size_t maxLen, size_t index) -> size_t {
                if (index >= size) {
                    return 0; // EOF
                }
                size_t remaining = size - index;
                size_t toRead = (remaining > maxLen) ? maxLen : remaining;

                esp_err_t readErr = esp_partition_read(pt, index, buffer, toRead);
                if (readErr != ESP_OK) {
                    return 0; // Error / EOF
                }
                return toRead;
            }
        );

        response->addHeader("Content-Disposition", "attachment; filename=\"coredump.bin\"");
        request->send(response); });

    server.on("/api/crash/coredump/clear", HTTP_POST, [](AsyncWebServerRequest *request)
              {
        esp_err_t err = esp_core_dump_image_erase();
        if (err == ESP_OK)
        {
          request->send(200, "text/plain", "Core dump erased successfully");
        }
        else
        {
          request->send(500, "text/plain", "Failed to erase core dump");
        } });

    SerialLog::getInstance().begin(&server);
  }

  // This route is shared between normal and captive portal modes.
  server.on("/wifi/save", HTTP_POST, [this](AsyncWebServerRequest *request)
            { onWifiSaveRequest(request); });

  server.on("/wifi/test", HTTP_POST, [this](AsyncWebServerRequest *request)
            { onWifiTestRequest(request); });

  server.on("/wifi/status", HTTP_GET, [this](AsyncWebServerRequest *request)
            { onWifiStatusRequest(request); });

  server.on("/api/wifi/scan", HTTP_GET, [](AsyncWebServerRequest *request)
            {
    auto &wifiManager = WiFiManager::getInstance();
    if (request->hasParam("start") && request->getParam("start")->value() == "true")
    {
      wifiManager.startScan();
      // Immediately return a scanning status
      request->send(200, "application/json", "{\"status\":\"scanning\"}");
    }
    else
    {
      String json = wifiManager.getScanResults();
      request->send(200, "application/json", json);
    } });

  server.begin();
}

/**
 * @brief Handles requests to the root URL ("/").
 * Serves the main index page.
 * @param request The incoming web request.
 */
void ClockWebServer::onRootRequest(AsyncWebServerRequest *request)
{
  request->send_P(200, "text/html", INDEX_HTML, [this](const String &var)
                  { return processor(var); });
}

/**
 * @brief Handles requests for the WiFi configuration page.
 * @param request The incoming web request.
 */
void ClockWebServer::onWifiRequest(AsyncWebServerRequest *request)
{
  request->send_P(200, "text/html", WIFI_CONFIG_HTML, [this](const String &var)
                  { return processor(var); });
}

/**
 * @brief Handles requests for the settings page.
 * @param request The incoming web request.
 */
void ClockWebServer::onSettingsRequest(AsyncWebServerRequest *request)
{
  request->send_P(200, "text/html", SETTINGS_PAGE_HTML, [this](const String &var)
                  { return settingsProcessor(var); });
}

/**
 * @brief Handles requests for the alarms configuration page.
 * @param request The incoming web request.
 */
void ClockWebServer::onAlarmsRequest(AsyncWebServerRequest *request)
{
  request->send_P(200, "text/html", ALARMS_PAGE_HTML, [this](const String &var)
                  { return processor(var); });
}

/**
 * @brief Handles the form submission for saving WiFi credentials.
 *
 * This function's behavior depends on the mode. In captive portal mode, it
 * starts a non-blocking connection test. In normal mode, it saves the
 * credentials and reboots the device.
 *
 * @param request The incoming web request.
 */
void ClockWebServer::onWifiSaveRequest(AsyncWebServerRequest *request)
{
  String ssid = request->arg("ssid");
  if (ssid.length() == 0)
  {
    request->send(400, "text/plain", "SSID cannot be empty.");
    return;
  }
  String password = request->arg("password");

  auto &wifiManager = WiFiManager::getInstance();
  if (wifiManager.isCaptivePortal())
  {
    // In captive portal, start a non-blocking test and let the client poll for status.
    wifiManager.startConnectionTest(ssid, password, true);
    request->send(200, "text/plain", "Test started. Polling for status...");
  }
  else
  {
    // If not in captive portal, just save, reboot, and apply the new settings.
    request->onDisconnect([ssid, password]() {
      WiFiManager::getInstance().saveCredentialsAndReboot(ssid, password);
    });
    request->send(200, "text/plain", "Credentials saved. Rebooting to connect...");
  }
}

/**
 * @brief Handles a request to test WiFi credentials without saving them.
 * @param request The incoming web request.
 */
void ClockWebServer::onWifiTestRequest(AsyncWebServerRequest *request)
{
  String ssid = request->arg("ssid");
  if (ssid.length() == 0)
  {
    request->send(400, "text/plain", "SSID cannot be empty.");
    return;
  }
  String password = request->arg("password");

  // "Test" only uses polling, it never saves the credentials.
  WiFiManager::getInstance().startConnectionTest(ssid, password, false);
  request->send(200, "text/plain", "Test started. Polling for status...");
}

/**
 * @brief Handles API requests for the status of a WiFi connection test.
 *
 * This is used by the client to poll for the result of a connection test
 * initiated by `onWifiSaveRequest` or `onWifiTestRequest`.
 *
 * @param request The incoming web request.
 */
void ClockWebServer::onWifiStatusRequest(AsyncWebServerRequest *request)
{
  auto &wifiManager = WiFiManager::getInstance();
  auto status = wifiManager.getConnectionTestStatus();
  switch (status)
  {
  case WiFiManager::TEST_IN_PROGRESS:
    request->send(202, "text/plain", "testing");
    break;
  case WiFiManager::TEST_SUCCESS:
    if (wifiManager.isPendingReboot())
    {
      request->onDisconnect([](){ SerialLog::getInstance().clearCrashLogMagic(); ESP.restart(); });
    }
    request->send(200, "text/plain", "success");
    wifiManager.resetConnectionTestStatus();
    break;
  case WiFiManager::TEST_FAILED:
    request->send(401, "text/plain", "failed");
    wifiManager.resetConnectionTestStatus();
    break;
  case WiFiManager::TEST_IDLE:
  default:
    request->send(200, "text/plain", "idle");
    break;
  }
}

/**
 * @brief Serves the simplified WiFi setup page for the captive portal.
 * @param request The incoming web request.
 */
void ClockWebServer::onCaptivePortalRequest(AsyncWebServerRequest *request)
{
  request->send_P(200, "text/html", SIMPLE_WIFI_SETUP_HTML);
}

/**
 * @brief Handles captive portal redirection for various operating systems.
 * @param request The incoming web request.
 */
void ClockWebServer::onCaptivePortalRedirect(AsyncWebServerRequest *request)
{
  AsyncWebServerResponse *response = request->beginResponse(302);
  response->addHeader("Location", "http://" + WiFi.softAPIP().toString());
  request->send(response);
}

/**
 * @brief Converts a raw brightness value (0-255) to a percentage string.
 * @param brightness The raw brightness value.
 * @return A string representing the brightness as a percentage (e.g., "50%").
 */
String brightnessToPercent(int brightness)
{
  // Clamp the value to the allowed range
  brightness = max(BRIGHTNESS_MIN, min(BRIGHTNESS_MAX, brightness));
  // Map the value to a percentage
  int percentage = map(brightness, BRIGHTNESS_MIN, BRIGHTNESS_MAX, 0, 100);
  return String(percentage) + "&#37;";
}

/**
 * @brief Formats an hour value for display in the web UI.
 * @param hour The hour to format (0-23).
 * @param is24Hour True if the display should be in 24-hour format.
 * @return A formatted string (e.g., "07", "12 PM").
 */
String formatHour(int hour, bool is24Hour)
{
  if (is24Hour)
  {
    if (hour < 10)
    {
      return "0" + String(hour);
    }
    return String(hour);
  }
  else
  {
    if (hour == 0)
      return "12 AM";
    if (hour == 12)
      return "12 PM";
    if (hour < 12)
      return String(hour) + " AM";
    return String(hour - 12) + " PM";
  }
}

/**
 * @brief Sets up the mDNS responder.
 *
 * This allows the device to be accessed on the local network using a
 * hostname like "ESP32Clock-XXXXXX.local".
 */
void ClockWebServer::setupMDNS()
{
  // Restart the mDNS responder to ensure a clean state
  MDNS.end();

  // Start the mDNS responder for ESP32Clock-XXXXXX.local
  String hostname = WiFiManager::getInstance().getHostname();
  if (MDNS.begin(hostname.c_str()))
  {
    SerialLog::getInstance().print("mDNS responder started\n");
    MDNS.addService("http", "tcp", 80); // Advertise the web server
  }
  else
  {
    SerialLog::getInstance().print("Error starting mDNS!\n");
  }
}

/**
 * @brief Processes placeholders in the HTML templates.
 *
 * This function is used as a callback by the web server to replace
 * placeholders (like `%%FIRMWARE_VERSION%%`) in the HTML files with
 * dynamic values.
 *
 * @param var The name of the placeholder variable.
 * @return The value to be substituted for the placeholder.
 */
String ClockWebServer::processor(const String &var)
{
  if (var == "HEAD")
    return BOOTSTRAP_HEAD;
  if (var == "WIFI_PAGE_TITLE")
    return WiFiManager::getInstance().isCaptivePortal() ? "WiFi Setup" : "Configure WiFi";
  if (var == "BACK_BUTTON_CLASS")
    return WiFiManager::getInstance().isCaptivePortal() ? "d-none" : "";
  if (var == "FIRMWARE_VERSION")
    return FIRMWARE_VERSION;
  if (var == "IP_ADDRESS")
    return WiFi.localIP().toString();
  if (var == "HOSTNAME")
    return WiFiManager::getInstance().getHostname();
  if (var == "SERIAL_LOG_TAB")
  {
    return SERIAL_LOG_TAB_HTML;
  }
  if (var == "SERIAL_LOG_TAB_PANE")
  {
    return SERIAL_LOG_TAB_PANE_HTML;
  }
  if (var == "SERIAL_LOG_SCRIPT")
  {
    return SERIAL_LOG_SCRIPT_JS;
  }
  if (var == "ADDRESS")
  {
    return ConfigManager::getInstance().getAddress();
  }

  return String();
}

struct TimezoneInfo
{
  const char *posixString;
  const char *placeholder;
};

static const TimezoneInfo timezones[] = {
    {"EST5EDT,M3.2.0/2:00,M11.1.0/2:00", "TIMEZONE_SELECTED_EST"},
    {"CST6CDT,M3.2.0/2:00,M11.1.0/2:00", "TIMEZONE_SELECTED_CST"},
    {"MST7MDT,M3.2.0/2:00,M11.1.0/2:00", "TIMEZONE_SELECTED_MST"},
    {"PST8PDT,M3.2.0/2:00,M11.1.0/2:00", "TIMEZONE_SELECTED_PST"},
    {"MST7", "TIMEZONE_SELECTED_AZ"},
    {"AKST9AKDT,M3.2.0/2:00,M11.1.0/2:00", "TIMEZONE_SELECTED_AK"},
    {"HST10", "TIMEZONE_SELECTED_HI"}};

/**
 * @brief A specialized template processor for the settings page.
 *
 * This extends the base processor with additional placeholders specific to
 * the settings and display configuration pages.
 *
 * @param var The name of the placeholder variable.
 * @return The value to be substituted.
 */
String ClockWebServer::settingsProcessor(const String &var)
{
  auto &config = ConfigManager::getInstance();
  String value = processor(var);
  if (value != String())
  {
    return value;
  }

  if (var == "BRIGHTNESS_MIN")
    return String(BRIGHTNESS_MIN);
  if (var == "BRIGHTNESS_MAX")
    return String(BRIGHTNESS_MAX);
  if (var == "AUTO_BRIGHTNESS_CHECKED")
    return config.isAutoBrightness() ? "checked" : "";
  if (var == "OFFLINE_MODE_CHECKED")
    return config.isOfflineMode() ? "checked" : "";
  if (var == "AUTO_BRIGHTNESS_START_HOUR")
    return String(config.getAutoBrightnessStartHour());
  if (var == "AUTO_BRIGHTNESS_START_HOUR_VALUE")
    return String(formatHour(config.getAutoBrightnessStartHour(), config.is24HourFormat()));
  if (var == "AUTO_BRIGHTNESS_END_HOUR")
    return String(config.getAutoBrightnessEndHour());
  if (var == "AUTO_BRIGHTNESS_END_HOUR_VALUE")
    return String(formatHour(config.getAutoBrightnessEndHour(), config.is24HourFormat()));
  if (var == "DAY_BRIGHTNESS")
    return String(config.getDayBrightness());
  if (var == "DAY_BRIGHTNESS_VALUE")
    return String(brightnessToPercent(config.getDayBrightness()));
  if (var == "NIGHT_BRIGHTNESS")
    return String(config.getNightBrightness());
  if (var == "NIGHT_BRIGHTNESS_VALUE")
    return String(brightnessToPercent(config.getNightBrightness()));
  if (var == "BRIGHTNESS")
    return String(Display::getInstance().getActualBrightness());
  if (var == "BRIGHTNESS_VALUE")
    return String(brightnessToPercent(Display::getInstance().getActualBrightness()));
  if (var == "USE_24_HOUR_FORMAT_CHECKED")
    return config.is24HourFormat() ? "checked" : "";
  if (var == "USE_CELSIUS_CHECKED")
    return config.isCelsius() ? "checked" : "";
  if (var == "AUTO_BRIGHTNESS_CONTROLS_CLASS")
    return config.isAutoBrightness() ? "" : "d-none";
  if (var == "MANUAL_BRIGHTNESS_CLASS")
    return config.isAutoBrightness() ? "d-none" : "";
  if (var == "SCREEN_FLIPPED_CHECKED")
    return config.isScreenFlipped() ? "checked" : "";
  if (var == "INVERT_COLORS_CHECKED")
    return config.isInvertColors() ? "checked" : "";
  if (var == "BACKGROUND_COLOR")
    return config.getBackgroundColor();
  if (var == "TIME_COLOR")
    return config.getTimeColor();
  if (var == "TOD_COLOR")
    return config.getTodColor();
  if (var == "SECONDS_COLOR")
    return config.getSecondsColor();
  if (var == "DAY_OF_WEEK_COLOR")
    return config.getDayOfWeekColor();
  if (var == "DATE_COLOR")
    return config.getDateColor();
  if (var == "TEMP_COLOR")
    return config.getTempColor();
  if (var == "HUMIDITY_COLOR")
    return config.getHumidityColor();
  if (var == "WEATHER_TEMP_COLOR")
    return config.getWeatherTempColor();
  if (var == "WEATHER_FORECAST_COLOR")
    return config.getWeatherForecastColor();
  if (var == "SNOOZE_DURATION")
    return String(config.getSnoozeDuration());
  if (var == "DISMISS_DURATION")
    return String(config.getDismissDuration());
  if (var == "TEMP_CORRECTION_VALUE")
  {
    float offset = config.getTempCorrection();
    if (!config.isCelsius())
    {
      offset = offset * 9.0 / 5.0;
    }
    return String(offset, 1);
  }
  if (var == "TEMP_CORRECTION_UNIT")
    return config.isCelsius() ? "C" : "F";
  if (var == "TEMP_CORRECTION_ENABLED_CHECKED")
    return config.isTempCorrectionEnabled() ? "checked" : "";
  if (var == "AUTO_TEMP_CALIBRATION_CHECKED")
    return config.isAutoTempCalibration() ? "checked" : "";
  if (var == "LAST_AUTO_CAL_STATUS")
    return config.getLastAutoCalStatus();
  if (var == "TEMP_CORRECTION_CONTROLS_CLASS")
    return config.isTempCorrectionEnabled() ? "" : "d-none";
  if (var == "TEMP_COMPENSATION_FACTOR")
    return String(config.getTempCompensationFactor(), 2);

  if (var == "DEFAULT_PAGE_SELECTED_0")
    return config.getDefaultPage() == 0 ? "selected" : "";
  if (var == "DEFAULT_PAGE_SELECTED_1")
    return config.getDefaultPage() == 1 ? "selected" : "";
  if (var == "DEFAULT_PAGE_SELECTED_3")
    return config.getDefaultPage() == 3 ? "selected" : "";

  // Timezone selections
  String timezone = config.getTimezone();
  for (const auto &tz : timezones)
  {
    if (var == tz.placeholder)
    {
      return timezone == tz.posixString ? "selected" : "";
    }
  }
  return String();
}
