KennethDoerflein/ESP32Clock/src/ClockPage.cpp

/**
 * @file ClockPage.cpp
 * @brief Implements the ClockPage class for displaying the main clock face.
 *
 * This file contains the implementation of the ClockPage, which is responsible
 * for rendering the time, date, sensor data, and alarm indicators. It uses
 * sprites for efficient updates and to prevent flickering.
 */

// Comment out the next line to disable sprite borders for debugging
// #define DEBUG_BORDERS

#include "pages/ClockPage.h"
#include "Constants.h"
#include "Utils.h"
#include "ConfigManager.h"
#include "TimeManager.h"
#include "SensorModule.h"
#include "AlarmManager.h"
#include "fonts/DSEG7ModernBold104.h"
#include "fonts/DSEG14ModernBold32.h"
#include "fonts/DSEG14ModernBold48.h"
#include "fonts/DSEG7ModernBold48.h"
#include "fonts/CenturyGothicBold48.h"

#include <Arduino.h>

/**
 * @brief Constructs a new ClockPage.
 *
 * Initializes all the sprites used for rendering different parts of the clock face.
 * The TFT_eSPI driver instance is passed to each sprite's constructor.
 *
 * @param tft A pointer to the TFT_eSPI driver instance.
 */
ClockPage::ClockPage(TFT_eSPI *tft)
    : _sprClock(tft), _sprDayOfWeek(tft), _sprDate(tft), _sprTemp(tft), _sprHumidity(tft), _sprTOD(tft), _sprSeconds(tft),
      _sprNextAlarm1(tft), _sprNextAlarm2(tft), _tft(tft)
{
  // Sprites are initialized in the member initializer list
}

/**
 * @brief Destroys the ClockPage.
 *
 * The sprites, being stack-allocated objects with a reference to the TFT driver,
 * are automatically destructed. No manual memory management is needed.
 */
ClockPage::~ClockPage()
{
  // Sprites with TFT_eSPI driver reference are destructed automatically
}

/**
 * @brief Called when the page becomes the active view.
 *
 * This method sets up the display for the clock page. It creates the sprites
 * on the first entry, recalculates the layout, and clears the screen.
 * It also forces a full redraw of all elements by clearing the last known data.
 *
 * @param tft A reference to the TFT_eSPI driver instance.
 */
void ClockPage::onEnter(TFT_eSPI &tft)
{
  updateSpriteColors();
  tft.fillScreen(_bgColor);

  if (!_spritesCreated)
  {
    setupSprites(tft);
    _spritesCreated = true;
  }
  setupLayout(tft);

  // Force a redraw of all elements
  _lastData = {};
}

/**
 * @brief Called when the page is no longer the active view.
 *
 * This method is currently a no-op, as sprites are preserved between page
 * switches to improve performance.
 */
void ClockPage::onExit()
{
  // Sprites are not deleted on exit to preserve them.
}

/**
 * @brief Updates the internal state of the page.
 *
 * This method is currently a no-op, as all update logic is handled within
 * the `render` method for simplicity.
 */
void ClockPage::update()
{
  // The rendering logic handles this currently.
}

/**
 * @brief Renders the clock face to the display.
 *
 * This is the core rendering loop for the clock page. It fetches the current
 * display data and compares it to the last rendered data. If any data has
 * changed, it calls the appropriate draw function to update only the
 * necessary parts of the screen.
 *
 * @param tft A reference to the TFT_eSPI driver instance.
 */
void ClockPage::render(TFT_eSPI &tft)
{
  DisplayData currentData;
  updateDisplayData(currentData);

  // Render shared clock elements (seconds, time/tod, date, dayOfWeek)
  renderClockElements(tft, currentData, _lastData);

  // ClockPage-specific elements
  if (fabs(currentData.temp - _lastData.temp) > 0.1)
  {
    drawTemperature(tft);
    _lastData.temp = currentData.temp;
  }
  if (fabs(currentData.humidity - _lastData.humidity) > 0.1)
  {
    drawHumidity(tft);
    _lastData.humidity = currentData.humidity;
  }
  if (strcmp(currentData.nextAlarm1, _lastData.nextAlarm1) != 0 || strcmp(currentData.nextAlarm2, _lastData.nextAlarm2) != 0)
  {
    drawNextAlarms(tft, currentData.nextAlarm1, currentData.nextAlarm2);
    strncpy(_lastData.nextAlarm1, currentData.nextAlarm1, sizeof(_lastData.nextAlarm1));
    strncpy(_lastData.nextAlarm2, currentData.nextAlarm2, sizeof(_lastData.nextAlarm2));
  }
}

/**
 * @brief Calculates the positions of all sprites on the screen.
 *
 * This method computes the coordinates for each element of the clock face
 * based on the screen dimensions and predefined margins. It ensures that the
 * layout is responsive to different screen sizes and that elements are
 * centered and aligned correctly.
 *
 * @param tft A reference to the TFT_eSPI driver instance, used to get screen dimensions.
 */
void ClockPage::setupLayout(TFT_eSPI &tft)
{
  setupClockLayout(tft);

  int screenHeight = tft.height();

  // --- Bottom Rows Layout (Date and Sensors) ---
  tft.loadFont(DSEG14ModernBold32);
  int fontHeight = tft.fontHeight();
  tft.unloadFont(); // Unload to prevent bleeding into other pages
  _alarmRowY = screenHeight - (fontHeight * 3 + MARGIN + 80);
  _dateY = screenHeight - (fontHeight * 2 + MARGIN + 55);
  _sensorY = screenHeight - (fontHeight + MARGIN + 20);
}

void ClockPage::setupClockLayout(TFT_eSPI &tft)
{
  int screenWidth = tft.width();

  // --- Clock Block Layout ---
  _clockY = MARGIN;

  // Calculate the width of the side elements column (AM/PM and seconds)
  int sideWidth = max(_sprTOD.width(), _sprSeconds.width());
  int timeSideGap = 15; // Gap between HH:MM and the side elements

  // Calculate the total width of the entire clock display
  int totalWidth = CLOCK_SPRITE_WIDTH + timeSideGap + sideWidth;

  // Calculate the starting X position to center the clock display
  int startX = (screenWidth - totalWidth) / 2;
  if (startX < 0)
    startX = 0;

  // Set the position for the main clock sprite
  _clockX = startX - 15;

  // Calculate the starting X for the side elements
  _sideX = _clockX + CLOCK_SPRITE_WIDTH + timeSideGap;

  // Calculate the total height of the side elements stack
  int sideElementsVGap = 15;
  int sideElementsHeight = TOD_SPRITE_HEIGHT + sideElementsVGap + SECONDS_SPRITE_HEIGHT;

  // Calculate the starting Y to vertically center the side elements against the main clock
  int sideStartY = _clockY + (CLOCK_SPRITE_HEIGHT - sideElementsHeight) / 2;
  if (sideStartY < _clockY)
    sideStartY = _clockY;

  // Set positions for AM/PM and Seconds sprites
  _todX = _sideX + sideElementsVGap;
  _todY = sideStartY;
  _secondsX = _todX + (TOD_SPRITE_WIDTH - SECONDS_SPRITE_WIDTH) / 2;
  _secondsY = _todY + TOD_SPRITE_HEIGHT + sideElementsVGap + 3;
}

/**
 * @brief Creates and configures all the sprites for the clock face.
 *
 * This method is called once on the first entry to the page. It allocates
 * memory for each sprite, loads the required fonts, and sets default text
 * alignment and colors.
 *
 * @param tft A reference to the TFT_eSPI driver instance.
 */
void ClockPage::setupSprites(TFT_eSPI &tft)
{
  setupClockSprites(tft);
  setupSensorSprites(tft);
  updateSpriteColors();
}

void ClockPage::setupClockSprites(TFT_eSPI &tft)
{
  _sprClock.createSprite(CLOCK_SPRITE_WIDTH, CLOCK_SPRITE_HEIGHT);
  _sprClock.loadFont(DSEG7ModernBold104);
  _sprClock.setTextDatum(MR_DATUM);

  _sprTOD.createSprite(TOD_SPRITE_WIDTH, TOD_SPRITE_HEIGHT);
  _sprTOD.loadFont(DSEG14ModernBold32);
  _sprTOD.setTextDatum(TR_DATUM);

  _sprSeconds.createSprite(SECONDS_SPRITE_WIDTH, SECONDS_SPRITE_HEIGHT);
  _sprSeconds.loadFont(DSEG7ModernBold48);
  _sprSeconds.setTextDatum(TR_DATUM);

  _sprDayOfWeek.createSprite(tft.width() / 2 - MARGIN, DAY_OF_WEEK_SPRITE_HEIGHT);
  _sprDayOfWeek.loadFont(DSEG14ModernBold48);
  _sprDayOfWeek.setTextDatum(ML_DATUM);

  _sprDate.createSprite(tft.width() / 2 - MARGIN, DATE_SPRITE_HEIGHT);
  _sprDate.loadFont(DSEG14ModernBold48);
  _sprDate.setTextDatum(MR_DATUM);
}

void ClockPage::setupSensorSprites(TFT_eSPI &tft)
{
  _sprNextAlarm1.createSprite(tft.width() / 2 - MARGIN, DAY_OF_WEEK_SPRITE_HEIGHT); // Reusing height
  _sprNextAlarm1.loadFont(DSEG14ModernBold32);
  _sprNextAlarm1.setTextDatum(ML_DATUM);

  _sprNextAlarm2.createSprite(tft.width() / 2 - MARGIN, DAY_OF_WEEK_SPRITE_HEIGHT); // Reusing height
  _sprNextAlarm2.loadFont(DSEG14ModernBold32);
  _sprNextAlarm2.setTextDatum(MR_DATUM);

  _sprTemp.createSprite(tft.width() / 2 - MARGIN, TEMP_SPRITE_HEIGHT);
  _sprTemp.loadFont(DSEG14ModernBold48);
  _sprTemp.setTextDatum(ML_DATUM);

  _sprHumidity.createSprite(tft.width() / 2 - MARGIN, HUMIDITY_SPRITE_HEIGHT);
  _sprHumidity.loadFont(DSEG14ModernBold48);
  _sprHumidity.setTextDatum(MR_DATUM);
}

/**
 * @brief Updates the colors of all sprites from the configuration.
 *
 * This method reads the latest color settings from the ConfigManager, converts
 * them from hex strings to RGB565 format, and applies them to the text
 * color of each sprite.
 */
void ClockPage::updateSpriteColors()
{
  auto &config = ConfigManager::getInstance();
  _bgColor = hexToRGB565(config.getBackgroundColor());
  uint16_t timeColor = hexToRGB565(config.getTimeColor());
  uint16_t todColor = hexToRGB565(config.getTodColor());
  uint16_t secondsColor = hexToRGB565(config.getSecondsColor());
  uint16_t dayOfWeekColor = hexToRGB565(config.getDayOfWeekColor());
  uint16_t dateColor = hexToRGB565(config.getDateColor());
  uint16_t tempColor = hexToRGB565(config.getTempColor());
  uint16_t humidityColor = hexToRGB565(config.getHumidityColor());
  uint16_t alarmColor = hexToRGB565(config.getAlarmTextColor());

  _sprClock.setTextColor(timeColor, _bgColor);
  _sprTOD.setTextColor(todColor, _bgColor);
  _sprSeconds.setTextColor(secondsColor, _bgColor);
  _sprDayOfWeek.setTextColor(dayOfWeekColor, _bgColor);
  _sprDate.setTextColor(dateColor, _bgColor);
  _sprTemp.setTextColor(tempColor, _bgColor);
  _sprHumidity.setTextColor(humidityColor, _bgColor);
  _sprNextAlarm1.setTextColor(alarmColor, _bgColor);
  _sprNextAlarm2.setTextColor(alarmColor, _bgColor);
}

/**
 * @brief Draws the main clock time (HH:MM) and AM/PM indicator.
 *
 * This function renders the current time into the clock sprite and pushes it
 * to the screen. If not in 24-hour format, it also renders the AM/PM
 * indicator into its own sprite.
 *
 * @param tft A reference to the TFT_eSPI driver instance (not directly used,
 *            but required by the Page interface).
 */
void ClockPage::drawClock(TFT_eSPI &tft)
{
  auto &timeManager = TimeManager::getInstance();
  bool is24Hour = timeManager.is24HourFormat();
  char timeStr[8];
  char todStr[4];
  timeManager.getFormattedTime(timeStr, sizeof(timeStr), _renderSnapshot);
  timeManager.getTOD(todStr, sizeof(todStr), _renderSnapshot);

  _sprClock.fillSprite(_bgColor);
  _sprClock.drawString(timeStr, _sprClock.width(), _sprClock.height() / 2);
#ifdef DEBUG_BORDERS
  _sprClock.drawRect(0, 0, _sprClock.width(), _sprClock.height(), TFT_RED);
#endif
  _sprClock.pushSprite(_clockX, _clockY);

  if (!is24Hour)
  {
    _sprTOD.fillSprite(_bgColor);
    _sprTOD.drawString(todStr, _sprTOD.width(), 0);
#ifdef DEBUG_BORDERS
    _sprTOD.drawRect(0, 0, _sprTOD.width(), _sprTOD.height(), TFT_GREEN);
#endif
    _sprTOD.pushSprite(_todX, _todY);
  }
}

/**
 * @brief Draws the seconds display.
 * @param tft A reference to the TFT_eSPI driver instance.
 */
void ClockPage::drawSeconds(TFT_eSPI &tft)
{
  char secondsStr[4];
  TimeManager::getInstance().getFormattedSeconds(secondsStr, sizeof(secondsStr), _renderSnapshot);
  _sprSeconds.fillSprite(_bgColor);
  _sprSeconds.drawString(secondsStr, _sprSeconds.width(), 0);
#ifdef DEBUG_BORDERS
  _sprSeconds.drawRect(0, 0, _sprSeconds.width(), _sprSeconds.height(), TFT_MAGENTA);
#endif
  _sprSeconds.pushSprite(_secondsX, _secondsY);
}

/**
 * @brief Draws the day of the week display.
 * @param tft A reference to the TFT_eSPI driver instance.
 */
void ClockPage::drawDayOfWeek(TFT_eSPI &tft)
{
  char dayStr[4];
  TimeManager::getInstance().getDayOfWeek(dayStr, sizeof(dayStr), _renderSnapshot);
  _sprDayOfWeek.fillSprite(_bgColor);
  _sprDayOfWeek.drawString(dayStr, 0, _sprDayOfWeek.height() / 2);
#ifdef DEBUG_BORDERS
  _sprDayOfWeek.drawRect(0, 0, _sprDayOfWeek.width(), _sprDayOfWeek.height(), TFT_BLUE);
#endif
  _sprDayOfWeek.pushSprite(MARGIN, _dateY);
}

/**
 * @brief Draws the date display.
 * @param tft A reference to the TFT_eSPI driver instance.
 */
void ClockPage::drawDate(TFT_eSPI &tft)
{
  char dayStr[4];
  char dateStr[12];

  TimeManager::getInstance().getDayOfWeek(dayStr, sizeof(dayStr), _renderSnapshot);
  TimeManager::getInstance().getFormattedDate(dateStr, sizeof(dateStr), _renderSnapshot);
  _sprDate.fillSprite(_bgColor);
  _sprDate.drawString(dateStr, _sprDate.width(), _sprDate.height() / 2);
#ifdef DEBUG_BORDERS
  _sprDate.drawRect(0, 0, _sprDate.width(), _sprDate.height(), TFT_YELLOW);
#endif
  _sprDate.pushSprite(tft.width() / 2, _dateY);
}

void ClockPage::drawNextAlarms(TFT_eSPI &tft, const char *alarm1, const char *alarm2)
{
  _sprNextAlarm1.fillSprite(_bgColor);
  if (alarm1[0] != '\0')
  {
    _sprNextAlarm1.drawString(alarm1, 0, _sprNextAlarm1.height() / 2);
  }
  _sprNextAlarm1.pushSprite(MARGIN, _alarmRowY);

  _sprNextAlarm2.fillSprite(_bgColor);
  if (alarm2[0] != '\0')
  {
    _sprNextAlarm2.drawString(alarm2, _sprNextAlarm2.width(), _sprNextAlarm2.height() / 2);
  }
  _sprNextAlarm2.pushSprite(tft.width() / 2, _alarmRowY);
}

/**
 * @brief Draws the temperature display.
 *
 * This function renders the temperature value, a degree symbol, and the
 * temperature unit (C/F) into the temperature sprite.
 *
 * @param tft A reference to the TFT_eSPI driver instance.
 */
void ClockPage::drawTemperature(TFT_eSPI &tft)
{
  float temp = getTemperature();

  _sprTemp.fillSprite(_bgColor);
  _sprTemp.loadFont(DSEG14ModernBold48);

  char tempBuf[16];
  snprintf(tempBuf, sizeof(tempBuf), "%.0f", round(temp));
  _sprTemp.drawString(tempBuf, 0, _sprTemp.height() / 2);

  int tempWidth = _sprTemp.textWidth(tempBuf);
  int fontHeight = _sprTemp.fontHeight();
  int circleRadius = max(2, fontHeight / 14);
  int circleX = tempWidth + circleRadius + 2;
  int circleY = (_sprTemp.height() / 2) - (fontHeight / 2) + circleRadius;
  _sprTemp.fillCircle(circleX, circleY, circleRadius, _sprTemp.textcolor);

  _sprTemp.loadFont(DSEG14ModernBold32);
  _sprTemp.setTextDatum(TL_DATUM);
  char unit = ConfigManager::getInstance().isCelsius() ? 'C' : 'F';
  char unitBuf[2] = {unit, '\0'};
  int unitX = circleX + circleRadius + 2;
  int unitY = (_sprTemp.height() / 2) - (fontHeight / 2);
  _sprTemp.drawString(unitBuf, unitX, unitY);
  _sprTemp.setTextDatum(ML_DATUM);

#ifdef DEBUG_BORDERS
  _sprTemp.drawRect(0, 0, _sprTemp.width(), _sprTemp.height(), TFT_ORANGE);
#endif
  _sprTemp.pushSprite(MARGIN, _sensorY);
}

/**
 * @brief Draws the humidity display.
 *
 * Renders the humidity value and a percent symbol into the humidity sprite.
 *
 * @param tft A reference to the TFT_eSPI driver instance.
 */
void ClockPage::drawHumidity(TFT_eSPI &tft)
{
  float humidity = getHumidity();
  char buf[24];
  if (humidity < 0)
  {
    snprintf(buf, sizeof(buf), "N/A");
  }
  else
  {
    snprintf(buf, sizeof(buf), "%.0f%%", round(humidity));
  }

  _sprHumidity.fillSprite(_bgColor);
  _sprHumidity.drawString(buf, _sprHumidity.width(), _sprHumidity.height() / 2);

#ifdef DEBUG_BORDERS
  _sprHumidity.drawRect(0, 0, _sprHumidity.width(), _sprHumidity.height(), TFT_CYAN);
#endif
  _sprHumidity.pushSprite(tft.width() / 2, _sensorY);
}

/**
 * @brief Populates a DisplayData struct with the latest data.
 *
 * This helper function gathers all the necessary information from the
 * TimeManager and SensorModule and stores it in the provided struct.
 * This is used by the `render` method to check for changes.
 *
 * @param data A reference to the DisplayData struct to be filled.
 */
void ClockPage::updateDisplayData(DisplayData &data)
{
  _renderSnapshot = TimeManager::getInstance().getCachedTime();
  fillClockDisplayBase(data);
  data.temp = getTemperature();
  data.humidity = getHumidity();

  auto &timeManager = TimeManager::getInstance();
  std::vector<NextAlarmTime> alarms = timeManager.getNextAlarms(2);
  bool is24Hour = timeManager.is24HourFormat();

  if (alarms.size() > 0)
  {
    if (is24Hour)
    {
      snprintf(data.nextAlarm1, sizeof(data.nextAlarm1), "%02d:%02d", alarms[0].time.hour(), alarms[0].time.minute());
    }
    else
    {
      int hour12 = alarms[0].time.hour() % 12;
      if (hour12 == 0)
        hour12 = 12;
      const char *suffix = (alarms[0].time.hour() < 12) ? "AM" : "PM";
      snprintf(data.nextAlarm1, sizeof(data.nextAlarm1), "%d:%02d%s", hour12, alarms[0].time.minute(), suffix);
    }
  }
  else
  {
    data.nextAlarm1[0] = '\0';
  }

  if (alarms.size() > 1)
  {
    if (is24Hour)
    {
      snprintf(data.nextAlarm2, sizeof(data.nextAlarm2), "%02d:%02d", alarms[1].time.hour(), alarms[1].time.minute());
    }
    else
    {
      int hour12 = alarms[1].time.hour() % 12;
      if (hour12 == 0)
        hour12 = 12;
      const char *suffix = (alarms[1].time.hour() < 12) ? "AM" : "PM";
      snprintf(data.nextAlarm2, sizeof(data.nextAlarm2), "%d:%02d%s", hour12, alarms[1].time.minute(), suffix);
    }
  }
  else
  {
    data.nextAlarm2[0] = '\0';
  }
}

/**
 * @brief Refreshes the display after settings have changed.
 *
 * This method is called when the configuration has been updated. It reapplies
 * colors and optionally clears the entire screen. It also forces a full
 * redraw of all elements on the next render pass.
 *
 * @param tft A reference to the TFT_eSPI driver instance.
 * @param fullRefresh If true, the entire screen is cleared.
 */
void ClockPage::refresh(TFT_eSPI &tft, bool fullRefresh)
{
  auto &config = ConfigManager::getInstance();
  updateSpriteColors();

  if (fullRefresh)
  {
    tft.fillScreen(_bgColor);
  }

  if (config.is24HourFormat())
  {
    // In 24-hour mode, ensure the TOD sprite is cleared immediately on refresh.
    _sprTOD.fillSprite(_bgColor);
    _sprTOD.pushSprite(_todX, _todY);
  }

  // Force a redraw of all common clock elements
  resetClockFields(_lastData);

  // ClockPage-specific fields
  _lastData.temp = -999.0;
  _lastData.humidity = -999.0;
  strncpy(_lastData.nextAlarm1, " ", sizeof(_lastData.nextAlarm1));
  strncpy(_lastData.nextAlarm2, " ", sizeof(_lastData.nextAlarm2));
}

// --- Shared helpers for subclasses ---

void ClockPage::fillClockDisplayBase(ClockDisplayBase &base) const
{
  auto &timeManager = TimeManager::getInstance();
  timeManager.getFormattedTime(base.time, sizeof(base.time), _renderSnapshot);
  timeManager.getFormattedDate(base.date, sizeof(base.date), _renderSnapshot);
  timeManager.getDayOfWeek(base.dayOfWeek, sizeof(base.dayOfWeek), _renderSnapshot);
  timeManager.getTOD(base.tod, sizeof(base.tod), _renderSnapshot);
  timeManager.getFormattedSeconds(base.seconds, sizeof(base.seconds), _renderSnapshot);
}

void ClockPage::renderClockElements(TFT_eSPI &tft, const ClockDisplayBase &current, ClockDisplayBase &last)
{
  if (strcmp(current.seconds, last.seconds) != 0)
  {
    drawSeconds(tft);
    strncpy(last.seconds, current.seconds, sizeof(last.seconds));
  }
  if (strcmp(current.time, last.time) != 0 || strcmp(current.tod, last.tod) != 0)
  {
    drawClock(tft);
    strncpy(last.time, current.time, sizeof(last.time));
    strncpy(last.tod, current.tod, sizeof(last.tod));
  }
  if (strcmp(current.date, last.date) != 0)
  {
    drawDate(tft);
    strncpy(last.date, current.date, sizeof(last.date));
  }
  if (strcmp(current.dayOfWeek, last.dayOfWeek) != 0)
  {
    drawDayOfWeek(tft);
    strncpy(last.dayOfWeek, current.dayOfWeek, sizeof(last.dayOfWeek));
  }
}

void ClockPage::resetClockFields(ClockDisplayBase &base)
{
  strncpy(base.time, " ", sizeof(base.time));
  strncpy(base.date, " ", sizeof(base.date));
  strncpy(base.dayOfWeek, " ", sizeof(base.dayOfWeek));
  strncpy(base.tod, " ", sizeof(base.tod));
  strncpy(base.seconds, " ", sizeof(base.seconds));
}
