KennethDoerflein/ESP32Clock/include/TimeManager.h

// TimeManager.h

#pragma once

#include <Arduino.h>
#include <RTClib.h>
#include <vector>
#include <freertos/FreeRTOS.h>
#include <freertos/semphr.h>
#include "HardwareBus.h"

// Structure to hold an alarm's next occurrence time and its ID
struct NextAlarmTime
{
  DateTime time;
  uint8_t id;

  bool operator<(const NextAlarmTime &other) const
  {
    return time < other.time;
  }
};

/**
 * @class TimeManager
 * @brief Manages timekeeping, NTP synchronization, and time formatting.
 *
 * This singleton class handles all time-related functions for the clock,
 * including initializing the Real-Time Clock (RTC), syncing with an NTP server,
 * and providing formatted time and date strings for display.
 */
class TimeManager
{
public:
  /**
   * @brief Gets the singleton instance of the TimeManager.
   * @return A reference to the singleton TimeManager instance.
   */
  static TimeManager &getInstance()
  {
    static TimeManager instance;
    return instance;
  }

  /**
   * @brief Initializes the TimeManager.
   *
   * This should be called once during setup. It triggers the initial
   * NTP time synchronization.
   */
  void begin();

  /**
   * @brief Seeds the ESP32 system clock from the hardware RTC at boot.
   * Ensures time(nullptr) returns a valid wallclock time immediately,
   * even before NTP succeeds. Public because offline mode calls it
   * from main.cpp without going through begin().
   */
  void seedSystemClockFromRTC();

  /**
   * @brief Periodically realigns the ESP32 system clock to the hardware RTC.
   * @details Compares the system clock against the RTC every 60 seconds.
   *          If drift >= 2 seconds, corrects the system clock via settimeofday().
   *          Skipped when an NTP sync is in progress to avoid conflicts.
   */
  void syncSystemClockFromRTC();

  /**
   * @brief Updates the time manager's state.
   *
   * This method should be called repeatedly in the main loop. It handles
   * periodic tasks, such as the daily NTP sync check.
   * @return true if a time update occurred (typically once per second).
   */
  bool update();

  /**
   * @brief Checks all alarms to see if any snoozed alarms should be re-triggered.
   */
  void updateSnoozeStates();

  /**
   * @brief Forces a time synchronization with the NTP server.
   *
   * This function attempts to connect to an NTP server to update the RTC.
   * On success, it records the date of the sync.
   */
  void syncWithNTP();

  /**
   * @brief Drives the non-blocking NTP state machine.
   * @details This should be called in the main application loop to handle
   * ongoing asynchronous NTP synchronization attempts.
   * @return true if the time was updated during this call.
   */
  bool updateNtp();

  /**
   * @brief Gets the current time, formatted for display.
   * @return A String containing the formatted time (e.g., "10:30" or "22:30").
   */
  String getFormattedTime() const;

  /**
   * @brief Zero-allocation version: writes formatted time into caller buffer.
   * @param buf Output buffer (must be >= 6 bytes for "HH:MM" + null).
   * @param bufSize Size of the buffer.
   */
  void getFormattedTime(char *buf, size_t bufSize) const;
  void getFormattedTime(char *buf, size_t bufSize, const DateTime &now) const;

  /**
   * @brief Gets the current date, formatted for display.
   * @return A String containing the formatted date (e.g., "JAN 1").
   */
  String getFormattedDate() const;

  /**
   * @brief Zero-allocation version: writes formatted date into caller buffer.
   * @param buf Output buffer (must be >= 12 bytes).
   * @param bufSize Size of the buffer.
   */
  void getFormattedDate(char *buf, size_t bufSize) const;
  void getFormattedDate(char *buf, size_t bufSize, const DateTime &now) const;

  /**
   * @brief Gets the current day of the week.
   * @return A three-letter String for the day of the week (e.g., "MON").
   */
  String getDayOfWeek() const;

  /**
   * @brief Zero-allocation version: writes day abbreviation into caller buffer.
   * @param buf Output buffer (must be >= 4 bytes for "SUN" + null).
   * @param bufSize Size of the buffer.
   */
  void getDayOfWeek(char *buf, size_t bufSize) const;
  void getDayOfWeek(char *buf, size_t bufSize, const DateTime &now) const;

  /**
   * @brief Gets the time of day period (AM/PM).
   * @return "AM", "PM", or an empty string if in 24-hour format.
   */
  String getTOD() const;

  /**
   * @brief Zero-allocation version: writes AM/PM into caller buffer.
   * @param buf Output buffer (must be >= 3 bytes for "PM" + null).
   * @param bufSize Size of the buffer.
   */
  void getTOD(char *buf, size_t bufSize) const;
  void getTOD(char *buf, size_t bufSize, const DateTime &now) const;

  /**
   * @brief Gets the seconds of the current time, formatted for display.
   * @return A String containing the formatted seconds (e.g., "59").
   */
  String getFormattedSeconds() const;

  /**
   * @brief Zero-allocation version: writes formatted seconds into caller buffer.
   * @param buf Output buffer (must be >= 3 bytes for "59" + null).
   * @param bufSize Size of the buffer.
   */
  void getFormattedSeconds(char *buf, size_t bufSize) const;
  void getFormattedSeconds(char *buf, size_t bufSize, const DateTime &now) const;

  // Pure formatting helpers suitable for zero-dependency testing and display formatting
  static void formatTime(char *buf, size_t bufSize, const DateTime &now, bool is24Hour)
  {
    if (is24Hour)
    {
      snprintf(buf, bufSize, "%02d:%02d", now.hour(), now.minute());
    }
    else
    {
      int hour12 = now.hour() % 12;
      if (hour12 == 0)
        hour12 = 12;
      snprintf(buf, bufSize, "%d:%02d", hour12, now.minute());
    }
  }

  static void formatDate(char *buf, size_t bufSize, const DateTime &now)
  {
    static const char *monthNames[] = {
        "JAN", "FEB", "MAR", "APR", "MAY", "JUN",
        "JUL", "AUG", "SEP", "OCT", "NOV", "DEC"};
    if (now.month() >= 1 && now.month() <= 12)
    {
      snprintf(buf, bufSize, "%s %d", monthNames[now.month() - 1], now.day());
    }
    else
    {
      snprintf(buf, bufSize, "UNK %d", now.day());
    }
  }

  static void formatDayOfWeek(char *buf, size_t bufSize, const DateTime &now)
  {
    static const char *dayNames[] = {
        "SUN", "MON", "TUE", "WED",
        "THU", "FRI", "SAT"};
    if (now.dayOfTheWeek() <= 6)
    {
      snprintf(buf, bufSize, "%s", dayNames[now.dayOfTheWeek()]);
    }
    else
    {
      snprintf(buf, bufSize, "UNK");
    }
  }

  static void formatTOD(char *buf, size_t bufSize, const DateTime &now, bool is24Hour)
  {
    if (is24Hour)
    {
      if (bufSize > 0)
        buf[0] = '\0';
      return;
    }
    snprintf(buf, bufSize, "%s", (now.hour() < 12) ? "AM" : "PM");
  }

  static void formatSeconds(char *buf, size_t bufSize, const DateTime &now)
  {
    snprintf(buf, bufSize, "%02d", now.second());
  }

  /**
   * @brief Gets the cached time snapshot from the last update() call.
   * @details This returns the time that was captured when the second changed,
   *          ensuring consistent time data for rendering within the same frame.
   *          Use this for display purposes to avoid timing inconsistencies.
   * @return A DateTime object representing the cached time.
   */
  DateTime getCachedTime() const;

  /**
   * @brief Gets the current hour in 24-hour format.
   * @return The current hour (0-23).
   */
  uint8_t getHour() const;

  /**
   * @brief Checks if the time should be displayed in 24-hour format.
   * @return True if 24-hour format is active, false otherwise.
   */
  bool is24HourFormat() const;

  /**
   * @brief Gets the current time from the RTC (UTC).
   * @return A DateTime object representing the current UTC time.
   */
  DateTime getRTCTime() const;

  /**
   * @brief Sets the hardware RTC to a new time, protected by the I2C mutex.
   * @details This must be used instead of bare RTC.adjust() calls to prevent
   *          I2C bus corruption from concurrent access across cores.
   * @param newTime The new UTC time to set on the RTC.
   */
  void adjustRTC(const DateTime &newTime);

  /**
   * @brief Returns the internal state mutex for TimeManager state protection.
   * @return The recursive mutex handle guarding internal TimeManager state.
   */
  SemaphoreHandle_t getStateMutex() const { return _mutex; }

  /**
   * @brief Gets the current UTC time converted to local time.
   * @details Uses the system timezone to convert UTC time. If preReadUtc is provided,
   *          avoids redundant I2C bus queries.
   * @param preReadUtc Optional pointer to an already-read UTC DateTime.
   * @return A DateTime object representing the current local time.
   */
  DateTime getLocalTime(const DateTime *preReadUtc = nullptr) const;

  /**
   * @brief Checks if the RTC has been set to a valid time.
   * @return True if the time is valid (year > 2000), false otherwise.
   */
  bool isTimeSet() const;

  /**
   * @brief Checks if a daily NTP sync is needed and performs it.
   *
   * This is typically run at a specific time of day (e.g., 3 AM) to ensure
   * the clock remains accurate.
   */
  void checkDailySync();

  /**
   * @brief Periodically checks RTC drift against NTP and resyncs if needed.
   *
   * This function is designed to be called in the main loop. It checks the
   * time drift at a defined interval (e.g., every 4 hours) and triggers a
   * non-blocking NTP sync if the drift exceeds a specified threshold.
   */
  void checkDriftAndResync();

  /**
   * @brief Checks for DST transitions, updates ConfigManager, handles missed alarms, and reschedules alarms.
   * @param preReadUtc Optional pointer to an already-read UTC DateTime to avoid redundant I2C reads.
   */
  void checkDST(const DateTime *preReadUtc = nullptr);

  /**
   * @brief Processes the alarm event outside of the ISR.
   */
  void handleAlarm();

  /**
   * @brief Sets the RTC's hardware alarms for the next two upcoming alarms.
   */
  void setNextAlarms();

  /**
   * @brief Checks for any alarms that were missed while the device was off.
   * @note This is intended to be called once at boot.
   */
  void checkMissedAlarms();

  /**
   * @brief Checks for missed alarms within a specific time window.
   */
  void checkMissedAlarmsWindow(time_t startEpoch, time_t endEpoch);

  /**
   * @brief Dismisses an alarm (disables if one-time, updates dismiss day if recurring).
   */
  void dismissAlarm(uint8_t alarmId);

  /**
   * @brief Gets the next upcoming alarms.
   * @param count The number of upcoming alarms to retrieve.
   * @return A vector of NextAlarmTime structures.
   */
  std::vector<NextAlarmTime> getNextAlarms(int count) const;

  /**
   * @brief Re-calculates and caches the next upcoming alarms.
   * @param now The current time, used to avoid re-reading from RTC if available.
   */
  void updateNextAlarmsCache(const DateTime &now);

  /**
   * @brief Overload that fetches the current time from RTC.
   */
  void updateNextAlarmsCache();

private:
  /**
   * @brief Private constructor to enforce the singleton pattern.
   */
  TimeManager();

  /// @brief Stores the date of the last successful NTP sync in YYYYMMDD format. 0 = never synced.
  uint32_t lastSyncDate = 0;

  /// @brief Timestamp of the last update call to manage update intervals.
  unsigned long lastUpdate = 0;

  /// @brief The interval at which the `update` method runs its checks, in milliseconds.
  static constexpr unsigned long UPDATE_INTERVAL = 250; // 250 milliseconds

  uint8_t _lastDecodedSecond = 61;

  /// @brief Cached time snapshot from the last successful second transition (local time).
  /// This ensures consistent time data between update detection and rendering.
  DateTime _cachedTime;

  /// @brief Timestamp of the last drift check.
  unsigned long lastDriftCheck = 0;

  /// @brief Whether the first post-boot drift check has been completed.
  /// The first check uses a shorter interval (5 min) to catch post-crash drift quickly.
  bool _initialDriftCheckDone = false;

  /// @brief Timestamp of the last system clock realignment from the RTC.
  unsigned long _lastSystemClockSync = 0;
  /// @brief How often to realign the system clock to the RTC (milliseconds).
  static const unsigned long SYSTEM_CLOCK_SYNC_INTERVAL = 60000; // 60 seconds

  /// @brief Last known-good RTC reading for monotonicity validation.
  /// Used by getRTCTime() to reject corrupted I2C reads that jump backward.
  mutable DateTime _lastValidRtcTime;

  bool _rtc_alarms_initialized = false;
  int8_t _rtcAlarm1Id = -1; ///< The ID of the alarm associated with RTC alarm 1.
  int8_t _rtcAlarm2Id = -1; ///< The ID of the alarm associated with RTC alarm 2.

  std::vector<NextAlarmTime> _cachedNextAlarms;
  uint8_t _lastCacheUpdateMinute = 255;

  mutable SemaphoreHandle_t _mutex;

  /**
   * @brief Clears both hardware alarms on the RTC.
   */
  void clearRtcAlarms();

  /**
   * @brief Converts a local DateTime to UTC based on system timezone.
   * @param local The local DateTime to convert.
   * @return A DateTime object representing UTC time.
   */
  DateTime localToUtc(const DateTime &local) const;
};
