KennethDoerflein/ESP32Clock/src/WiFiManager.cpp

/**
 * @file WiFiManager.cpp
 * @brief Implements the WiFiManager class for handling WiFi connectivity.
 *
 * This file contains the implementation for managing WiFi connections, including
 * connecting to a saved network, handling disconnections and reconnections,
 * running a captive portal for initial setup, and managing connection tests.
 */
#include "WiFiManager.h"
#include <WiFi.h>
#include <DNSServer.h>
#include "ConfigManager.h"
#include "Display.h"
#include "ClockWebServer.h"
#include <ArduinoJson.h>
#include "SerialLog.h"
#include "LockGuard.h"
#include "UpdateManager.h"

// --- Static Member Initialization ---
const char *WiFiManager::AP_SSID = "Clock-Setup";
volatile bool WiFiManager::_connectionResult = false;

/**
 * @brief Static event handler for WiFi events.
 *
 * This function is registered with the ESP-IDF WiFi system to receive
 * notifications about connection status changes. It contains a state machine
 * to handle both normal connection events and the specific sequence of events
 * that occur during a non-blocking connection test.
 *
 * @param event The WiFi event that occurred.
 * @param info Additional information about the event.
 */
void WiFiManager::wifiEventHandler(WiFiEvent_t event, WiFiEventInfo_t info)
{
  auto &logger = SerialLog::getInstance();
  auto &instance = getInstance();

  // Protect shared state access in ISR context (technically task context in ESP32)
  LockGuard lock(instance._mutex);

  // --- Handle Connection Test Events ---
  if (instance._testStatus == TEST_IN_PROGRESS)
  {
    if (event == ARDUINO_EVENT_WIFI_STA_DISCONNECTED)
    {
      // Check if this is the intentional disconnect from the start of the test.
      if (instance._ignoreDisconnectEvent)
      {
        // If it is, consume the flag and do nothing.
        // We now wait for either a successful connection or a real failure.
        instance._ignoreDisconnectEvent = false;
      }
      else
      {
        // If the flag is already false, this is a genuine failure.
        logger.print("\nConnection test failed.\n");
        instance._testStatus = TEST_FAILED;
        if (instance.isCaptivePortal())
        {
          WiFi.mode(WIFI_AP);
        }
      }
    }
    else if (event == ARDUINO_EVENT_WIFI_STA_GOT_IP)
    {
      logger.print("\nConnection test successful!\n");
      instance._testStatus = TEST_SUCCESS;
      instance._ignoreDisconnectEvent = false; // Reset flag on success, just in case.

      if (instance._saveOnSuccess)
      {
        // Do NOT call config.save() here — the WiFi event callback runs in the
        // WiFi stack task context; NVS writes from there can corrupt flash.
        // Set a flag and flush it in handleConnection() (main loop context).
        instance._pendingCredentialSave = true;
      }
    }
    return; // Do not fall through to standard handling during a test.
  }

  // --- Standard Event Handling (for when not testing) ---
  if (event == ARDUINO_EVENT_WIFI_STA_GOT_IP)
  {
    logger.print("\nWiFi connected! Got IP.\n");
    logger.printf("IP Address: %s\n", WiFi.localIP().toString().c_str());
    // Set the flag to indicate a successful connection.
    _connectionResult = true;

    // If this is the first successful connection with these credentials,
    // mark them as valid. Do NOT call config.save() here — the WiFi event
    // callback runs in the WiFi stack task context; NVS writes from here
    // can corrupt flash. Defer the save to handleConnection() (Core 0).
    auto &config = ConfigManager::getInstance();
    if (!config.areWifiCredsValid())
    {
      logger.print("WiFi credentials validated. Deferring save.\n");
      config.setWifiCredsValid(true);
      instance._pendingCredsValidSave = true;
    }

    // Since we have an IP, it's time to start mDNS.
    // Defer to handleConnection() to avoid blocking the LwIP event task.
    if (WiFi.isConnected())
    {
      WiFi.mode(WIFI_STA);
      logger.print("Switched to STA mode. AP is now off.\n");
      instance._pendingMdnsSetup = true;
    }
  }
  else if (event == ARDUINO_EVENT_WIFI_STA_DISCONNECTED)
  {
    logger.print("WiFi lost connection.\n");
    _connectionResult = false;
    // Set _isConnected to false directly, but don't trigger reconnection here.
    instance._isConnected = false;
  }
}

/**
 * @brief Manages the WiFi connection state, handling automatic reconnections.
 *
 * This should be called in the main loop. If the WiFi connection is lost,
 * this function will attempt to reconnect at progressively longer intervals
 * to avoid spamming connection requests.
 */
void WiFiManager::handleConnection()
{
  if (UpdateManager::getInstance().isUpdateInProgress())
  {
    return;
  }

  // Flush credential save deferred from the event handler (safe to write NVS here)
  bool doCredentialSave = false;
  String localTestSsid;
  String localTestPassword;
  {
    LockGuard lock(_mutex);
    if (_pendingCredentialSave) {
      _pendingCredentialSave = false;
      doCredentialSave = true;
      localTestSsid = _testSsid;
      localTestPassword = _testPassword;
    }
  }
  if (doCredentialSave) {
    auto &config = ConfigManager::getInstance();
    config.setWifiSSID(localTestSsid);
    config.setWifiPassword(localTestPassword);
    config.save();
    LockGuard lock(_mutex);
    _pendingReboot = true;
  }

  // Flush the "creds valid" flag save deferred from the standard event handler
  bool doCredsValidSave = false;
  bool doMdnsSetup = false;
  {
    LockGuard lock(_mutex);
    if (_pendingCredsValidSave) {
      _pendingCredsValidSave = false;
      doCredsValidSave = true;
    }
    if (_pendingMdnsSetup) {
      _pendingMdnsSetup = false;
      doMdnsSetup = true;
    }
  }
  if (doCredsValidSave) {
    ConfigManager::getInstance().save();
    SerialLog::getInstance().print("WiFi credentials valid flag saved.\n");
  }
  if (doMdnsSetup) {
    ClockWebServer::getInstance().setupMDNS();
  }

  if (isCaptivePortal())
  {
    return;
  }

  // First, ensure our internal state `_isConnected` matches the actual WiFi status.
  // This is a robust way to handle missed events or state inconsistencies.
  // A true connection requires both a connected status and a valid IP address.
  bool isReallyConnected = (WiFi.status() == WL_CONNECTED && WiFi.localIP() != IPAddress(0, 0, 0, 0));

  {
    LockGuard lock(_mutex);
    if (isReallyConnected != _isConnected)
    {
      _isConnected = isReallyConnected;
      if (_isConnected)
      {
        SerialLog::getInstance().print("WiFi connection state corrected to CONNECTED by polling.\n");
      }
      else
      {
        SerialLog::getInstance().print("WiFi connection state corrected to DISCONNECTED by polling.\n");
      }
    }

    if (_isConnected)
    {
      if (_isReconnecting)
      {
        _isReconnecting = false;
      }
      return;
    }
  } // Release lock before potentially blocking operations

  if (ConfigManager::getInstance().getWifiSSID().length() == 0)
  {
    return;
  }

  unsigned long now = millis();

  // Check reconnection state with lock
  bool shouldReconnect = false;
  {
    LockGuard lock(_mutex);
    if (_isReconnecting)
    {
      if (now - _lastReconnectAttempt > 15000) // 15s timeout
      {
        SerialLog::getInstance().print("WiFi reconnection timed out.\n");
        _isReconnecting = false;
      }
      return;
    }

    if (now - _lastReconnectAttempt > 30000) // 30s interval
    {
      _lastReconnectAttempt = now;
      _isReconnecting = true;
      shouldReconnect = true;
    }
  }

  if (shouldReconnect)
  {
    SerialLog::getInstance().print("Attempting to reconnect WiFi...\n");
    WiFi.reconnect();
  }
}

/**
 * @brief Gets the singleton instance of the WiFiManager.
 * @return A reference to the singleton instance.
 */
WiFiManager &WiFiManager::getInstance()
{
  static WiFiManager instance;
  return instance;
}

/**
 * @brief Private constructor for the WiFiManager.
 * Initializes internal state variables.
 */
WiFiManager::WiFiManager() : _isConnected(false), _dnsServer(nullptr), _pendingReboot(false)
{
  _mutex = xSemaphoreCreateMutex();
}

/**
 * @brief Initializes the WiFi module.
 *
 * Sets a unique hostname, then attempts to connect to the WiFi network using
 * credentials stored in the ConfigManager. If the SSID is not configured or
 * the connection fails, it launches a captive portal for configuration.
 * It also provides visual feedback on the display during this process.
 *
 * @return True if the captive portal was started, false otherwise.
 */
bool WiFiManager::begin()
{
  _hostname = ConfigManager::getInstance().getHostname();

  if (_hostname.length() == 0)
  {
    uint8_t mac[6];
    WiFi.macAddress(mac);
    char hostname_cstr[18]; // "ESP32Clock-" + 6 hex chars + null terminator
    sprintf(hostname_cstr, "ESP32Clock-%02X%02X%02X", mac[3], mac[4], mac[5]);
    _hostname = hostname_cstr;
  }

  WiFi.setHostname(_hostname.c_str());
  SerialLog::getInstance().printf("Hostname set to: %s\n", _hostname.c_str());

  // Register the event handler
  WiFi.onEvent(wifiEventHandler);
  WiFi.setSleep(false);

  // --- WiFi Connection Logic ---
  String ssid = ConfigManager::getInstance().getWifiSSID();
  String password = ConfigManager::getInstance().getWifiPassword();
  auto &display = Display::getInstance();
  auto &logger = SerialLog::getInstance();

  if (ssid.length() > 0)
  {
    logger.printf("WiFiManager: Attempting to connect to SSID: %s\n", ssid.c_str());
    display.drawStatusMessage("Connecting to WiFi...");
    _connectionResult = false; // Reset the flag
    WiFi.begin(ssid.c_str(), password.c_str());

    unsigned long startTime = millis();
    while (!_connectionResult && millis() - startTime < 15000)
    { // 15-second timeout
      delay(100);
      logger.print(".");
    }

    if (_connectionResult)
    {
      logger.print("\nWiFiManager: Connection successful.\n");
      LockGuard lock(_mutex);
      _isConnected = true;
      display.drawStatusMessage(("IP: " + WiFi.localIP().toString()).c_str());
      delay(2000);
    }
    else
    {
      logger.print("\nWiFiManager: Connection failed after 15 seconds.\n");
    }
  }
  else
  {
    logger.print("WiFiManager: No SSID configured.\n");
  }

  bool currentlyConnected;
  {
    LockGuard lock(_mutex);
    currentlyConnected = _isConnected;
  }

  if (!currentlyConnected)
  {
    // Disconnect and stop the station to prevent it from retrying
    // with bad credentials in the background, which causes log spam.
    WiFi.disconnect(true);

    // Only start captive portal if credentials have not been validated before.
    if (!ConfigManager::getInstance().areWifiCredsValid())
    {
      logger.print("WiFi credentials are not validated. Starting Captive Portal.\n");
      startCaptivePortal();
      return true; // Captive portal was started
    }
    else
    {
      logger.print("WiFi connection failed, but credentials are valid. Skipping captive portal.\n");
    }
  }

  return false; // WiFi connected successfully, or skipping captive portal for background retry.
}

/**
 * @brief Handles DNS requests when the captive portal is active.
 * This should be called repeatedly in the main loop.
 */
void WiFiManager::handleDns()
{
  if (_dnsServer)
  {
    _dnsServer->processNextRequest();
  }
}

/**
 * @brief Returns the current WiFi connection status.
 * @return True if the device is connected to WiFi, false otherwise.
 */
bool WiFiManager::isConnected() const
{
  LockGuard lock(_mutex);
  return _isConnected;
}

/**
 * @brief Checks if the captive portal is currently active.
 * @return True if the captive portal is running, false otherwise.
 */
bool WiFiManager::isCaptivePortal() const
{
  return _dnsServer != nullptr;
}

/**
 * @brief Starts a non-blocking WiFi scan.
 */
void WiFiManager::startScan()
{
  // Clear previous scan results before starting a new one.
  WiFi.scanDelete();
  // Start a non-blocking scan.
  // The results will be retrieved asynchronously by getScanResults().
  WiFi.scanNetworks(true);
}

/**
 * @brief Gets the results of a WiFi scan.
 *
 * This function is non-blocking. It checks the status of the scan and returns
 * a JSON string indicating whether the scan is "idle", "scanning", or
 * contains the results of a completed scan.
 *
 * @return A JSON formatted string with the scan status or results.
 */
String WiFiManager::getScanResults()
{
  int16_t scanResult = WiFi.scanComplete();

  if (scanResult == WIFI_SCAN_FAILED)
  {
    // Scan failed, but we don't start a new one here.
    // We just report that the scan is not running.
    return "{\"status\":\"idle\"}";
  }
  else if (scanResult == WIFI_SCAN_RUNNING)
  {
    // Scan is in progress
    return "{\"status\":\"scanning\"}";
  }
  else
  {
    // Scan is complete, and we have results
    JsonDocument doc;
    JsonArray networks = doc.to<JsonArray>();

    for (int i = 0; i < scanResult; ++i)
    {
      JsonObject network = networks.add<JsonObject>();
      network["ssid"] = WiFi.SSID(i);
      network["rssi"] = WiFi.RSSI(i);
      network["channel"] = WiFi.channel(i);
      // Use a string for encryption type for easier parsing on the frontend
      switch (WiFi.encryptionType(i))
      {
      case WIFI_AUTH_OPEN:
        network["encryption"] = "OPEN";
        break;
      case WIFI_AUTH_WEP:
        network["encryption"] = "WEP";
        break;
      case WIFI_AUTH_WPA_PSK:
        network["encryption"] = "WPA_PSK";
        break;
      case WIFI_AUTH_WPA2_PSK:
        network["encryption"] = "WPA2_PSK";
        break;
      case WIFI_AUTH_WPA_WPA2_PSK:
        network["encryption"] = "WPA_WPA2_PSK";
        break;
      case WIFI_AUTH_WPA2_ENTERPRISE:
        network["encryption"] = "WPA2_ENTERPRISE";
        break;
      case WIFI_AUTH_WPA3_PSK:
        network["encryption"] = "WPA3_PSK";
        break;
      case WIFI_AUTH_WPA2_WPA3_PSK:
        network["encryption"] = "WPA2_WPA3_PSK";
        break;
      default:
        network["encryption"] = "UNKNOWN";
        break;
      }
    }

    String jsonOutput;
    serializeJson(doc, jsonOutput);
    return jsonOutput;
  }
}

/**
 * @brief Starts the Access Point and DNS server for the captive portal.
 */
void WiFiManager::startCaptivePortal()
{
  auto &display = Display::getInstance();
  auto &logger = SerialLog::getInstance();
  logger.print("\nStarting Captive Portal.\n");

  // Set mode to AP + Station
  WiFi.mode(WIFI_AP_STA);

  // Start AP
  WiFi.softAP(AP_SSID);
  IPAddress apIP = WiFi.softAPIP();
  logger.printf("AP IP address: %s\n", apIP.toString().c_str());

  // Start DNS Server
  _dnsServer.reset(new DNSServer());
  const byte DNS_PORT = 53;

  _dnsServer->setErrorReplyCode(DNSReplyCode::NoError);
  _dnsServer->start(DNS_PORT, "*", apIP);

  // Show a message on the display while scanning
  logger.print("Starting background WiFi scan...\n");
  display.drawMultiLineStatusMessage("Please wait...", "Scanning for networks");
  WiFi.scanDelete();       // Clear previous scan results
  WiFi.scanNetworks(true); // true = async (non-blocking)
  delay(5000);
}

/**
 * @brief Gets the configured hostname of the device.
 * @return The hostname as a String.
 */
String WiFiManager::getHostname() const
{
  return _hostname;
}

/**
 * @brief Sets the hostname of the device.
 * @param hostname The new hostname to set.
 */
void WiFiManager::setHostname(const String &hostname)
{
  _hostname = hostname;
  ConfigManager::getInstance().setHostname(hostname);
  ConfigManager::getInstance().save();
  // Update mDNS
  if (WiFi.isConnected())
  {
    LockGuard lock(_mutex);
    _pendingMdnsSetup = true;
  }
}

/**
 * @brief Starts a non-blocking test of WiFi credentials.
 * @param ssid The SSID to test.
 * @param password The password to test.
 * @param saveOnSuccess If true, the credentials will be saved upon a successful connection.
 */
void WiFiManager::startConnectionTest(const String &ssid, const String &password, bool saveOnSuccess)
{
  {
    LockGuard lock(_mutex);
    if (_pendingReboot)
    {
      SerialLog::getInstance().print("Ignoring new connection test, reboot is pending.\n");
      return;
    }

    auto &logger = SerialLog::getInstance();
    logger.printf("Starting connection test for SSID: %s\n", ssid.c_str());

    _testSsid = ssid;
    _testPassword = password;
    _saveOnSuccess = saveOnSuccess;
    _testStatus = TEST_IN_PROGRESS;

    // Set a flag to tell the event handler to ignore the next disconnect event,
    // which we are about to cause intentionally.
    _ignoreDisconnectEvent = true;
  }

  WiFi.disconnect(true);
  delay(100);

  if (isCaptivePortal())
  {
    WiFi.mode(WIFI_AP_STA);
  }

  WiFi.begin(ssid.c_str(), password.c_str());
}

/**
 * @brief Saves new WiFi credentials and reboots the device.
 * @param ssid The SSID to save.
 * @param password The password to save.
 */
void WiFiManager::saveCredentialsAndReboot(const String &ssid, const String &password)
{
  auto &config = ConfigManager::getInstance();
  config.setWifiSSID(ssid);
  config.setWifiPassword(password);
  config.save();

  // A reboot is the most reliable way to apply new WiFi credentials
  SerialLog::getInstance().clearCrashLogMagic();
  ESP.restart();
}

/**
 * @brief Gets the current status of the connection test.
 * @return The current ConnectionTestStatus.
 */
WiFiManager::ConnectionTestStatus WiFiManager::getConnectionTestStatus() const
{
  LockGuard lock(_mutex);
  return _testStatus;
}

/**
 * @brief Checks if a reboot is pending after a successful WiFi test.
 * @return True if a reboot is pending, false otherwise.
 */
bool WiFiManager::isPendingReboot() const
{
  LockGuard lock(_mutex);
  return _pendingReboot;
}

/**
 * @brief Resets the connection test status back to idle.
 */
void WiFiManager::resetConnectionTestStatus()
{
  LockGuard lock(_mutex);
  _testStatus = TEST_IDLE;
  _pendingReboot = false;
}
