KennethDoerflein/ESP32Clock/src/Display.cpp

/**
 * @file Display.cpp
 * @brief Implements the Display class for low-level screen and backlight control.
 *
 * This file contains the implementation for initializing the TFT display,
 * managing the backlight brightness using PWM, and drawing simple status
 * messages to the screen.
 */

#include "Display.h"
#include "ConfigManager.h"
#include "TimeManager.h"
#include "Constants.h"
#include "fonts/CenturyGothic28.h"
#include <Arduino.h>

// LEDC (LED Control) constants for managing the backlight PWM.
#define TFT_BL 6               // Manually define the backlight pin here
#define BACKLIGHT_CHANNEL 0    // LEDC channel 0
#define BACKLIGHT_FREQ 5000    // 5 kHz frequency
#define BACKLIGHT_RESOLUTION 8 // 8-bit resolution (0-255)

/**
 * @brief Initializes the display and backlight.
 *
 * This function sets up the LEDC peripheral for PWM control of the backlight,
 * attaches the backlight pin, and initializes the TFT display driver.
 * It also sets a default full brightness and clears the screen.
 */
void Display::begin()
{
  // Create the mutex before any TFT operations begin.
  tft_mutex = xSemaphoreCreateMutex();

  // Configure the LEDC peripheral for PWM control of the backlight.
  ledcSetup(BACKLIGHT_CHANNEL, BACKLIGHT_FREQ, BACKLIGHT_RESOLUTION);
  ledcAttachPin(TFT_BL, BACKLIGHT_CHANNEL);

  // Set a default brightness so the screen is on during boot.
  ledcWrite(BACKLIGHT_CHANNEL, 255);

  // Initialize the TFT display driver.
  if (xSemaphoreTake(tft_mutex, portMAX_DELAY))
  {
    tft.init();
    tft.fillScreen(TFT_BLACK);
    _updateRotation();
    _updateInversion();
    xSemaphoreGive(tft_mutex);
  }
}

/**
 * @brief Private implementation for updating screen rotation.
 *
 * This function contains the hardware-specific call to set the rotation.
 * It is designed to be called only when the `tft_mutex` is already held,
 * preventing nested locks and potential deadlocks.
 */
void Display::_updateRotation()
{
  tft.setRotation(ConfigManager::getInstance().isScreenFlipped() ? 1 : 3);
}

/**
 * @brief Private implementation for updating screen color inversion.
 *
 * This function contains the hardware-specific call to invert the display.
 * It is designed to be called only when the `tft_mutex` is already held,
 * preventing nested locks and potential deadlocks.
 */
void Display::_updateInversion()
{
  tft.invertDisplay(ConfigManager::getInstance().isInvertColors());
}

/**
 * @brief Updates the screen's rotation based on the current configuration.
 *
 * Reads the `screenFlipped` setting from the ConfigManager and sets the
 * TFT rotation accordingly.
 */
void Display::updateRotation()
{
  if (xSemaphoreTake(tft_mutex, portMAX_DELAY))
  {
    _updateRotation();
    xSemaphoreGive(tft_mutex);
  }
}

/**
 * @brief Updates the screen's color inversion based on the current configuration.
 *
 * Reads the `invertColors` setting from the ConfigManager and sets the
 * TFT inversion accordingly.
 */
void Display::updateInversion()
{
  if (xSemaphoreTake(tft_mutex, portMAX_DELAY))
  {
    _updateInversion();
    xSemaphoreGive(tft_mutex);
  }
}

/**
 * @brief Displays a single-line status message centered on the screen.
 * @param message The message to display.
 */
void Display::drawStatusMessage(const char *message)
{
  if (xSemaphoreTake(tft_mutex, portMAX_DELAY))
  {
    tft.fillScreen(TFT_BLACK);
    tft.setTextColor(TFT_WHITE, TFT_BLACK);
    tft.setTextDatum(MC_DATUM);
    tft.loadFont(CenturyGothic28);
    tft.drawString(message, tft.width() / 2, tft.height() / 2);
    tft.unloadFont(); // Unload font to free up memory
    xSemaphoreGive(tft_mutex);
  }
}

/**
 * @brief Displays a two-line status message centered on the screen.
 * @param line1 The first line of the message.
 * @param line2 The second line of the message.
 */
void Display::drawMultiLineStatusMessage(const char *line1, const char *line2)
{
  if (xSemaphoreTake(tft_mutex, portMAX_DELAY))
  {
    tft.fillScreen(TFT_BLACK);
    tft.setTextColor(TFT_WHITE, TFT_BLACK);
    tft.setTextDatum(MC_DATUM);
    tft.loadFont(CenturyGothic28);
    tft.drawString(line1, tft.width() / 2, tft.height() / 2 - 15);
    tft.drawString(line2, tft.width() / 2, tft.height() / 2 + 15);
    tft.unloadFont(); // Unload font to free up memory
    xSemaphoreGive(tft_mutex);
  }
}

/**
 * @brief Enables or disables the backlight flashing effect.
 *
 * This is used to provide a visual cue when an alarm is ringing.
 *
 * @param enabled True to enable flashing, false to disable.
 */
void Display::setBacklightFlashing(bool enabled)
{
  _isFlashing = enabled;
  if (!_isFlashing)
  {
    // If flashing is disabled, immediately restore the correct brightness
    updateBrightness();
  }
}
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
